ForgetfulDuck/MIP-Watch/MIP-STM32/Core/Inc/lsm6dsr_reg.h

/**
  ******************************************************************************
  * @file    lsm6dsr_reg.h
  * @author  Sensor Solutions Software Team
  * @brief   This file contains all the functions prototypes for the
  *          lsm6dsr_reg.c driver.
  ******************************************************************************
  * @attention
  *
  * Copyright (c) 2021 STMicroelectronics.
  * All rights reserved.
  *
  * This software is licensed under terms that can be found in the LICENSE file
  * in the root directory of this software component.
  * If no LICENSE file comes with this software, it is provided AS-IS.
  *
  ******************************************************************************
  */

/* Define to prevent recursive inclusion -------------------------------------*/
#ifndef LSM6DSR_REGS_H
#define LSM6DSR_REGS_H

#ifdef __cplusplus
extern "C" {
#endif

/* Includes ------------------------------------------------------------------*/
#include <stdint.h>
#include <stddef.h>
#include <math.h>

/** @addtogroup LSM6DSR
  * @{
  *
  */

/** @defgroup  Endianness definitions
  * @{
  *
  */

#ifndef DRV_BYTE_ORDER
#ifndef __BYTE_ORDER__

#define DRV_LITTLE_ENDIAN 1234
#define DRV_BIG_ENDIAN    4321

/** if _BYTE_ORDER is not defined, choose the endianness of your architecture
  * by uncommenting the define which fits your platform endianness
  */
/* #define DRV_BYTE_ORDER    DRV_BIG_ENDIAN */
#define DRV_BYTE_ORDER    DRV_LITTLE_ENDIAN

#else /* defined __BYTE_ORDER__ */

#define DRV_LITTLE_ENDIAN  __ORDER_LITTLE_ENDIAN__
#define DRV_BIG_ENDIAN     __ORDER_BIG_ENDIAN__
#define DRV_BYTE_ORDER     __BYTE_ORDER__

#endif /* __BYTE_ORDER__*/
#endif /* DRV_BYTE_ORDER */

/**
  * @}
  *
  */

/** @defgroup STMicroelectronics sensors common types
  * @{
  *
  */

#ifndef MEMS_SHARED_TYPES
#define MEMS_SHARED_TYPES

typedef struct
{
#if DRV_BYTE_ORDER == DRV_LITTLE_ENDIAN
  uint8_t bit0       : 1;
  uint8_t bit1       : 1;
  uint8_t bit2       : 1;
  uint8_t bit3       : 1;
  uint8_t bit4       : 1;
  uint8_t bit5       : 1;
  uint8_t bit6       : 1;
  uint8_t bit7       : 1;
#elif DRV_BYTE_ORDER == DRV_BIG_ENDIAN
  uint8_t bit7       : 1;
  uint8_t bit6       : 1;
  uint8_t bit5       : 1;
  uint8_t bit4       : 1;
  uint8_t bit3       : 1;
  uint8_t bit2       : 1;
  uint8_t bit1       : 1;
  uint8_t bit0       : 1;
#endif /* DRV_BYTE_ORDER */
} bitwise_t;

#define PROPERTY_DISABLE                (0U)
#define PROPERTY_ENABLE                 (1U)

/** @addtogroup  Interfaces_Functions
  * @brief       This section provide a set of functions used to read and
  *              write a generic register of the device.
  *              MANDATORY: return 0 -> no Error.
  * @{
  *
  */

typedef int32_t (*stmdev_write_ptr)(void *, uint8_t, const uint8_t *, uint16_t);
typedef int32_t (*stmdev_read_ptr)(void *, uint8_t, uint8_t *, uint16_t);
typedef void (*stmdev_mdelay_ptr)(uint32_t millisec);

typedef struct
{
  /** Component mandatory fields **/
  stmdev_write_ptr  write_reg;
  stmdev_read_ptr   read_reg;
  /** Component optional fields **/
  stmdev_mdelay_ptr   mdelay;
  /** Customizable optional pointer **/
  void *handle;

  /** private data **/
  void *priv_data;
} stmdev_ctx_t;

/**
  * @}
  *
  */

#endif /* MEMS_SHARED_TYPES */

/** @defgroup LSM6DSR Infos
  * @{
  *
  */

/** I2C Device Address 8 bit format  if SA0=0 -> 6A becomes D4 if SA0=1 -> 6B becomes D6**/
#define LSM6DSR_I2C_ADD_L                    0xD4U
#define LSM6DSR_I2C_ADD_H                    0xD6U

/** Device Identification (Who am I) **/
#define LSM6DSR_ID                           0x6BU

/**
  * @}
  *
  */

#define LSM6DSR_FUNC_CFG_ACCESS              0x01U
typedef struct
{
#if DRV_BYTE_ORDER == DRV_LITTLE_ENDIAN
  uint8_t not_used_01              : 6;
  uint8_t reg_access               : 2; /* shub_reg_access + func_cfg_access */
#elif DRV_BYTE_ORDER == DRV_BIG_ENDIAN
  uint8_t reg_access               : 2; /* shub_reg_access + func_cfg_access */
  uint8_t not_used_01              : 6;
#endif /* DRV_BYTE_ORDER */
} lsm6dsr_func_cfg_access_t;

#define LSM6DSR_PIN_CTRL                     0x02U
typedef struct
{
#if DRV_BYTE_ORDER == DRV_LITTLE_ENDIAN
  uint8_t not_used_01              : 6;
  uint8_t sdo_pu_en                : 1;
  uint8_t ois_pu_dis               : 1;
#elif DRV_BYTE_ORDER == DRV_BIG_ENDIAN
  uint8_t ois_pu_dis               : 1;
  uint8_t sdo_pu_en                : 1;
  uint8_t not_used_01              : 6;
#endif /* DRV_BYTE_ORDER */
} lsm6dsr_pin_ctrl_t;

#define LSM6DSR_S4S_TPH_L                    0x04U
typedef struct
{
#if DRV_BYTE_ORDER == DRV_LITTLE_ENDIAN
  uint8_t tph_l                    : 7;
  uint8_t tph_h_sel                : 1;
#elif DRV_BYTE_ORDER == DRV_BIG_ENDIAN
  uint8_t tph_h_sel                : 1;
  uint8_t tph_l                    : 7;
#endif /* DRV_BYTE_ORDER */
} lsm6dsr_s4s_tph_l_t;

#define LSM6DSR_S4S_TPH_H                    0x05U
typedef struct
{
  uint8_t tph_h                    : 8;
} lsm6dsr_s4s_tph_h_t;

#define LSM6DSR_S4S_RR                       0x06U
typedef struct
{
#if DRV_BYTE_ORDER == DRV_LITTLE_ENDIAN
  uint8_t rr                       : 2;
  uint8_t not_used_01              : 6;
#elif DRV_BYTE_ORDER == DRV_BIG_ENDIAN
  uint8_t not_used_01              : 6;
  uint8_t rr                       : 2;
#endif /* DRV_BYTE_ORDER */
} lsm6dsr_s4s_rr_t;

#define LSM6DSR_FIFO_CTRL1                   0x07U
typedef struct
{
  uint8_t wtm                      : 8;
} lsm6dsr_fifo_ctrl1_t;

#define LSM6DSR_FIFO_CTRL2                   0x08U
typedef struct
{
#if DRV_BYTE_ORDER == DRV_LITTLE_ENDIAN
  uint8_t wtm                      : 1;
  uint8_t uncoptr_rate             : 2;
  uint8_t not_used_01              : 1;
  uint8_t odrchg_en                : 1;
  uint8_t not_used_02              : 1;
  uint8_t fifo_compr_rt_en         : 1;
  uint8_t stop_on_wtm              : 1;
#elif DRV_BYTE_ORDER == DRV_BIG_ENDIAN
  uint8_t stop_on_wtm              : 1;
  uint8_t fifo_compr_rt_en         : 1;
  uint8_t not_used_02              : 1;
  uint8_t odrchg_en                : 1;
  uint8_t not_used_01              : 1;
  uint8_t uncoptr_rate             : 2;
  uint8_t wtm                      : 1;
#endif /* DRV_BYTE_ORDER */
} lsm6dsr_fifo_ctrl2_t;

#define LSM6DSR_FIFO_CTRL3                   0x09U
typedef struct
{
#if DRV_BYTE_ORDER == DRV_LITTLE_ENDIAN
  uint8_t bdr_xl                   : 4;
  uint8_t bdr_gy                   : 4;
#elif DRV_BYTE_ORDER == DRV_BIG_ENDIAN
  uint8_t bdr_gy                   : 4;
  uint8_t bdr_xl                   : 4;
#endif /* DRV_BYTE_ORDER */
} lsm6dsr_fifo_ctrl3_t;

#define LSM6DSR_FIFO_CTRL4                   0x0AU
typedef struct
{
#if DRV_BYTE_ORDER == DRV_LITTLE_ENDIAN
  uint8_t fifo_mode                : 3;
  uint8_t not_used_01              : 1;
  uint8_t odr_t_batch              : 2;
  uint8_t odr_ts_batch             : 2;
#elif DRV_BYTE_ORDER == DRV_BIG_ENDIAN
  uint8_t odr_ts_batch             : 2;
  uint8_t odr_t_batch              : 2;
  uint8_t not_used_01              : 1;
  uint8_t fifo_mode                : 3;
#endif /* DRV_BYTE_ORDER */
} lsm6dsr_fifo_ctrl4_t;

#define LSM6DSR_COUNTER_BDR_REG1             0x0BU
typedef struct
{
#if DRV_BYTE_ORDER == DRV_LITTLE_ENDIAN
  uint8_t cnt_bdr_th               : 3;
  uint8_t not_used_01              : 2;
  uint8_t trig_counter_bdr         : 1;
  uint8_t rst_counter_bdr          : 1;
  uint8_t dataready_pulsed         : 1;
#elif DRV_BYTE_ORDER == DRV_BIG_ENDIAN
  uint8_t dataready_pulsed         : 1;
  uint8_t rst_counter_bdr          : 1;
  uint8_t trig_counter_bdr         : 1;
  uint8_t not_used_01              : 2;
  uint8_t cnt_bdr_th               : 3;
#endif /* DRV_BYTE_ORDER */
} lsm6dsr_counter_bdr_reg1_t;

#define LSM6DSR_COUNTER_BDR_REG2             0x0CU
typedef struct
{
  uint8_t cnt_bdr_th               : 8;
} lsm6dsr_counter_bdr_reg2_t;

#define LSM6DSR_INT1_CTRL                    0x0DU
typedef struct
{
#if DRV_BYTE_ORDER == DRV_LITTLE_ENDIAN
  uint8_t int1_drdy_xl             : 1;
  uint8_t int1_drdy_g              : 1;
  uint8_t int1_boot                : 1;
  uint8_t int1_fifo_th             : 1;
  uint8_t int1_fifo_ovr            : 1;
  uint8_t int1_fifo_full           : 1;
  uint8_t int1_cnt_bdr             : 1;
  uint8_t den_drdy_flag            : 1;
#elif DRV_BYTE_ORDER == DRV_BIG_ENDIAN
  uint8_t den_drdy_flag            : 1;
  uint8_t int1_cnt_bdr             : 1;
  uint8_t int1_fifo_full           : 1;
  uint8_t int1_fifo_ovr            : 1;
  uint8_t int1_fifo_th             : 1;
  uint8_t int1_boot                : 1;
  uint8_t int1_drdy_g              : 1;
  uint8_t int1_drdy_xl             : 1;
#endif /* DRV_BYTE_ORDER */
} lsm6dsr_int1_ctrl_t;

#define LSM6DSR_INT2_CTRL                    0x0EU
typedef struct
{
#if DRV_BYTE_ORDER == DRV_LITTLE_ENDIAN
  uint8_t int2_drdy_xl             : 1;
  uint8_t int2_drdy_g              : 1;
  uint8_t int2_drdy_temp           : 1;
  uint8_t int2_fifo_th             : 1;
  uint8_t int2_fifo_ovr            : 1;
  uint8_t int2_fifo_full           : 1;
  uint8_t int2_cnt_bdr             : 1;
  uint8_t not_used_01              : 1;
#elif DRV_BYTE_ORDER == DRV_BIG_ENDIAN
  uint8_t not_used_01              : 1;
  uint8_t int2_cnt_bdr             : 1;
  uint8_t int2_fifo_full           : 1;
  uint8_t int2_fifo_ovr            : 1;
  uint8_t int2_fifo_th             : 1;
  uint8_t int2_drdy_temp           : 1;
  uint8_t int2_drdy_g              : 1;
  uint8_t int2_drdy_xl             : 1;
#endif /* DRV_BYTE_ORDER */
} lsm6dsr_int2_ctrl_t;

#define LSM6DSR_WHO_AM_I                     0x0FU
#define LSM6DSR_CTRL1_XL                     0x10U
typedef struct
{
#if DRV_BYTE_ORDER == DRV_LITTLE_ENDIAN
  uint8_t not_used_01              : 1;
  uint8_t lpf2_xl_en               : 1;
  uint8_t fs_xl                    : 2;
  uint8_t odr_xl                   : 4;
#elif DRV_BYTE_ORDER == DRV_BIG_ENDIAN
  uint8_t odr_xl                   : 4;
  uint8_t fs_xl                    : 2;
  uint8_t lpf2_xl_en               : 1;
  uint8_t not_used_01              : 1;
#endif /* DRV_BYTE_ORDER */
} lsm6dsr_ctrl1_xl_t;

#define LSM6DSR_CTRL2_G                      0x11U
typedef struct
{
#if DRV_BYTE_ORDER == DRV_LITTLE_ENDIAN
  uint8_t fs_g                     : 4; /* fs_4000 + fs_125 + fs_g */
  uint8_t odr_g                    : 4;
#elif DRV_BYTE_ORDER == DRV_BIG_ENDIAN
  uint8_t odr_g                    : 4;
  uint8_t fs_g                     : 4; /* fs_4000 + fs_125 + fs_g */
#endif /* DRV_BYTE_ORDER */
} lsm6dsr_ctrl2_g_t;

#define LSM6DSR_CTRL3_C                      0x12U
typedef struct
{
#if DRV_BYTE_ORDER == DRV_LITTLE_ENDIAN
  uint8_t sw_reset                 : 1;
  uint8_t not_used_01              : 1;
  uint8_t if_inc                   : 1;
  uint8_t sim                      : 1;
  uint8_t pp_od                    : 1;
  uint8_t h_lactive                : 1;
  uint8_t bdu                      : 1;
  uint8_t boot                     : 1;
#elif DRV_BYTE_ORDER == DRV_BIG_ENDIAN
  uint8_t boot                     : 1;
  uint8_t bdu                      : 1;
  uint8_t h_lactive                : 1;
  uint8_t pp_od                    : 1;
  uint8_t sim                      : 1;
  uint8_t if_inc                   : 1;
  uint8_t not_used_01              : 1;
  uint8_t sw_reset                 : 1;
#endif /* DRV_BYTE_ORDER */
} lsm6dsr_ctrl3_c_t;

#define LSM6DSR_CTRL4_C                      0x13U
typedef struct
{
#if DRV_BYTE_ORDER == DRV_LITTLE_ENDIAN
  uint8_t not_used_01              : 1;
  uint8_t lpf1_sel_g               : 1;
  uint8_t i2c_disable              : 1;
  uint8_t drdy_mask                : 1;
  uint8_t not_used_02              : 1;
  uint8_t int2_on_int1             : 1;
  uint8_t sleep_g                  : 1;
  uint8_t not_used_03              : 1;
#elif DRV_BYTE_ORDER == DRV_BIG_ENDIAN
  uint8_t not_used_03              : 1;
  uint8_t sleep_g                  : 1;
  uint8_t int2_on_int1             : 1;
  uint8_t not_used_02              : 1;
  uint8_t drdy_mask                : 1;
  uint8_t i2c_disable              : 1;
  uint8_t lpf1_sel_g               : 1;
  uint8_t not_used_01              : 1;
#endif /* DRV_BYTE_ORDER */
} lsm6dsr_ctrl4_c_t;

#define LSM6DSR_CTRL5_C                      0x14U
typedef struct
{
#if DRV_BYTE_ORDER == DRV_LITTLE_ENDIAN
  uint8_t st_xl                    : 2;
  uint8_t st_g                     : 2;
  uint8_t not_used_01              : 1;
  uint8_t rounding                 : 2;
  uint8_t not_used_02              : 1;
#elif DRV_BYTE_ORDER == DRV_BIG_ENDIAN
  uint8_t not_used_02              : 1;
  uint8_t rounding                 : 2;
  uint8_t not_used_01              : 1;
  uint8_t st_g                     : 2;
  uint8_t st_xl                    : 2;
#endif /* DRV_BYTE_ORDER */
} lsm6dsr_ctrl5_c_t;

#define LSM6DSR_CTRL6_C                      0x15U
typedef struct
{
#if DRV_BYTE_ORDER == DRV_LITTLE_ENDIAN
  uint8_t ftype                    : 3;
  uint8_t usr_off_w                : 1;
  uint8_t xl_hm_mode               : 1;
  uint8_t den_mode                 : 3;   /* trig_en + lvl1_en + lvl2_en */
#elif DRV_BYTE_ORDER == DRV_BIG_ENDIAN
  uint8_t den_mode                 : 3;   /* trig_en + lvl1_en + lvl2_en */
  uint8_t xl_hm_mode               : 1;
  uint8_t usr_off_w                : 1;
  uint8_t ftype                    : 3;
#endif /* DRV_BYTE_ORDER */
} lsm6dsr_ctrl6_c_t;

#define LSM6DSR_CTRL7_G                      0x16U
typedef struct
{
#if DRV_BYTE_ORDER == DRV_LITTLE_ENDIAN
  uint8_t ois_on                   : 1;
  uint8_t usr_off_on_out           : 1;
  uint8_t ois_on_en                : 1;
  uint8_t not_used_01              : 1;
  uint8_t hpm_g                    : 2;
  uint8_t hp_en_g                  : 1;
  uint8_t g_hm_mode                : 1;
#elif DRV_BYTE_ORDER == DRV_BIG_ENDIAN
  uint8_t g_hm_mode                : 1;
  uint8_t hp_en_g                  : 1;
  uint8_t hpm_g                    : 2;
  uint8_t not_used_01              : 1;
  uint8_t ois_on_en                : 1;
  uint8_t usr_off_on_out           : 1;
  uint8_t ois_on                   : 1;
#endif /* DRV_BYTE_ORDER */
} lsm6dsr_ctrl7_g_t;

#define LSM6DSR_CTRL8_XL                     0x17U
typedef struct
{
#if DRV_BYTE_ORDER == DRV_LITTLE_ENDIAN
  uint8_t low_pass_on_6d           : 1;
  uint8_t not_used_01              : 1;
  uint8_t hp_slope_xl_en           : 1;
  uint8_t fastsettl_mode_xl        : 1;
  uint8_t hp_ref_mode_xl           : 1;
  uint8_t hpcf_xl                  : 3;
#elif DRV_BYTE_ORDER == DRV_BIG_ENDIAN
  uint8_t hpcf_xl                  : 3;
  uint8_t hp_ref_mode_xl           : 1;
  uint8_t fastsettl_mode_xl        : 1;
  uint8_t hp_slope_xl_en           : 1;
  uint8_t not_used_01              : 1;
  uint8_t low_pass_on_6d           : 1;
#endif /* DRV_BYTE_ORDER */
} lsm6dsr_ctrl8_xl_t;

#define LSM6DSR_CTRL9_XL                     0x18U
typedef struct
{
#if DRV_BYTE_ORDER == DRV_LITTLE_ENDIAN
  uint8_t not_used_01              : 1;
  uint8_t i3c_disable              : 1;
  uint8_t den_lh                   : 1;
  uint8_t den_xl_g                 : 2;   /* den_xl_en + den_xl_g */
  uint8_t den_z                    : 1;
  uint8_t den_y                    : 1;
  uint8_t den_x                    : 1;
#elif DRV_BYTE_ORDER == DRV_BIG_ENDIAN
  uint8_t den_x                    : 1;
  uint8_t den_y                    : 1;
  uint8_t den_z                    : 1;
  uint8_t den_xl_g                 : 2;   /* den_xl_en + den_xl_g */
  uint8_t den_lh                   : 1;
  uint8_t i3c_disable              : 1;
  uint8_t not_used_01              : 1;
#endif /* DRV_BYTE_ORDER */
} lsm6dsr_ctrl9_xl_t;

#define LSM6DSR_CTRL10_C                     0x19U
typedef struct
{
#if DRV_BYTE_ORDER == DRV_LITTLE_ENDIAN
  uint8_t not_used_01              : 5;
  uint8_t timestamp_en             : 1;
  uint8_t not_used_02              : 2;
#elif DRV_BYTE_ORDER == DRV_BIG_ENDIAN
  uint8_t not_used_02              : 2;
  uint8_t timestamp_en             : 1;
  uint8_t not_used_01              : 5;
#endif /* DRV_BYTE_ORDER */
} lsm6dsr_ctrl10_c_t;

#define LSM6DSR_ALL_INT_SRC                  0x1AU
typedef struct
{
#if DRV_BYTE_ORDER == DRV_LITTLE_ENDIAN
  uint8_t ff_ia                    : 1;
  uint8_t wu_ia                    : 1;
  uint8_t single_tap               : 1;
  uint8_t double_tap               : 1;
  uint8_t d6d_ia                   : 1;
  uint8_t sleep_change_ia          : 1;
  uint8_t not_used_01              : 1;
  uint8_t timestamp_endcount       : 1;
#elif DRV_BYTE_ORDER == DRV_BIG_ENDIAN
  uint8_t timestamp_endcount       : 1;
  uint8_t not_used_01              : 1;
  uint8_t sleep_change_ia          : 1;
  uint8_t d6d_ia                   : 1;
  uint8_t double_tap               : 1;
  uint8_t single_tap               : 1;
  uint8_t wu_ia                    : 1;
  uint8_t ff_ia                    : 1;
#endif /* DRV_BYTE_ORDER */
} lsm6dsr_all_int_src_t;

#define LSM6DSR_WAKE_UP_SRC                  0x1BU
typedef struct
{
#if DRV_BYTE_ORDER == DRV_LITTLE_ENDIAN
  uint8_t z_wu                     : 1;
  uint8_t y_wu                     : 1;
  uint8_t x_wu                     : 1;
  uint8_t wu_ia                    : 1;
  uint8_t sleep_state              : 1;
  uint8_t ff_ia                    : 1;
  uint8_t sleep_change_ia          : 1;
  uint8_t not_used_01              : 1;
#elif DRV_BYTE_ORDER == DRV_BIG_ENDIAN
  uint8_t not_used_01              : 1;
  uint8_t sleep_change_ia          : 1;
  uint8_t ff_ia                    : 1;
  uint8_t sleep_state              : 1;
  uint8_t wu_ia                    : 1;
  uint8_t x_wu                     : 1;
  uint8_t y_wu                     : 1;
  uint8_t z_wu                     : 1;
#endif /* DRV_BYTE_ORDER */
} lsm6dsr_wake_up_src_t;

#define LSM6DSR_TAP_SRC                      0x1CU
typedef struct
{
#if DRV_BYTE_ORDER == DRV_LITTLE_ENDIAN
  uint8_t z_tap                    : 1;
  uint8_t y_tap                    : 1;
  uint8_t x_tap                    : 1;
  uint8_t tap_sign                 : 1;
  uint8_t double_tap               : 1;
  uint8_t single_tap               : 1;
  uint8_t tap_ia                   : 1;
  uint8_t not_used_01              : 1;
#elif DRV_BYTE_ORDER == DRV_BIG_ENDIAN
  uint8_t not_used_01              : 1;
  uint8_t tap_ia                   : 1;
  uint8_t single_tap               : 1;
  uint8_t double_tap               : 1;
  uint8_t tap_sign                 : 1;
  uint8_t x_tap                    : 1;
  uint8_t y_tap                    : 1;
  uint8_t z_tap                    : 1;
#endif /* DRV_BYTE_ORDER */
} lsm6dsr_tap_src_t;

#define LSM6DSR_D6D_SRC                      0x1DU
typedef struct
{
#if DRV_BYTE_ORDER == DRV_LITTLE_ENDIAN
  uint8_t xl                       : 1;
  uint8_t xh                       : 1;
  uint8_t yl                       : 1;
  uint8_t yh                       : 1;
  uint8_t zl                       : 1;
  uint8_t zh                       : 1;
  uint8_t d6d_ia                   : 1;
  uint8_t den_drdy                 : 1;
#elif DRV_BYTE_ORDER == DRV_BIG_ENDIAN
  uint8_t den_drdy                 : 1;
  uint8_t d6d_ia                   : 1;
  uint8_t zh                       : 1;
  uint8_t zl                       : 1;
  uint8_t yh                       : 1;
  uint8_t yl                       : 1;
  uint8_t xh                       : 1;
  uint8_t xl                       : 1;
#endif /* DRV_BYTE_ORDER */
} lsm6dsr_d6d_src_t;

#define LSM6DSR_STATUS_REG                   0x1EU
typedef struct
{
#if DRV_BYTE_ORDER == DRV_LITTLE_ENDIAN
  uint8_t xlda                     : 1;
  uint8_t gda                      : 1;
  uint8_t tda                      : 1;
  uint8_t not_used_01              : 5;
#elif DRV_BYTE_ORDER == DRV_BIG_ENDIAN
  uint8_t not_used_01              : 5;
  uint8_t tda                      : 1;
  uint8_t gda                      : 1;
  uint8_t xlda                     : 1;
#endif /* DRV_BYTE_ORDER */
} lsm6dsr_status_reg_t;

#define LSM6DSR_STATUS_SPIAUX                0x1EU
typedef struct
{
#if DRV_BYTE_ORDER == DRV_LITTLE_ENDIAN
  uint8_t xlda                     : 1;
  uint8_t gda                      : 1;
  uint8_t gyro_settling            : 1;
  uint8_t not_used_01              : 5;
#elif DRV_BYTE_ORDER == DRV_BIG_ENDIAN
  uint8_t not_used_01              : 5;
  uint8_t gyro_settling            : 1;
  uint8_t gda                      : 1;
  uint8_t xlda                     : 1;
#endif /* DRV_BYTE_ORDER */
} lsm6dsr_status_spiaux_t;

#define LSM6DSR_OUT_TEMP_L                   0x20U
#define LSM6DSR_OUT_TEMP_H                   0x21U
#define LSM6DSR_OUTX_L_G                     0x22U
#define LSM6DSR_OUTX_H_G                     0x23U
#define LSM6DSR_OUTY_L_G                     0x24U
#define LSM6DSR_OUTY_H_G                     0x25U
#define LSM6DSR_OUTZ_L_G                     0x26U
#define LSM6DSR_OUTZ_H_G                     0x27U
#define LSM6DSR_OUTX_L_A                     0x28U
#define LSM6DSR_OUTX_H_A                     0x29U
#define LSM6DSR_OUTY_L_A                     0x2AU
#define LSM6DSR_OUTY_H_A                     0x2BU
#define LSM6DSR_OUTZ_L_A                     0x2CU
#define LSM6DSR_OUTZ_H_A                     0x2DU

#define LSM6DSR_EMB_FUNC_STATUS_MAINPAGE     0x35U
typedef struct
{
#if DRV_BYTE_ORDER == DRV_LITTLE_ENDIAN
  uint8_t not_used_01             : 3;
  uint8_t is_step_det             : 1;
  uint8_t is_tilt                 : 1;
  uint8_t is_sigmot               : 1;
  uint8_t not_used_02             : 1;
  uint8_t is_fsm_lc               : 1;
#elif DRV_BYTE_ORDER == DRV_BIG_ENDIAN
  uint8_t is_fsm_lc               : 1;
  uint8_t not_used_02             : 1;
  uint8_t is_sigmot               : 1;
  uint8_t is_tilt                 : 1;
  uint8_t is_step_det             : 1;
  uint8_t not_used_01             : 3;
#endif /* DRV_BYTE_ORDER */
} lsm6dsr_emb_func_status_mainpage_t;

#define LSM6DSR_FSM_STATUS_A_MAINPAGE        0x36U
typedef struct
{
#if DRV_BYTE_ORDER == DRV_LITTLE_ENDIAN
  uint8_t is_fsm1                 : 1;
  uint8_t is_fsm2                 : 1;
  uint8_t is_fsm3                 : 1;
  uint8_t is_fsm4                 : 1;
  uint8_t is_fsm5                 : 1;
  uint8_t is_fsm6                 : 1;
  uint8_t is_fsm7                 : 1;
  uint8_t is_fsm8                 : 1;
#elif DRV_BYTE_ORDER == DRV_BIG_ENDIAN
  uint8_t is_fsm8                 : 1;
  uint8_t is_fsm7                 : 1;
  uint8_t is_fsm6                 : 1;
  uint8_t is_fsm5                 : 1;
  uint8_t is_fsm4                 : 1;
  uint8_t is_fsm3                 : 1;
  uint8_t is_fsm2                 : 1;
  uint8_t is_fsm1                 : 1;
#endif /* DRV_BYTE_ORDER */
} lsm6dsr_fsm_status_a_mainpage_t;

#define LSM6DSR_FSM_STATUS_B_MAINPAGE        0x37U
typedef struct
{
#if DRV_BYTE_ORDER == DRV_LITTLE_ENDIAN
  uint8_t is_fsm9                 : 1;
  uint8_t is_fsm10                : 1;
  uint8_t is_fsm11                : 1;
  uint8_t is_fsm12                : 1;
  uint8_t is_fsm13                : 1;
  uint8_t is_fsm14                : 1;
  uint8_t is_fsm15                : 1;
  uint8_t is_fsm16                : 1;
#elif DRV_BYTE_ORDER == DRV_BIG_ENDIAN
  uint8_t is_fsm16                : 1;
  uint8_t is_fsm15                : 1;
  uint8_t is_fsm14                : 1;
  uint8_t is_fsm13                : 1;
  uint8_t is_fsm12                : 1;
  uint8_t is_fsm11                : 1;
  uint8_t is_fsm10                : 1;
  uint8_t is_fsm9                 : 1;
#endif /* DRV_BYTE_ORDER */
} lsm6dsr_fsm_status_b_mainpage_t;

#define LSM6DSR_STATUS_MASTER_MAINPAGE       0x39U
typedef struct
{
#if DRV_BYTE_ORDER == DRV_LITTLE_ENDIAN
  uint8_t sens_hub_endop          : 1;
  uint8_t not_used_01             : 2;
  uint8_t slave0_nack             : 1;
  uint8_t slave1_nack             : 1;
  uint8_t slave2_nack             : 1;
  uint8_t slave3_nack             : 1;
  uint8_t wr_once_done            : 1;
#elif DRV_BYTE_ORDER == DRV_BIG_ENDIAN
  uint8_t wr_once_done            : 1;
  uint8_t slave3_nack             : 1;
  uint8_t slave2_nack             : 1;
  uint8_t slave1_nack             : 1;
  uint8_t slave0_nack             : 1;
  uint8_t not_used_01             : 2;
  uint8_t sens_hub_endop          : 1;
#endif /* DRV_BYTE_ORDER */
} lsm6dsr_status_master_mainpage_t;

#define LSM6DSR_FIFO_STATUS1                 0x3AU
typedef struct
{
  uint8_t diff_fifo                : 8;
} lsm6dsr_fifo_status1_t;

#define LSM6DSR_FIFO_STATUS2                 0x3BU
typedef struct
{
#if DRV_BYTE_ORDER == DRV_LITTLE_ENDIAN
  uint8_t diff_fifo                : 2;
  uint8_t not_used_01              : 1;
  uint8_t over_run_latched         : 1;
  uint8_t counter_bdr_ia           : 1;
  uint8_t fifo_full_ia             : 1;
  uint8_t fifo_ovr_ia              : 1;
  uint8_t fifo_wtm_ia              : 1;
#elif DRV_BYTE_ORDER == DRV_BIG_ENDIAN
  uint8_t fifo_wtm_ia              : 1;
  uint8_t fifo_ovr_ia              : 1;
  uint8_t fifo_full_ia             : 1;
  uint8_t counter_bdr_ia           : 1;
  uint8_t over_run_latched         : 1;
  uint8_t not_used_01              : 1;
  uint8_t diff_fifo                : 2;
#endif /* DRV_BYTE_ORDER */
} lsm6dsr_fifo_status2_t;

#define LSM6DSR_TIMESTAMP0                   0x40U
#define LSM6DSR_TIMESTAMP1                   0x41U
#define LSM6DSR_TIMESTAMP2                   0x42U
#define LSM6DSR_TIMESTAMP3                   0x43U
#define LSM6DSR_TAP_CFG0                     0x56U
typedef struct
{
#if DRV_BYTE_ORDER == DRV_LITTLE_ENDIAN
  uint8_t lir                      : 1;
  uint8_t tap_z_en                 : 1;
  uint8_t tap_y_en                 : 1;
  uint8_t tap_x_en                 : 1;
  uint8_t slope_fds                : 1;
  uint8_t sleep_status_on_int      : 1;
  uint8_t int_clr_on_read          : 1;
  uint8_t not_used_01              : 1;
#elif DRV_BYTE_ORDER == DRV_BIG_ENDIAN
  uint8_t not_used_01              : 1;
  uint8_t int_clr_on_read          : 1;
  uint8_t sleep_status_on_int      : 1;
  uint8_t slope_fds                : 1;
  uint8_t tap_x_en                 : 1;
  uint8_t tap_y_en                 : 1;
  uint8_t tap_z_en                 : 1;
  uint8_t lir                      : 1;
#endif /* DRV_BYTE_ORDER */
} lsm6dsr_tap_cfg0_t;

#define LSM6DSR_TAP_CFG1                     0x57U
typedef struct
{
#if DRV_BYTE_ORDER == DRV_LITTLE_ENDIAN
  uint8_t tap_ths_x                : 5;
  uint8_t tap_priority             : 3;
#elif DRV_BYTE_ORDER == DRV_BIG_ENDIAN
  uint8_t tap_priority             : 3;
  uint8_t tap_ths_x                : 5;
#endif /* DRV_BYTE_ORDER */
} lsm6dsr_tap_cfg1_t;

#define LSM6DSR_TAP_CFG2                     0x58U
typedef struct
{
#if DRV_BYTE_ORDER == DRV_LITTLE_ENDIAN
  uint8_t tap_ths_y                : 5;
  uint8_t inact_en                 : 2;
  uint8_t interrupts_enable        : 1;
#elif DRV_BYTE_ORDER == DRV_BIG_ENDIAN
  uint8_t interrupts_enable        : 1;
  uint8_t inact_en                 : 2;
  uint8_t tap_ths_y                : 5;
#endif /* DRV_BYTE_ORDER */
} lsm6dsr_tap_cfg2_t;

#define LSM6DSR_TAP_THS_6D                   0x59U
typedef struct
{
#if DRV_BYTE_ORDER == DRV_LITTLE_ENDIAN
  uint8_t tap_ths_z                : 5;
  uint8_t sixd_ths                 : 2;
  uint8_t d4d_en                   : 1;
#elif DRV_BYTE_ORDER == DRV_BIG_ENDIAN
  uint8_t d4d_en                   : 1;
  uint8_t sixd_ths                 : 2;
  uint8_t tap_ths_z                : 5;
#endif /* DRV_BYTE_ORDER */
} lsm6dsr_tap_ths_6d_t;

#define LSM6DSR_INT_DUR2                     0x5AU
typedef struct
{
#if DRV_BYTE_ORDER == DRV_LITTLE_ENDIAN
  uint8_t shock                    : 2;
  uint8_t quiet                    : 2;
  uint8_t dur                      : 4;
#elif DRV_BYTE_ORDER == DRV_BIG_ENDIAN
  uint8_t dur                      : 4;
  uint8_t quiet                    : 2;
  uint8_t shock                    : 2;
#endif /* DRV_BYTE_ORDER */
} lsm6dsr_int_dur2_t;

#define LSM6DSR_WAKE_UP_THS                  0x5BU
typedef struct
{
#if DRV_BYTE_ORDER == DRV_LITTLE_ENDIAN
  uint8_t wk_ths                   : 6;
  uint8_t usr_off_on_wu            : 1;
  uint8_t single_double_tap        : 1;
#elif DRV_BYTE_ORDER == DRV_BIG_ENDIAN
  uint8_t single_double_tap        : 1;
  uint8_t usr_off_on_wu            : 1;
  uint8_t wk_ths                   : 6;
#endif /* DRV_BYTE_ORDER */
} lsm6dsr_wake_up_ths_t;

#define LSM6DSR_WAKE_UP_DUR                  0x5CU
typedef struct
{
#if DRV_BYTE_ORDER == DRV_LITTLE_ENDIAN
  uint8_t sleep_dur                : 4;
  uint8_t wake_ths_w               : 1;
  uint8_t wake_dur                 : 2;
  uint8_t ff_dur                   : 1;
#elif DRV_BYTE_ORDER == DRV_BIG_ENDIAN
  uint8_t ff_dur                   : 1;
  uint8_t wake_dur                 : 2;
  uint8_t wake_ths_w               : 1;
  uint8_t sleep_dur                : 4;
#endif /* DRV_BYTE_ORDER */
} lsm6dsr_wake_up_dur_t;

#define LSM6DSR_FREE_FALL                    0x5DU
typedef struct
{
#if DRV_BYTE_ORDER == DRV_LITTLE_ENDIAN
  uint8_t ff_ths                   : 3;
  uint8_t ff_dur                   : 5;
#elif DRV_BYTE_ORDER == DRV_BIG_ENDIAN
  uint8_t ff_dur                   : 5;
  uint8_t ff_ths                   : 3;
#endif /* DRV_BYTE_ORDER */
} lsm6dsr_free_fall_t;

#define LSM6DSR_MD1_CFG                      0x5EU
typedef struct
{
#if DRV_BYTE_ORDER == DRV_LITTLE_ENDIAN
  uint8_t int1_shub                : 1;
  uint8_t int1_emb_func            : 1;
  uint8_t int1_6d                  : 1;
  uint8_t int1_double_tap          : 1;
  uint8_t int1_ff                  : 1;
  uint8_t int1_wu                  : 1;
  uint8_t int1_single_tap          : 1;
  uint8_t int1_sleep_change        : 1;
#elif DRV_BYTE_ORDER == DRV_BIG_ENDIAN
  uint8_t int1_sleep_change        : 1;
  uint8_t int1_single_tap          : 1;
  uint8_t int1_wu                  : 1;
  uint8_t int1_ff                  : 1;
  uint8_t int1_double_tap          : 1;
  uint8_t int1_6d                  : 1;
  uint8_t int1_emb_func            : 1;
  uint8_t int1_shub                : 1;
#endif /* DRV_BYTE_ORDER */
} lsm6dsr_md1_cfg_t;

#define LSM6DSR_MD2_CFG                      0x5FU
typedef struct
{
#if DRV_BYTE_ORDER == DRV_LITTLE_ENDIAN
  uint8_t int2_timestamp           : 1;
  uint8_t int2_emb_func            : 1;
  uint8_t int2_6d                  : 1;
  uint8_t int2_double_tap          : 1;
  uint8_t int2_ff                  : 1;
  uint8_t int2_wu                  : 1;
  uint8_t int2_single_tap          : 1;
  uint8_t int2_sleep_change        : 1;
#elif DRV_BYTE_ORDER == DRV_BIG_ENDIAN
  uint8_t int2_sleep_change        : 1;
  uint8_t int2_single_tap          : 1;
  uint8_t int2_wu                  : 1;
  uint8_t int2_ff                  : 1;
  uint8_t int2_double_tap          : 1;
  uint8_t int2_6d                  : 1;
  uint8_t int2_emb_func            : 1;
  uint8_t int2_timestamp           : 1;
#endif /* DRV_BYTE_ORDER */
} lsm6dsr_md2_cfg_t;

#define LSM6DSR_S4S_ST_CMD_CODE              0x60U
typedef struct
{
  uint8_t s4s_st_cmd_code          : 8;
} lsm6dsr_s4s_st_cmd_code_t;

#define LSM6DSR_S4S_DT_REG                   0x61U
typedef struct
{
  uint8_t dt                       : 8;
} lsm6dsr_s4s_dt_reg_t;

#define LSM6DSR_I3C_BUS_AVB                  0x62U
typedef struct
{
#if DRV_BYTE_ORDER == DRV_LITTLE_ENDIAN
  uint8_t pd_dis_int1              : 1;
  uint8_t not_used_01              : 2;
  uint8_t i3c_bus_avb_sel          : 2;
  uint8_t not_used_02              : 3;
#elif DRV_BYTE_ORDER == DRV_BIG_ENDIAN
  uint8_t not_used_02              : 3;
  uint8_t i3c_bus_avb_sel          : 2;
  uint8_t not_used_01              : 2;
  uint8_t pd_dis_int1              : 1;
#endif /* DRV_BYTE_ORDER */
} lsm6dsr_i3c_bus_avb_t;

#define LSM6DSR_INTERNAL_FREQ_FINE           0x63U
typedef struct
{
  uint8_t freq_fine                : 8;
} lsm6dsr_internal_freq_fine_t;

#define LSM6DSR_INT_OIS                      0x6FU
typedef struct
{
#if DRV_BYTE_ORDER == DRV_LITTLE_ENDIAN
  uint8_t st_xl_ois                : 2;
  uint8_t not_used_01              : 3;
  uint8_t den_lh_ois               : 1;
  uint8_t lvl2_ois                 : 1;
  uint8_t int2_drdy_ois            : 1;
#elif DRV_BYTE_ORDER == DRV_BIG_ENDIAN
  uint8_t int2_drdy_ois            : 1;
  uint8_t lvl2_ois                 : 1;
  uint8_t den_lh_ois               : 1;
  uint8_t not_used_01              : 3;
  uint8_t st_xl_ois                : 2;
#endif /* DRV_BYTE_ORDER */
} lsm6dsr_int_ois_t;

#define LSM6DSR_CTRL1_OIS                    0x70U
typedef struct
{
#if DRV_BYTE_ORDER == DRV_LITTLE_ENDIAN
  uint8_t ois_en_spi2              : 1;
  uint8_t fs_125_ois               : 1;
  uint8_t fs_g_ois                 : 2;
  uint8_t mode4_en                 : 1;
  uint8_t sim_ois                  : 1;
  uint8_t lvl1_ois                 : 1;
  uint8_t not_used_01              : 1;
#elif DRV_BYTE_ORDER == DRV_BIG_ENDIAN
  uint8_t not_used_01              : 1;
  uint8_t lvl1_ois                 : 1;
  uint8_t sim_ois                  : 1;
  uint8_t mode4_en                 : 1;
  uint8_t fs_g_ois                 : 2;
  uint8_t fs_125_ois               : 1;
  uint8_t ois_en_spi2              : 1;
#endif /* DRV_BYTE_ORDER */
} lsm6dsr_ctrl1_ois_t;

#define LSM6DSR_CTRL2_OIS                    0x71U
typedef struct
{
#if DRV_BYTE_ORDER == DRV_LITTLE_ENDIAN
  uint8_t hp_en_ois                : 1;
  uint8_t ftype_ois                : 2;
  uint8_t not_used_01              : 1;
  uint8_t hpm_ois                  : 2;
  uint8_t not_used_02              : 2;
#elif DRV_BYTE_ORDER == DRV_BIG_ENDIAN
  uint8_t not_used_02              : 2;
  uint8_t hpm_ois                  : 2;
  uint8_t not_used_01              : 1;
  uint8_t ftype_ois                : 2;
  uint8_t hp_en_ois                : 1;
#endif /* DRV_BYTE_ORDER */
} lsm6dsr_ctrl2_ois_t;

#define LSM6DSR_CTRL3_OIS                    0x72U
typedef struct
{
#if DRV_BYTE_ORDER == DRV_LITTLE_ENDIAN
  uint8_t st_ois_clampdis          : 1;
  uint8_t st_ois                   : 2;
  uint8_t filter_xl_conf_ois       : 3;
  uint8_t fs_xl_ois                : 2;
#elif DRV_BYTE_ORDER == DRV_BIG_ENDIAN
  uint8_t fs_xl_ois                : 2;
  uint8_t filter_xl_conf_ois       : 3;
  uint8_t st_ois                   : 2;
  uint8_t st_ois_clampdis          : 1;
#endif /* DRV_BYTE_ORDER */
} lsm6dsr_ctrl3_ois_t;

#define LSM6DSR_X_OFS_USR                    0x73U
#define LSM6DSR_Y_OFS_USR                    0x74U
#define LSM6DSR_Z_OFS_USR                    0x75U
#define LSM6DSR_FIFO_DATA_OUT_TAG            0x78U
typedef struct
{
#if DRV_BYTE_ORDER == DRV_LITTLE_ENDIAN
  uint8_t tag_parity               : 1;
  uint8_t tag_cnt                  : 2;
  uint8_t tag_sensor               : 5;
#elif DRV_BYTE_ORDER == DRV_BIG_ENDIAN
  uint8_t tag_sensor               : 5;
  uint8_t tag_cnt                  : 2;
  uint8_t tag_parity               : 1;
#endif /* DRV_BYTE_ORDER */
} lsm6dsr_fifo_data_out_tag_t;

#define LSM6DSR_FIFO_DATA_OUT_X_L            0x79U
#define LSM6DSR_FIFO_DATA_OUT_X_H            0x7AU
#define LSM6DSR_FIFO_DATA_OUT_Y_L            0x7BU
#define LSM6DSR_FIFO_DATA_OUT_Y_H            0x7CU
#define LSM6DSR_FIFO_DATA_OUT_Z_L            0x7DU
#define LSM6DSR_FIFO_DATA_OUT_Z_H            0x7EU
#define LSM6DSR_PAGE_SEL                     0x02U
typedef struct
{
#if DRV_BYTE_ORDER == DRV_LITTLE_ENDIAN
  uint8_t not_used_01              : 4;
  uint8_t page_sel                 : 4;
#elif DRV_BYTE_ORDER == DRV_BIG_ENDIAN
  uint8_t page_sel                 : 4;
  uint8_t not_used_01              : 4;
#endif /* DRV_BYTE_ORDER */
} lsm6dsr_page_sel_t;

#define LSM6DSR_ADV_PEDO                     0x03U
typedef struct
{
#if DRV_BYTE_ORDER == DRV_LITTLE_ENDIAN
  uint8_t not_used_01              : 1;
  uint8_t pedo_fpr_adf_dis         : 1;
  uint8_t not_used_02              : 6;
#elif DRV_BYTE_ORDER == DRV_BIG_ENDIAN
  uint8_t not_used_02              : 6;
  uint8_t pedo_fpr_adf_dis         : 1;
  uint8_t not_used_01              : 1;
#endif /* DRV_BYTE_ORDER */
} lsm6dsr_adv_pedo_t;

#define LSM6DSR_EMB_FUNC_EN_A                0x04U
typedef struct
{
#if DRV_BYTE_ORDER == DRV_LITTLE_ENDIAN
  uint8_t not_used_01              : 3;
  uint8_t pedo_en                  : 1;
  uint8_t tilt_en                  : 1;
  uint8_t sign_motion_en           : 1;
  uint8_t not_used_02              : 2;
#elif DRV_BYTE_ORDER == DRV_BIG_ENDIAN
  uint8_t not_used_02              : 2;
  uint8_t sign_motion_en           : 1;
  uint8_t tilt_en                  : 1;
  uint8_t pedo_en                  : 1;
  uint8_t not_used_01              : 3;
#endif /* DRV_BYTE_ORDER */
} lsm6dsr_emb_func_en_a_t;

#define LSM6DSR_EMB_FUNC_EN_B                0x05U
typedef struct
{
#if DRV_BYTE_ORDER == DRV_LITTLE_ENDIAN
  uint8_t fsm_en                   : 1;
  uint8_t not_used_01              : 2;
  uint8_t fifo_compr_en            : 1;
  uint8_t pedo_adv_en              : 1;
  uint8_t not_used_02              : 3;
#elif DRV_BYTE_ORDER == DRV_BIG_ENDIAN
  uint8_t not_used_02              : 3;
  uint8_t pedo_adv_en              : 1;
  uint8_t fifo_compr_en            : 1;
  uint8_t not_used_01              : 2;
  uint8_t fsm_en                   : 1;
#endif /* DRV_BYTE_ORDER */
} lsm6dsr_emb_func_en_b_t;

#define LSM6DSR_PAGE_ADDRESS                 0x08U
typedef struct
{
  uint8_t page_addr                : 8;
} lsm6dsr_page_address_t;

#define LSM6DSR_PAGE_VALUE                   0x09U
typedef struct
{
  uint8_t page_value               : 8;
} lsm6dsr_page_value_t;

#define LSM6DSR_EMB_FUNC_INT1                0x0AU
typedef struct
{
#if DRV_BYTE_ORDER == DRV_LITTLE_ENDIAN
  uint8_t not_used_01              : 3;
  uint8_t int1_step_detector       : 1;
  uint8_t int1_tilt                : 1;
  uint8_t int1_sig_mot             : 1;
  uint8_t not_used_02              : 1;
  uint8_t int1_fsm_lc              : 1;
#elif DRV_BYTE_ORDER == DRV_BIG_ENDIAN
  uint8_t int1_fsm_lc              : 1;
  uint8_t not_used_02              : 1;
  uint8_t int1_sig_mot             : 1;
  uint8_t int1_tilt                : 1;
  uint8_t int1_step_detector       : 1;
  uint8_t not_used_01              : 3;
#endif /* DRV_BYTE_ORDER */
} lsm6dsr_emb_func_int1_t;

#define LSM6DSR_FSM_INT1_A                   0x0BU
typedef struct
{
#if DRV_BYTE_ORDER == DRV_LITTLE_ENDIAN
  uint8_t int1_fsm1                : 1;
  uint8_t int1_fsm2                : 1;
  uint8_t int1_fsm3                : 1;
  uint8_t int1_fsm4                : 1;
  uint8_t int1_fsm5                : 1;
  uint8_t int1_fsm6                : 1;
  uint8_t int1_fsm7                : 1;
  uint8_t int1_fsm8                : 1;
#elif DRV_BYTE_ORDER == DRV_BIG_ENDIAN
  uint8_t int1_fsm8                : 1;
  uint8_t int1_fsm7                : 1;
  uint8_t int1_fsm6                : 1;
  uint8_t int1_fsm5                : 1;
  uint8_t int1_fsm4                : 1;
  uint8_t int1_fsm3                : 1;
  uint8_t int1_fsm2                : 1;
  uint8_t int1_fsm1                : 1;
#endif /* DRV_BYTE_ORDER */
} lsm6dsr_fsm_int1_a_t;

#define LSM6DSR_FSM_INT1_B                   0x0CU
typedef struct
{
#if DRV_BYTE_ORDER == DRV_LITTLE_ENDIAN
  uint8_t int1_fsm9                : 1;
  uint8_t int1_fsm10               : 1;
  uint8_t int1_fsm11               : 1;
  uint8_t int1_fsm12               : 1;
  uint8_t int1_fsm13               : 1;
  uint8_t int1_fsm14               : 1;
  uint8_t int1_fsm15               : 1;
  uint8_t int1_fsm16               : 1;
#elif DRV_BYTE_ORDER == DRV_BIG_ENDIAN
  uint8_t int1_fsm16               : 1;
  uint8_t int1_fsm15               : 1;
  uint8_t int1_fsm14               : 1;
  uint8_t int1_fsm13               : 1;
  uint8_t int1_fsm12               : 1;
  uint8_t int1_fsm11               : 1;
  uint8_t int1_fsm10               : 1;
  uint8_t int1_fsm9                : 1;
#endif /* DRV_BYTE_ORDER */
} lsm6dsr_fsm_int1_b_t;

#define LSM6DSR_EMB_FUNC_INT2                0x0EU
typedef struct
{
#if DRV_BYTE_ORDER == DRV_LITTLE_ENDIAN
  uint8_t not_used_01              : 3;
  uint8_t int2_step_detector       : 1;
  uint8_t int2_tilt                : 1;
  uint8_t int2_sig_mot             : 1;
  uint8_t not_used_02              : 1;
  uint8_t int2_fsm_lc              : 1;
#elif DRV_BYTE_ORDER == DRV_BIG_ENDIAN
  uint8_t int2_fsm_lc              : 1;
  uint8_t not_used_02              : 1;
  uint8_t int2_sig_mot             : 1;
  uint8_t int2_tilt                : 1;
  uint8_t int2_step_detector       : 1;
  uint8_t not_used_01              : 3;
#endif /* DRV_BYTE_ORDER */
} lsm6dsr_emb_func_int2_t;

#define LSM6DSR_FSM_INT2_A                   0x0FU
typedef struct
{
#if DRV_BYTE_ORDER == DRV_LITTLE_ENDIAN
  uint8_t int2_fsm1                : 1;
  uint8_t int2_fsm2                : 1;
  uint8_t int2_fsm3                : 1;
  uint8_t int2_fsm4                : 1;
  uint8_t int2_fsm5                : 1;
  uint8_t int2_fsm6                : 1;
  uint8_t int2_fsm7                : 1;
  uint8_t int2_fsm8                : 1;
#elif DRV_BYTE_ORDER == DRV_BIG_ENDIAN
  uint8_t int2_fsm8                : 1;
  uint8_t int2_fsm7                : 1;
  uint8_t int2_fsm6                : 1;
  uint8_t int2_fsm5                : 1;
  uint8_t int2_fsm4                : 1;
  uint8_t int2_fsm3                : 1;
  uint8_t int2_fsm2                : 1;
  uint8_t int2_fsm1                : 1;
#endif /* DRV_BYTE_ORDER */
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
  uint8_t p_y                      : 1;
  uint8_t n_y                      : 1;
  uint8_t p_z                      : 1;
  uint8_t n_z                      : 1;
  uint8_t p_v                      : 1;
  uint8_t n_v                      : 1;
#endif /* DRV_BYTE_ORDER */
} lsm6dsr_fsm_outs15_t;

#define LSM6DSR_FSM_OUTS16                   0x5BU
typedef struct
{
#if DRV_BYTE_ORDER == DRV_LITTLE_ENDIAN
  uint8_t n_v                      : 1;
  uint8_t p_v                      : 1;
  uint8_t n_z                      : 1;
  uint8_t p_z                      : 1;
  uint8_t n_y                      : 1;
  uint8_t p_y                      : 1;
  uint8_t n_x                      : 1;
  uint8_t p_x                      : 1;
#elif DRV_BYTE_ORDER == DRV_BIG_ENDIAN
  uint8_t p_x                      : 1;
  uint8_t n_x                      : 1;
  uint8_t p_y                      : 1;
  uint8_t n_y                      : 1;
  uint8_t p_z                      : 1;
  uint8_t n_z                      : 1;
  uint8_t p_v                      : 1;
  uint8_t n_v                      : 1;
#endif /* DRV_BYTE_ORDER */
} lsm6dsr_fsm_outs16_t;

#define LSM6DSR_EMB_FUNC_ODR_CFG_B           0x5FU
typedef struct
{
#if DRV_BYTE_ORDER == DRV_LITTLE_ENDIAN
  uint8_t not_used_01              : 3;
  uint8_t fsm_odr                  : 2;
  uint8_t not_used_02              : 3;
#elif DRV_BYTE_ORDER == DRV_BIG_ENDIAN
  uint8_t not_used_02              : 3;
  uint8_t fsm_odr                  : 2;
  uint8_t not_used_01              : 3;
#endif /* DRV_BYTE_ORDER */
} lsm6dsr_emb_func_odr_cfg_b_t;

#define LSM6DSR_STEP_COUNTER_L               0x62U
#define LSM6DSR_STEP_COUNTER_H               0x63U
#define LSM6DSR_EMB_FUNC_SRC                 0x64U
typedef struct
{
#if DRV_BYTE_ORDER == DRV_LITTLE_ENDIAN
  uint8_t not_used_01              : 2;
  uint8_t stepcounter_bit_set      : 1;
  uint8_t step_overflow            : 1;
  uint8_t step_count_delta_ia      : 1;
  uint8_t step_detected            : 1;
  uint8_t not_used_02              : 1;
  uint8_t pedo_rst_step            : 1;
#elif DRV_BYTE_ORDER == DRV_BIG_ENDIAN
  uint8_t pedo_rst_step            : 1;
  uint8_t not_used_02              : 1;
  uint8_t step_detected            : 1;
  uint8_t step_count_delta_ia      : 1;
  uint8_t step_overflow            : 1;
  uint8_t stepcounter_bit_set      : 1;
  uint8_t not_used_01              : 2;
#endif /* DRV_BYTE_ORDER */
} lsm6dsr_emb_func_src_t;

#define LSM6DSR_EMB_FUNC_INIT_A              0x66U
typedef struct
{
#if DRV_BYTE_ORDER == DRV_LITTLE_ENDIAN
  uint8_t not_used_01               : 3;
  uint8_t step_det_init             : 1;
  uint8_t tilt_init                 : 1;
  uint8_t sig_mot_init              : 1;
  uint8_t not_used_02               : 2;
#elif DRV_BYTE_ORDER == DRV_BIG_ENDIAN
  uint8_t not_used_02               : 2;
  uint8_t sig_mot_init              : 1;
  uint8_t tilt_init                 : 1;
  uint8_t step_det_init             : 1;
  uint8_t not_used_01               : 3;
#endif /* DRV_BYTE_ORDER */
} lsm6dsr_emb_func_init_a_t;

#define LSM6DSR_EMB_FUNC_INIT_B              0x67U
typedef struct
{
#if DRV_BYTE_ORDER == DRV_LITTLE_ENDIAN
  uint8_t fsm_init                 : 1;
  uint8_t not_used_01              : 2;
  uint8_t fifo_compr_init          : 1;
  uint8_t not_used_02              : 4;
#elif DRV_BYTE_ORDER == DRV_BIG_ENDIAN
  uint8_t not_used_02              : 4;
  uint8_t fifo_compr_init          : 1;
  uint8_t not_used_01              : 2;
  uint8_t fsm_init                 : 1;
#endif /* DRV_BYTE_ORDER */
} lsm6dsr_emb_func_init_b_t;

/** @defgroup bitfields page 0 and 1
  * @{
  *
  */
#define LSM6DSR_MAG_SENSITIVITY_L            0xBAU
#define LSM6DSR_MAG_SENSITIVITY_H            0xBBU
#define LSM6DSR_MAG_OFFX_L                   0xC0U
#define LSM6DSR_MAG_OFFX_H                   0xC1U
#define LSM6DSR_MAG_OFFY_L                   0xC2U
#define LSM6DSR_MAG_OFFY_H                   0xC3U
#define LSM6DSR_MAG_OFFZ_L                   0xC4U
#define LSM6DSR_MAG_OFFZ_H                   0xC5U
#define LSM6DSR_MAG_SI_XX_L                  0xC6U
#define LSM6DSR_MAG_SI_XX_H                  0xC7U
#define LSM6DSR_MAG_SI_XY_L                  0xC8U
#define LSM6DSR_MAG_SI_XY_H                  0xC9U
#define LSM6DSR_MAG_SI_XZ_L                  0xCAU
#define LSM6DSR_MAG_SI_XZ_H                  0xCBU
#define LSM6DSR_MAG_SI_YY_L                  0xCCU
#define LSM6DSR_MAG_SI_YY_H                  0xCDU
#define LSM6DSR_MAG_SI_YZ_L                  0xCEU
#define LSM6DSR_MAG_SI_YZ_H                  0xCFU
#define LSM6DSR_MAG_SI_ZZ_L                  0xD0U
#define LSM6DSR_MAG_SI_ZZ_H                  0xD1U
#define LSM6DSR_MAG_CFG_A                    0xD4U
typedef struct
{
#if DRV_BYTE_ORDER == DRV_LITTLE_ENDIAN
  uint8_t mag_z_axis               : 3;
  uint8_t not_used_01              : 1;
  uint8_t mag_y_axis               : 3;
  uint8_t not_used_02              : 1;
#elif DRV_BYTE_ORDER == DRV_BIG_ENDIAN
  uint8_t not_used_02              : 1;
  uint8_t mag_y_axis               : 3;
  uint8_t not_used_01              : 1;
  uint8_t mag_z_axis               : 3;
#endif /* DRV_BYTE_ORDER */
} lsm6dsr_mag_cfg_a_t;

#define LSM6DSR_MAG_CFG_B                    0xD5U
typedef struct
{
#if DRV_BYTE_ORDER == DRV_LITTLE_ENDIAN
  uint8_t mag_x_axis               : 3;
  uint8_t not_used_01              : 5;
#elif DRV_BYTE_ORDER == DRV_BIG_ENDIAN
  uint8_t not_used_01              : 5;
  uint8_t mag_x_axis               : 3;
#endif /* DRV_BYTE_ORDER */
} lsm6dsr_mag_cfg_b_t;

#define LSM6DSR_FSM_LC_TIMEOUT_L             0x17AU
#define LSM6DSR_FSM_LC_TIMEOUT_H             0x17BU
#define LSM6DSR_FSM_PROGRAMS                 0x17CU
#define LSM6DSR_FSM_START_ADD_L              0x17EU
#define LSM6DSR_FSM_START_ADD_H              0x17FU
#define LSM6DSR_PEDO_CMD_REG                 0x183U
typedef struct
{
#if DRV_BYTE_ORDER == DRV_LITTLE_ENDIAN
  uint8_t ad_det_en                : 1;
  uint8_t not_used_01              : 1;
  uint8_t fp_rejection_en          : 1;
  uint8_t carry_count_en           : 1;
  uint8_t not_used_02              : 4;
#elif DRV_BYTE_ORDER == DRV_BIG_ENDIAN
  uint8_t not_used_02              : 4;
  uint8_t carry_count_en           : 1;
  uint8_t fp_rejection_en          : 1;
  uint8_t not_used_01              : 1;
  uint8_t ad_det_en                : 1;
#endif /* DRV_BYTE_ORDER */
} lsm6dsr_pedo_cmd_reg_t;

#define LSM6DSR_PEDO_DEB_STEPS_CONF          0x184U
#define LSM6DSR_PEDO_SC_DELTAT_L             0x1D0U
#define LSM6DSR_PEDO_SC_DELTAT_H             0x1D1U

/**
  * @}
  *
  */

/** @defgroup bitfields page sensor_hub
  * @{
  *
  */

#define LSM6DSR_SENSOR_HUB_1                 0x02U
typedef struct
{
#if DRV_BYTE_ORDER == DRV_LITTLE_ENDIAN
  uint8_t bit0                    : 1;
  uint8_t bit1                    : 1;
  uint8_t bit2                    : 1;
  uint8_t bit3                    : 1;
  uint8_t bit4                    : 1;
  uint8_t bit5                    : 1;
  uint8_t bit6                    : 1;
  uint8_t bit7                    : 1;
#elif DRV_BYTE_ORDER == DRV_BIG_ENDIAN
  uint8_t bit7                    : 1;
  uint8_t bit6                    : 1;
  uint8_t bit5                    : 1;
  uint8_t bit4                    : 1;
  uint8_t bit3                    : 1;
  uint8_t bit2                    : 1;
  uint8_t bit1                    : 1;
  uint8_t bit0                    : 1;
#endif /* DRV_BYTE_ORDER */
} lsm6dsr_sensor_hub_1_t;

#define LSM6DSR_SENSOR_HUB_2                 0x03U
typedef struct
{
#if DRV_BYTE_ORDER == DRV_LITTLE_ENDIAN
  uint8_t bit0                    : 1;
  uint8_t bit1                    : 1;
  uint8_t bit2                    : 1;
  uint8_t bit3                    : 1;
  uint8_t bit4                    : 1;
  uint8_t bit5                    : 1;
  uint8_t bit6                    : 1;
  uint8_t bit7                    : 1;
#elif DRV_BYTE_ORDER == DRV_BIG_ENDIAN
  uint8_t bit7                    : 1;
  uint8_t bit6                    : 1;
  uint8_t bit5                    : 1;
  uint8_t bit4                    : 1;
  uint8_t bit3                    : 1;
  uint8_t bit2                    : 1;
  uint8_t bit1                    : 1;
  uint8_t bit0                    : 1;
#endif /* DRV_BYTE_ORDER */
} lsm6dsr_sensor_hub_2_t;

#define LSM6DSR_SENSOR_HUB_3                 0x04U
typedef struct
{
#if DRV_BYTE_ORDER == DRV_LITTLE_ENDIAN
  uint8_t bit0                    : 1;
  uint8_t bit1                    : 1;
  uint8_t bit2                    : 1;
  uint8_t bit3                    : 1;
  uint8_t bit4                    : 1;
  uint8_t bit5                    : 1;
  uint8_t bit6                    : 1;
  uint8_t bit7                    : 1;
#elif DRV_BYTE_ORDER == DRV_BIG_ENDIAN
  uint8_t bit7                    : 1;
  uint8_t bit6                    : 1;
  uint8_t bit5                    : 1;
  uint8_t bit4                    : 1;
  uint8_t bit3                    : 1;
  uint8_t bit2                    : 1;
  uint8_t bit1                    : 1;
  uint8_t bit0                    : 1;
#endif /* DRV_BYTE_ORDER */
} lsm6dsr_sensor_hub_3_t;

#define LSM6DSR_SENSOR_HUB_4                 0x05U
typedef struct
{
#if DRV_BYTE_ORDER == DRV_LITTLE_ENDIAN
  uint8_t bit0                    : 1;
  uint8_t bit1                    : 1;
  uint8_t bit2                    : 1;
  uint8_t bit3                    : 1;
  uint8_t bit4                    : 1;
  uint8_t bit5                    : 1;
  uint8_t bit6                    : 1;
  uint8_t bit7                    : 1;
#elif DRV_BYTE_ORDER == DRV_BIG_ENDIAN
  uint8_t bit7                    : 1;
  uint8_t bit6                    : 1;
  uint8_t bit5                    : 1;
  uint8_t bit4                    : 1;
  uint8_t bit3                    : 1;
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
  uint8_t bit5                    : 1;
  uint8_t bit4                    : 1;
  uint8_t bit3                    : 1;
  uint8_t bit2                    : 1;
  uint8_t bit1                    : 1;
  uint8_t bit0                    : 1;
#endif /* DRV_BYTE_ORDER */
} lsm6dsr_sensor_hub_17_t;

#define LSM6DSR_SENSOR_HUB_18                0x13U
typedef struct
{
#if DRV_BYTE_ORDER == DRV_LITTLE_ENDIAN
  uint8_t bit0                    : 1;
  uint8_t bit1                    : 1;
  uint8_t bit2                    : 1;
  uint8_t bit3                    : 1;
  uint8_t bit4                    : 1;
  uint8_t bit5                    : 1;
  uint8_t bit6                    : 1;
  uint8_t bit7                    : 1;
#elif DRV_BYTE_ORDER == DRV_BIG_ENDIAN
  uint8_t bit7                    : 1;
  uint8_t bit6                    : 1;
  uint8_t bit5                    : 1;
  uint8_t bit4                    : 1;
  uint8_t bit3                    : 1;
  uint8_t bit2                    : 1;
  uint8_t bit1                    : 1;
  uint8_t bit0                    : 1;
#endif /* DRV_BYTE_ORDER */
} lsm6dsr_sensor_hub_18_t;

#define LSM6DSR_MASTER_CONFIG                0x14U
typedef struct
{
#if DRV_BYTE_ORDER == DRV_LITTLE_ENDIAN
  uint8_t aux_sens_on              : 2;
  uint8_t master_on                : 1;
  uint8_t shub_pu_en               : 1;
  uint8_t pass_through_mode        : 1;
  uint8_t start_config             : 1;
  uint8_t write_once               : 1;
  uint8_t rst_master_regs          : 1;
#elif DRV_BYTE_ORDER == DRV_BIG_ENDIAN
  uint8_t rst_master_regs          : 1;
  uint8_t write_once               : 1;
  uint8_t start_config             : 1;
  uint8_t pass_through_mode        : 1;
  uint8_t shub_pu_en               : 1;
  uint8_t master_on                : 1;
  uint8_t aux_sens_on              : 2;
#endif /* DRV_BYTE_ORDER */
} lsm6dsr_master_config_t;

#define LSM6DSR_SLV0_ADD                     0x15U
typedef struct
{
#if DRV_BYTE_ORDER == DRV_LITTLE_ENDIAN
  uint8_t rw_0                     : 1;
  uint8_t slave0                   : 7;
#elif DRV_BYTE_ORDER == DRV_BIG_ENDIAN
  uint8_t slave0                   : 7;
  uint8_t rw_0                     : 1;
#endif /* DRV_BYTE_ORDER */
} lsm6dsr_slv0_add_t;

#define LSM6DSR_SLV0_SUBADD                  0x16U
typedef struct
{
  uint8_t slave0_reg               : 8;
} lsm6dsr_slv0_subadd_t;

#define LSM6DSR_SLV0_CONFIG                  0x17U
typedef struct
{
#if DRV_BYTE_ORDER == DRV_LITTLE_ENDIAN
  uint8_t slave0_numop             : 3;
  uint8_t batch_ext_sens_0_en      : 1;
  uint8_t not_used_01              : 2;
  uint8_t shub_odr                 : 2;
#elif DRV_BYTE_ORDER == DRV_BIG_ENDIAN
  uint8_t shub_odr                 : 2;
  uint8_t not_used_01              : 2;
  uint8_t batch_ext_sens_0_en      : 1;
  uint8_t slave0_numop             : 3;
#endif /* DRV_BYTE_ORDER */
} lsm6dsr_slv0_config_t;

#define LSM6DSR_SLV1_ADD                     0x18U
typedef struct
{
#if DRV_BYTE_ORDER == DRV_LITTLE_ENDIAN
  uint8_t r_1                      : 1;
  uint8_t slave1_add               : 7;
#elif DRV_BYTE_ORDER == DRV_BIG_ENDIAN
  uint8_t slave1_add               : 7;
  uint8_t r_1                      : 1;
#endif /* DRV_BYTE_ORDER */
} lsm6dsr_slv1_add_t;

#define LSM6DSR_SLV1_SUBADD                  0x19U
typedef struct
{
  uint8_t slave1_reg               : 8;
} lsm6dsr_slv1_subadd_t;

#define LSM6DSR_SLV1_CONFIG                  0x1AU
typedef struct
{
#if DRV_BYTE_ORDER == DRV_LITTLE_ENDIAN
  uint8_t slave1_numop             : 3;
  uint8_t batch_ext_sens_1_en      : 1;
  uint8_t not_used_01              : 4;
#elif DRV_BYTE_ORDER == DRV_BIG_ENDIAN
  uint8_t not_used_01              : 4;
  uint8_t batch_ext_sens_1_en      : 1;
  uint8_t slave1_numop             : 3;
#endif /* DRV_BYTE_ORDER */
} lsm6dsr_slv1_config_t;

#define LSM6DSR_SLV2_ADD                     0x1BU
typedef struct
{
#if DRV_BYTE_ORDER == DRV_LITTLE_ENDIAN
  uint8_t r_2                      : 1;
  uint8_t slave2_add               : 7;
#elif DRV_BYTE_ORDER == DRV_BIG_ENDIAN
  uint8_t slave2_add               : 7;
  uint8_t r_2                      : 1;
#endif /* DRV_BYTE_ORDER */
} lsm6dsr_slv2_add_t;

#define LSM6DSR_SLV2_SUBADD                  0x1CU
typedef struct
{
  uint8_t slave2_reg               : 8;
} lsm6dsr_slv2_subadd_t;

#define LSM6DSR_SLV2_CONFIG                  0x1DU
typedef struct
{
#if DRV_BYTE_ORDER == DRV_LITTLE_ENDIAN
  uint8_t slave2_numop             : 3;
  uint8_t batch_ext_sens_2_en      : 1;
  uint8_t not_used_01              : 4;
#elif DRV_BYTE_ORDER == DRV_BIG_ENDIAN
  uint8_t not_used_01              : 4;
  uint8_t batch_ext_sens_2_en      : 1;
  uint8_t slave2_numop             : 3;
#endif /* DRV_BYTE_ORDER */
} lsm6dsr_slv2_config_t;

#define LSM6DSR_SLV3_ADD                     0x1EU
typedef struct
{
#if DRV_BYTE_ORDER == DRV_LITTLE_ENDIAN
  uint8_t r_3                      : 1;
  uint8_t slave3_add               : 7;
#elif DRV_BYTE_ORDER == DRV_BIG_ENDIAN
  uint8_t slave3_add               : 7;
  uint8_t r_3                      : 1;
#endif /* DRV_BYTE_ORDER */
} lsm6dsr_slv3_add_t;

#define LSM6DSR_SLV3_SUBADD                  0x1FU
typedef struct
{
  uint8_t slave3_reg               : 8;
} lsm6dsr_slv3_subadd_t;

#define LSM6DSR_SLV3_CONFIG                  0x20U
typedef struct
{
#if DRV_BYTE_ORDER == DRV_LITTLE_ENDIAN
  uint8_t slave3_numop             : 3;
  uint8_t batch_ext_sens_3_en      : 1;
  uint8_t not_used_01              : 4;
#elif DRV_BYTE_ORDER == DRV_BIG_ENDIAN
  uint8_t not_used_01              : 4;
  uint8_t batch_ext_sens_3_en      : 1;
  uint8_t slave3_numop             : 3;
#endif /* DRV_BYTE_ORDER */
} lsm6dsr_slv3_config_t;

#define LSM6DSR_DATAWRITE_SLV0  0x21U
typedef struct
{
  uint8_t slave0_dataw             : 8;
} lsm6dsr_datawrite_slv0_t;

#define LSM6DSR_STATUS_MASTER                0x22U
typedef struct
{
#if DRV_BYTE_ORDER == DRV_LITTLE_ENDIAN
  uint8_t sens_hub_endop           : 1;
  uint8_t not_used_01              : 2;
  uint8_t slave0_nack              : 1;
  uint8_t slave1_nack              : 1;
  uint8_t slave2_nack              : 1;
  uint8_t slave3_nack              : 1;
  uint8_t wr_once_done             : 1;
#elif DRV_BYTE_ORDER == DRV_BIG_ENDIAN
  uint8_t wr_once_done             : 1;
  uint8_t slave3_nack              : 1;
  uint8_t slave2_nack              : 1;
  uint8_t slave1_nack              : 1;
  uint8_t slave0_nack              : 1;
  uint8_t not_used_01              : 2;
  uint8_t sens_hub_endop           : 1;
#endif /* DRV_BYTE_ORDER */
} lsm6dsr_status_master_t;

/**
  * @}
  *
  */

#ifndef __weak
#define __weak __attribute__((weak))
#endif /* __weak */

/*
 * These are the basic platform dependent I/O routines to read
 * and write device registers connected on a standard bus.
 * The driver keeps offering a default implementation based on function
 * pointers to read/write routines for backward compatibility.
 * The __weak directive allows the final application to overwrite
 * them with a custom implementation.
 */
int32_t lsm6dsr_read_reg(const stmdev_ctx_t *ctx, uint8_t reg,
                         uint8_t *data,
                         uint16_t len);
int32_t lsm6dsr_write_reg(const stmdev_ctx_t *ctx, uint8_t reg,
                          uint8_t *data,
                          uint16_t len);

float_t lsm6dsr_from_fs2g_to_mg(int16_t lsb);
float_t lsm6dsr_from_fs4g_to_mg(int16_t lsb);
float_t lsm6dsr_from_fs8g_to_mg(int16_t lsb);
float_t lsm6dsr_from_fs16g_to_mg(int16_t lsb);

float_t lsm6dsr_from_fs125dps_to_mdps(int16_t lsb);
float_t lsm6dsr_from_fs250dps_to_mdps(int16_t lsb);
float_t lsm6dsr_from_fs500dps_to_mdps(int16_t lsb);
float_t lsm6dsr_from_fs1000dps_to_mdps(int16_t lsb);
float_t lsm6dsr_from_fs2000dps_to_mdps(int16_t lsb);
float_t lsm6dsr_from_fs4000dps_to_mdps(int16_t lsb);

float_t lsm6dsr_from_lsb_to_celsius(int16_t lsb);

uint64_t lsm6dsr_from_lsb_to_nsec(uint32_t lsb);

typedef enum
{
  LSM6DSR_2g   = 0,
  LSM6DSR_16g  = 1, /* if XL_FS_MODE = '1' -> LSM6DSR_2g */
  LSM6DSR_4g   = 2,
  LSM6DSR_8g   = 3,
} lsm6dsr_fs_xl_t;
int32_t lsm6dsr_xl_full_scale_set(const stmdev_ctx_t *ctx,
                                  lsm6dsr_fs_xl_t val);
int32_t lsm6dsr_xl_full_scale_get(const stmdev_ctx_t *ctx,
                                  lsm6dsr_fs_xl_t *val);

typedef enum
{
  LSM6DSR_XL_ODR_OFF    = 0,
  LSM6DSR_XL_ODR_12Hz5  = 1,
  LSM6DSR_XL_ODR_26Hz   = 2,
  LSM6DSR_XL_ODR_52Hz   = 3,
  LSM6DSR_XL_ODR_104Hz  = 4,
  LSM6DSR_XL_ODR_208Hz  = 5,
  LSM6DSR_XL_ODR_416Hz  = 6,
  LSM6DSR_XL_ODR_833Hz  = 7,
  LSM6DSR_XL_ODR_1666Hz = 8,
  LSM6DSR_XL_ODR_3332Hz = 9,
  LSM6DSR_XL_ODR_6667Hz = 10,
  LSM6DSR_XL_ODR_1Hz6   = 11, /* (low power only) */
} lsm6dsr_odr_xl_t;
int32_t lsm6dsr_xl_data_rate_set(const stmdev_ctx_t *ctx,
                                 lsm6dsr_odr_xl_t val);
int32_t lsm6dsr_xl_data_rate_get(const stmdev_ctx_t *ctx,
                                 lsm6dsr_odr_xl_t *val);

typedef enum
{
  LSM6DSR_125dps = 2,
  LSM6DSR_250dps = 0,
  LSM6DSR_500dps = 4,
  LSM6DSR_1000dps = 8,
  LSM6DSR_2000dps = 12,
  LSM6DSR_4000dps = 1,
} lsm6dsr_fs_g_t;
int32_t lsm6dsr_gy_full_scale_set(const stmdev_ctx_t *ctx,
                                  lsm6dsr_fs_g_t val);
int32_t lsm6dsr_gy_full_scale_get(const stmdev_ctx_t *ctx,
                                  lsm6dsr_fs_g_t *val);

typedef enum
{
  LSM6DSR_GY_ODR_OFF    = 0,
  LSM6DSR_GY_ODR_12Hz5  = 1,
  LSM6DSR_GY_ODR_26Hz   = 2,
  LSM6DSR_GY_ODR_52Hz   = 3,
  LSM6DSR_GY_ODR_104Hz  = 4,
  LSM6DSR_GY_ODR_208Hz  = 5,
  LSM6DSR_GY_ODR_416Hz  = 6,
  LSM6DSR_GY_ODR_833Hz  = 7,
  LSM6DSR_GY_ODR_1666Hz = 8,
  LSM6DSR_GY_ODR_3332Hz = 9,
  LSM6DSR_GY_ODR_6667Hz = 10,
} lsm6dsr_odr_g_t;
int32_t lsm6dsr_gy_data_rate_set(const stmdev_ctx_t *ctx,
                                 lsm6dsr_odr_g_t val);
int32_t lsm6dsr_gy_data_rate_get(const stmdev_ctx_t *ctx,
                                 lsm6dsr_odr_g_t *val);

int32_t lsm6dsr_block_data_update_set(const stmdev_ctx_t *ctx,
                                      uint8_t val);
int32_t lsm6dsr_block_data_update_get(const stmdev_ctx_t *ctx,
                                      uint8_t *val);

typedef enum
{
  LSM6DSR_LSb_1mg  = 0,
  LSM6DSR_LSb_16mg = 1,
} lsm6dsr_usr_off_w_t;
int32_t lsm6dsr_xl_offset_weight_set(const stmdev_ctx_t *ctx,
                                     lsm6dsr_usr_off_w_t val);
int32_t lsm6dsr_xl_offset_weight_get(const stmdev_ctx_t *ctx,
                                     lsm6dsr_usr_off_w_t *val);

typedef enum
{
  LSM6DSR_HIGH_PERFORMANCE_MD  = 0,
  LSM6DSR_LOW_NORMAL_POWER_MD  = 1,
} lsm6dsr_xl_hm_mode_t;
int32_t lsm6dsr_xl_power_mode_set(const stmdev_ctx_t *ctx,
                                  lsm6dsr_xl_hm_mode_t val);
int32_t lsm6dsr_xl_power_mode_get(const stmdev_ctx_t *ctx,
                                  lsm6dsr_xl_hm_mode_t *val);

typedef enum
{
  LSM6DSR_GY_HIGH_PERFORMANCE  = 0,
  LSM6DSR_GY_NORMAL            = 1,
} lsm6dsr_g_hm_mode_t;
int32_t lsm6dsr_gy_power_mode_set(const stmdev_ctx_t *ctx,
                                  lsm6dsr_g_hm_mode_t val);
int32_t lsm6dsr_gy_power_mode_get(const stmdev_ctx_t *ctx,
                                  lsm6dsr_g_hm_mode_t *val);

typedef struct
{
  lsm6dsr_all_int_src_t           all_int_src;
  lsm6dsr_wake_up_src_t           wake_up_src;
  lsm6dsr_tap_src_t               tap_src;
  lsm6dsr_d6d_src_t               d6d_src;
  lsm6dsr_status_reg_t            status_reg;
  lsm6dsr_emb_func_status_t       emb_func_status;
  lsm6dsr_fsm_status_a_t          fsm_status_a;
  lsm6dsr_fsm_status_b_t          fsm_status_b;
} lsm6dsr_all_sources_t;
int32_t lsm6dsr_all_sources_get(const stmdev_ctx_t *ctx,
                                lsm6dsr_all_sources_t *val);

int32_t lsm6dsr_status_reg_get(const stmdev_ctx_t *ctx,
                               lsm6dsr_status_reg_t *val);

int32_t lsm6dsr_xl_flag_data_ready_get(const stmdev_ctx_t *ctx,
                                       uint8_t *val);

int32_t lsm6dsr_gy_flag_data_ready_get(const stmdev_ctx_t *ctx,
                                       uint8_t *val);

int32_t lsm6dsr_temp_flag_data_ready_get(const stmdev_ctx_t *ctx,
                                         uint8_t *val);

int32_t lsm6dsr_xl_usr_offset_x_set(const stmdev_ctx_t *ctx,
                                    uint8_t *val);
int32_t lsm6dsr_xl_usr_offset_x_get(const stmdev_ctx_t *ctx,
                                    uint8_t *val);

int32_t lsm6dsr_xl_usr_offset_y_set(const stmdev_ctx_t *ctx,
                                    uint8_t *val);
int32_t lsm6dsr_xl_usr_offset_y_get(const stmdev_ctx_t *ctx,
                                    uint8_t *val);

int32_t lsm6dsr_xl_usr_offset_z_set(const stmdev_ctx_t *ctx,
                                    uint8_t *val);
int32_t lsm6dsr_xl_usr_offset_z_get(const stmdev_ctx_t *ctx,
                                    uint8_t *val);

int32_t lsm6dsr_xl_usr_offset_set(const stmdev_ctx_t *ctx, uint8_t val);
int32_t lsm6dsr_xl_usr_offset_get(const stmdev_ctx_t *ctx, uint8_t *val);

int32_t lsm6dsr_timestamp_rst(const stmdev_ctx_t *ctx);

int32_t lsm6dsr_timestamp_set(const stmdev_ctx_t *ctx, uint8_t val);
int32_t lsm6dsr_timestamp_get(const stmdev_ctx_t *ctx, uint8_t *val);

int32_t lsm6dsr_timestamp_raw_get(const stmdev_ctx_t *ctx, uint32_t *val);

typedef enum
{
  LSM6DSR_NO_ROUND      = 0,
  LSM6DSR_ROUND_XL      = 1,
  LSM6DSR_ROUND_GY      = 2,
  LSM6DSR_ROUND_GY_XL   = 3,
} lsm6dsr_rounding_t;
int32_t lsm6dsr_rounding_mode_set(const stmdev_ctx_t *ctx,
                                  lsm6dsr_rounding_t val);
int32_t lsm6dsr_rounding_mode_get(const stmdev_ctx_t *ctx,
                                  lsm6dsr_rounding_t *val);

int32_t lsm6dsr_temperature_raw_get(const stmdev_ctx_t *ctx, int16_t *val);

int32_t lsm6dsr_angular_rate_raw_get(const stmdev_ctx_t *ctx, int16_t *val);

int32_t lsm6dsr_acceleration_raw_get(const stmdev_ctx_t *ctx, int16_t *val);

int32_t lsm6dsr_fifo_out_raw_get(const stmdev_ctx_t *ctx, uint8_t *val);

int32_t lsm6dsr_odr_cal_reg_get(const stmdev_ctx_t *ctx, int8_t *val);

int32_t lsm6dsr_number_of_steps_get(const stmdev_ctx_t *ctx, uint16_t *val);

int32_t lsm6dsr_steps_reset(const stmdev_ctx_t *ctx);

typedef enum
{
  LSM6DSR_USER_BANK           = 0,
  LSM6DSR_SENSOR_HUB_BANK     = 1,
  LSM6DSR_EMBEDDED_FUNC_BANK  = 2,
} lsm6dsr_reg_access_t;
int32_t lsm6dsr_mem_bank_set(const stmdev_ctx_t *ctx,
                             lsm6dsr_reg_access_t val);
int32_t lsm6dsr_mem_bank_get(const stmdev_ctx_t *ctx,
                             lsm6dsr_reg_access_t *val);

int32_t lsm6dsr_ln_pg_write_byte(const stmdev_ctx_t *ctx, uint16_t address,
                                 uint8_t *val);
int32_t lsm6dsr_ln_pg_write(const stmdev_ctx_t *ctx, uint16_t address,
                            uint8_t *buf, uint8_t len);
int32_t lsm6dsr_ln_pg_read_byte(const stmdev_ctx_t *ctx, uint16_t add,
                                uint8_t *val);
int32_t lsm6dsr_ln_pg_read(const stmdev_ctx_t *ctx, uint16_t address,
                           uint8_t *val);

typedef enum
{
  LSM6DSR_DRDY_LATCHED = 0,
  LSM6DSR_DRDY_PULSED  = 1,
} lsm6dsr_dataready_pulsed_t;
int32_t lsm6dsr_data_ready_mode_set(const stmdev_ctx_t *ctx,
                                    lsm6dsr_dataready_pulsed_t val);
int32_t lsm6dsr_data_ready_mode_get(const stmdev_ctx_t *ctx,
                                    lsm6dsr_dataready_pulsed_t *val);

int32_t lsm6dsr_device_id_get(const stmdev_ctx_t *ctx, uint8_t *val);

int32_t lsm6dsr_reset_set(const stmdev_ctx_t *ctx, uint8_t val);
int32_t lsm6dsr_reset_get(const stmdev_ctx_t *ctx, uint8_t *val);

int32_t lsm6dsr_auto_increment_set(const stmdev_ctx_t *ctx, uint8_t val);
int32_t lsm6dsr_auto_increment_get(const stmdev_ctx_t *ctx, uint8_t *val);

int32_t lsm6dsr_boot_set(const stmdev_ctx_t *ctx, uint8_t val);
int32_t lsm6dsr_boot_get(const stmdev_ctx_t *ctx, uint8_t *val);

typedef enum
{
  LSM6DSR_XL_ST_DISABLE  = 0,
  LSM6DSR_XL_ST_POSITIVE = 1,
  LSM6DSR_XL_ST_NEGATIVE = 2,
} lsm6dsr_st_xl_t;
int32_t lsm6dsr_xl_self_test_set(const stmdev_ctx_t *ctx,
                                 lsm6dsr_st_xl_t val);
int32_t lsm6dsr_xl_self_test_get(const stmdev_ctx_t *ctx,
                                 lsm6dsr_st_xl_t *val);

typedef enum
{
  LSM6DSR_GY_ST_DISABLE  = 0,
  LSM6DSR_GY_ST_POSITIVE = 1,
  LSM6DSR_GY_ST_NEGATIVE = 3,
} lsm6dsr_st_g_t;
int32_t lsm6dsr_gy_self_test_set(const stmdev_ctx_t *ctx,
                                 lsm6dsr_st_g_t val);
int32_t lsm6dsr_gy_self_test_get(const stmdev_ctx_t *ctx,
                                 lsm6dsr_st_g_t *val);

int32_t lsm6dsr_xl_filter_lp2_set(const stmdev_ctx_t *ctx, uint8_t val);
int32_t lsm6dsr_xl_filter_lp2_get(const stmdev_ctx_t *ctx, uint8_t *val);

int32_t lsm6dsr_gy_filter_lp1_set(const stmdev_ctx_t *ctx, uint8_t val);
int32_t lsm6dsr_gy_filter_lp1_get(const stmdev_ctx_t *ctx, uint8_t *val);

int32_t lsm6dsr_drdy_mask_set(const stmdev_ctx_t *ctx, uint8_t val);
int32_t lsm6dsr_drdy_mask_get(const stmdev_ctx_t *ctx, uint8_t *val);

typedef enum
{
  LSM6DSR_ULTRA_LIGHT  = 0,
  LSM6DSR_VERY_LIGHT   = 1,
  LSM6DSR_LIGHT        = 2,
  LSM6DSR_MEDIUM       = 3,
  LSM6DSR_STRONG       = 4,
  LSM6DSR_VERY_STRONG  = 5,
  LSM6DSR_AGGRESSIVE   = 6,
  LSM6DSR_XTREME       = 7,
} lsm6dsr_ftype_t;
int32_t lsm6dsr_gy_lp1_bandwidth_set(const stmdev_ctx_t *ctx,
                                     lsm6dsr_ftype_t val);
int32_t lsm6dsr_gy_lp1_bandwidth_get(const stmdev_ctx_t *ctx,
                                     lsm6dsr_ftype_t *val);

int32_t lsm6dsr_xl_lp2_on_6d_set(const stmdev_ctx_t *ctx, uint8_t val);
int32_t lsm6dsr_xl_lp2_on_6d_get(const stmdev_ctx_t *ctx, uint8_t *val);

typedef enum
{
  LSM6DSR_HP_PATH_DISABLE_ON_OUT    = 0x00,
  LSM6DSR_SLOPE_ODR_DIV_4           = 0x10,
  LSM6DSR_HP_ODR_DIV_10             = 0x11,
  LSM6DSR_HP_ODR_DIV_20             = 0x12,
  LSM6DSR_HP_ODR_DIV_45             = 0x13,
  LSM6DSR_HP_ODR_DIV_100            = 0x14,
  LSM6DSR_HP_ODR_DIV_200            = 0x15,
  LSM6DSR_HP_ODR_DIV_400            = 0x16,
  LSM6DSR_HP_ODR_DIV_800            = 0x17,
  LSM6DSR_HP_REF_MD_ODR_DIV_10      = 0x31,
  LSM6DSR_HP_REF_MD_ODR_DIV_20      = 0x32,
  LSM6DSR_HP_REF_MD_ODR_DIV_45      = 0x33,
  LSM6DSR_HP_REF_MD_ODR_DIV_100     = 0x34,
  LSM6DSR_HP_REF_MD_ODR_DIV_200     = 0x35,
  LSM6DSR_HP_REF_MD_ODR_DIV_400     = 0x36,
  LSM6DSR_HP_REF_MD_ODR_DIV_800     = 0x37,
  LSM6DSR_LP_ODR_DIV_10             = 0x01,
  LSM6DSR_LP_ODR_DIV_20             = 0x02,
  LSM6DSR_LP_ODR_DIV_45             = 0x03,
  LSM6DSR_LP_ODR_DIV_100            = 0x04,
  LSM6DSR_LP_ODR_DIV_200            = 0x05,
  LSM6DSR_LP_ODR_DIV_400            = 0x06,
  LSM6DSR_LP_ODR_DIV_800            = 0x07,
} lsm6dsr_hp_slope_xl_en_t;
int32_t lsm6dsr_xl_hp_path_on_out_set(const stmdev_ctx_t *ctx,
                                      lsm6dsr_hp_slope_xl_en_t val);
int32_t lsm6dsr_xl_hp_path_on_out_get(const stmdev_ctx_t *ctx,
                                      lsm6dsr_hp_slope_xl_en_t *val);

int32_t lsm6dsr_xl_fast_settling_set(const stmdev_ctx_t *ctx, uint8_t val);
int32_t lsm6dsr_xl_fast_settling_get(const stmdev_ctx_t *ctx, uint8_t *val);

typedef enum
{
  LSM6DSR_USE_SLOPE = 0,
  LSM6DSR_USE_HPF   = 1,
} lsm6dsr_slope_fds_t;
int32_t lsm6dsr_xl_hp_path_internal_set(const stmdev_ctx_t *ctx,
                                        lsm6dsr_slope_fds_t val);
int32_t lsm6dsr_xl_hp_path_internal_get(const stmdev_ctx_t *ctx,
                                        lsm6dsr_slope_fds_t *val);

typedef enum
{
  LSM6DSR_HP_FILTER_NONE     = 0x00,
  LSM6DSR_HP_FILTER_16mHz    = 0x80,
  LSM6DSR_HP_FILTER_65mHz    = 0x81,
  LSM6DSR_HP_FILTER_260mHz   = 0x82,
  LSM6DSR_HP_FILTER_1Hz04    = 0x83,
} lsm6dsr_hpm_g_t;
int32_t lsm6dsr_gy_hp_path_internal_set(const stmdev_ctx_t *ctx,
                                        lsm6dsr_hpm_g_t val);
int32_t lsm6dsr_gy_hp_path_internal_get(const stmdev_ctx_t *ctx,
                                        lsm6dsr_hpm_g_t *val);

typedef enum
{
  LSM6DSR_AUX_PULL_UP_DISC       = 0,
  LSM6DSR_AUX_PULL_UP_CONNECT    = 1,
} lsm6dsr_ois_pu_dis_t;
int32_t lsm6dsr_aux_sdo_ocs_mode_set(const stmdev_ctx_t *ctx,
                                     lsm6dsr_ois_pu_dis_t val);
int32_t lsm6dsr_aux_sdo_ocs_mode_get(const stmdev_ctx_t *ctx,
                                     lsm6dsr_ois_pu_dis_t *val);

typedef enum
{
  LSM6DSR_AUX_ON                    = 1,
  LSM6DSR_AUX_ON_BY_AUX_INTERFACE   = 0,
} lsm6dsr_ois_on_t;
int32_t lsm6dsr_aux_pw_on_ctrl_set(const stmdev_ctx_t *ctx,
                                   lsm6dsr_ois_on_t val);
int32_t lsm6dsr_aux_pw_on_ctrl_get(const stmdev_ctx_t *ctx,
                                   lsm6dsr_ois_on_t *val);

int32_t lsm6dsr_aux_status_reg_get(const stmdev_ctx_t *ctx,
                                   lsm6dsr_status_spiaux_t *val);

int32_t lsm6dsr_aux_xl_flag_data_ready_get(const stmdev_ctx_t *ctx,
                                           uint8_t *val);

int32_t lsm6dsr_aux_gy_flag_data_ready_get(const stmdev_ctx_t *ctx,
                                           uint8_t *val);

int32_t lsm6dsr_aux_gy_flag_settling_get(const stmdev_ctx_t *ctx,
                                         uint8_t *val);

typedef enum
{
  LSM6DSR_AUX_XL_DISABLE = 0,
  LSM6DSR_AUX_XL_POS     = 1,
  LSM6DSR_AUX_XL_NEG     = 2,
} lsm6dsr_st_xl_ois_t;
int32_t lsm6dsr_aux_xl_self_test_set(const stmdev_ctx_t *ctx,
                                     lsm6dsr_st_xl_ois_t val);
int32_t lsm6dsr_aux_xl_self_test_get(const stmdev_ctx_t *ctx,
                                     lsm6dsr_st_xl_ois_t *val);

typedef enum
{
  LSM6DSR_AUX_DEN_ACTIVE_LOW     = 0,
  LSM6DSR_AUX_DEN_ACTIVE_HIGH    = 1,
} lsm6dsr_den_lh_ois_t;
int32_t lsm6dsr_aux_den_polarity_set(const stmdev_ctx_t *ctx,
                                     lsm6dsr_den_lh_ois_t val);
int32_t lsm6dsr_aux_den_polarity_get(const stmdev_ctx_t *ctx,
                                     lsm6dsr_den_lh_ois_t *val);

typedef enum
{
  LSM6DSR_AUX_DEN_DISABLE         = 0,
  LSM6DSR_AUX_DEN_LEVEL_LATCH     = 3,
  LSM6DSR_AUX_DEN_LEVEL_TRIG      = 2,
} lsm6dsr_lvl2_ois_t;
int32_t lsm6dsr_aux_den_mode_set(const stmdev_ctx_t *ctx,
                                 lsm6dsr_lvl2_ois_t val);
int32_t lsm6dsr_aux_den_mode_get(const stmdev_ctx_t *ctx,
                                 lsm6dsr_lvl2_ois_t *val);

int32_t lsm6dsr_aux_drdy_on_int2_set(const stmdev_ctx_t *ctx, uint8_t val);
int32_t lsm6dsr_aux_drdy_on_int2_get(const stmdev_ctx_t *ctx, uint8_t *val);

typedef enum
{
  LSM6DSR_AUX_DISABLE  = 0,
  LSM6DSR_MODE_3_GY    = 1,
  LSM6DSR_MODE_4_GY_XL = 3,
} lsm6dsr_ois_en_spi2_t;
int32_t lsm6dsr_aux_mode_set(const stmdev_ctx_t *ctx,
                             lsm6dsr_ois_en_spi2_t val);
int32_t lsm6dsr_aux_mode_get(const stmdev_ctx_t *ctx,
                             lsm6dsr_ois_en_spi2_t *val);

typedef enum
{
  LSM6DSR_125dps_AUX  =  0x04,
  LSM6DSR_250dps_AUX  =  0x00,
  LSM6DSR_500dps_AUX  =  0x01,
  LSM6DSR_1000dps_AUX =  0x02,
  LSM6DSR_2000dps_AUX =  0x03,
} lsm6dsr_fs_g_ois_t;
int32_t lsm6dsr_aux_gy_full_scale_set(const stmdev_ctx_t *ctx,
                                      lsm6dsr_fs_g_ois_t val);
int32_t lsm6dsr_aux_gy_full_scale_get(const stmdev_ctx_t *ctx,
                                      lsm6dsr_fs_g_ois_t *val);

typedef enum
{
  LSM6DSR_AUX_SPI_4_WIRE = 0,
  LSM6DSR_AUX_SPI_3_WIRE = 1,
} lsm6dsr_sim_ois_t;
int32_t lsm6dsr_aux_spi_mode_set(const stmdev_ctx_t *ctx,
                                 lsm6dsr_sim_ois_t val);
int32_t lsm6dsr_aux_spi_mode_get(const stmdev_ctx_t *ctx,
                                 lsm6dsr_sim_ois_t *val);

typedef enum
{
  LSM6DSR_351Hz39 = 0,
  LSM6DSR_236Hz63 = 1,
  LSM6DSR_172Hz70 = 2,
  LSM6DSR_937Hz91 = 3,
} lsm6dsr_ftype_ois_t;
int32_t lsm6dsr_aux_gy_lp1_bandwidth_set(const stmdev_ctx_t *ctx,
                                         lsm6dsr_ftype_ois_t val);
int32_t lsm6dsr_aux_gy_lp1_bandwidth_get(const stmdev_ctx_t *ctx,
                                         lsm6dsr_ftype_ois_t *val);

typedef enum
{
  LSM6DSR_AUX_HP_DISABLE = 0x00,
  LSM6DSR_AUX_HP_Hz016   = 0x10,
  LSM6DSR_AUX_HP_Hz065   = 0x11,
  LSM6DSR_AUX_HP_Hz260   = 0x12,
  LSM6DSR_AUX_HP_1Hz040  = 0x13,
} lsm6dsr_hpm_ois_t;
int32_t lsm6dsr_aux_gy_hp_bandwidth_set(const stmdev_ctx_t *ctx,
                                        lsm6dsr_hpm_ois_t val);
int32_t lsm6dsr_aux_gy_hp_bandwidth_get(const stmdev_ctx_t *ctx,
                                        lsm6dsr_hpm_ois_t *val);

typedef enum
{
  LSM6DSR_ENABLE_CLAMP  = 0,
  LSM6DSR_DISABLE_CLAMP = 1,
} lsm6dsr_st_ois_clampdis_t;
int32_t lsm6dsr_aux_gy_clamp_set(const stmdev_ctx_t *ctx,
                                 lsm6dsr_st_ois_clampdis_t val);
int32_t lsm6dsr_aux_gy_clamp_get(const stmdev_ctx_t *ctx,
                                 lsm6dsr_st_ois_clampdis_t *val);

typedef enum
{
  LSM6DSR_AUX_GY_DISABLE = 0,
  LSM6DSR_AUX_GY_POS     = 1,
  LSM6DSR_AUX_GY_NEG     = 3,
} lsm6dsr_st_ois_t;
int32_t lsm6dsr_aux_gy_self_test_set(const stmdev_ctx_t *ctx,
                                     lsm6dsr_st_ois_t val);
int32_t lsm6dsr_aux_gy_self_test_get(const stmdev_ctx_t *ctx,
                                     lsm6dsr_st_ois_t *val);

typedef enum
{
  LSM6DSR_631Hz = 0,
  LSM6DSR_295Hz = 1,
  LSM6DSR_140Hz = 2,
  LSM6DSR_68Hz2 = 3,
  LSM6DSR_33Hz6 = 4,
  LSM6DSR_16Hz7 = 5,
  LSM6DSR_8Hz3  = 6,
  LSM6DSR_4Hz11 = 7,
} lsm6dsr_filter_xl_conf_ois_t;
int32_t lsm6dsr_aux_xl_bandwidth_set(const stmdev_ctx_t *ctx,
                                     lsm6dsr_filter_xl_conf_ois_t val);
int32_t lsm6dsr_aux_xl_bandwidth_get(const stmdev_ctx_t *ctx,
                                     lsm6dsr_filter_xl_conf_ois_t *val);

typedef enum
{
  LSM6DSR_AUX_2g  = 0,
  LSM6DSR_AUX_16g = 1,
  LSM6DSR_AUX_4g  = 2,
  LSM6DSR_AUX_8g  = 3,
} lsm6dsr_fs_xl_ois_t;
int32_t lsm6dsr_aux_xl_full_scale_set(const stmdev_ctx_t *ctx,
                                      lsm6dsr_fs_xl_ois_t val);
int32_t lsm6dsr_aux_xl_full_scale_get(const stmdev_ctx_t *ctx,
                                      lsm6dsr_fs_xl_ois_t *val);

typedef enum
{
  LSM6DSR_PULL_UP_DISC       = 0,
  LSM6DSR_PULL_UP_CONNECT    = 1,
} lsm6dsr_sdo_pu_en_t;
int32_t lsm6dsr_sdo_sa0_mode_set(const stmdev_ctx_t *ctx,
                                 lsm6dsr_sdo_pu_en_t val);
int32_t lsm6dsr_sdo_sa0_mode_get(const stmdev_ctx_t *ctx,
                                 lsm6dsr_sdo_pu_en_t *val);

typedef enum
{
  LSM6DSR_PULL_DOWN_CONNECT       = 0,
  LSM6DSR_PULL_DOWN_DISC          = 1,
} lsm6dsr_pd_dis_int1_t;
int32_t lsm6dsr_int1_mode_set(const stmdev_ctx_t *ctx,
                              lsm6dsr_pd_dis_int1_t val);
int32_t lsm6dsr_int1_mode_get(const stmdev_ctx_t *ctx,
                              lsm6dsr_pd_dis_int1_t *val);

typedef enum
{
  LSM6DSR_SPI_4_WIRE = 0,
  LSM6DSR_SPI_3_WIRE = 1,
} lsm6dsr_sim_t;
int32_t lsm6dsr_spi_mode_set(const stmdev_ctx_t *ctx,
                             lsm6dsr_sim_t val);
int32_t lsm6dsr_spi_mode_get(const stmdev_ctx_t *ctx,
                             lsm6dsr_sim_t *val);

typedef enum
{
  LSM6DSR_I2C_ENABLE  = 0,
  LSM6DSR_I2C_DISABLE = 1,
} lsm6dsr_i2c_disable_t;
int32_t lsm6dsr_i2c_interface_set(const stmdev_ctx_t *ctx,
                                  lsm6dsr_i2c_disable_t val);
int32_t lsm6dsr_i2c_interface_get(const stmdev_ctx_t *ctx,
                                  lsm6dsr_i2c_disable_t *val);

typedef enum
{
  LSM6DSR_I3C_DISABLE         = 0x80,
  LSM6DSR_I3C_ENABLE_T_50us   = 0x00,
  LSM6DSR_I3C_ENABLE_T_2us    = 0x01,
  LSM6DSR_I3C_ENABLE_T_1ms    = 0x02,
  LSM6DSR_I3C_ENABLE_T_25ms   = 0x03,
} lsm6dsr_i3c_disable_t;
int32_t lsm6dsr_i3c_disable_set(const stmdev_ctx_t *ctx,
                                lsm6dsr_i3c_disable_t val);
int32_t lsm6dsr_i3c_disable_get(const stmdev_ctx_t *ctx,
                                lsm6dsr_i3c_disable_t *val);

typedef struct
{
  lsm6dsr_int1_ctrl_t          int1_ctrl;
  lsm6dsr_md1_cfg_t            md1_cfg;
  lsm6dsr_emb_func_int1_t      emb_func_int1;
  lsm6dsr_fsm_int1_a_t         fsm_int1_a;
  lsm6dsr_fsm_int1_b_t         fsm_int1_b;
} lsm6dsr_pin_int1_route_t;
int32_t lsm6dsr_pin_int1_route_set(const stmdev_ctx_t *ctx,
                                   lsm6dsr_pin_int1_route_t *val);
int32_t lsm6dsr_pin_int1_route_get(const stmdev_ctx_t *ctx,
                                   lsm6dsr_pin_int1_route_t *val);

typedef struct
{
  lsm6dsr_int2_ctrl_t          int2_ctrl;
  lsm6dsr_md2_cfg_t            md2_cfg;
  lsm6dsr_emb_func_int2_t      emb_func_int2;
  lsm6dsr_fsm_int2_a_t         fsm_int2_a;
  lsm6dsr_fsm_int2_b_t         fsm_int2_b;
} lsm6dsr_pin_int2_route_t;
int32_t lsm6dsr_pin_int2_route_set(const stmdev_ctx_t *ctx,
                                   lsm6dsr_pin_int2_route_t *val);
int32_t lsm6dsr_pin_int2_route_get(const stmdev_ctx_t *ctx,
                                   lsm6dsr_pin_int2_route_t *val);

typedef enum
{
  LSM6DSR_PUSH_PULL   = 0,
  LSM6DSR_OPEN_DRAIN  = 1,
} lsm6dsr_pp_od_t;
int32_t lsm6dsr_pin_mode_set(const stmdev_ctx_t *ctx,
                             lsm6dsr_pp_od_t val);
int32_t lsm6dsr_pin_mode_get(const stmdev_ctx_t *ctx,
                             lsm6dsr_pp_od_t *val);

typedef enum
{
  LSM6DSR_ACTIVE_HIGH = 0,
  LSM6DSR_ACTIVE_LOW  = 1,
} lsm6dsr_h_lactive_t;
int32_t lsm6dsr_pin_polarity_set(const stmdev_ctx_t *ctx,
                                 lsm6dsr_h_lactive_t val);
int32_t lsm6dsr_pin_polarity_get(const stmdev_ctx_t *ctx,
                                 lsm6dsr_h_lactive_t *val);

int32_t lsm6dsr_all_on_int1_set(const stmdev_ctx_t *ctx, uint8_t val);
int32_t lsm6dsr_all_on_int1_get(const stmdev_ctx_t *ctx, uint8_t *val);

typedef enum
{
  LSM6DSR_ALL_INT_PULSED            = 0,
  LSM6DSR_BASE_LATCHED_EMB_PULSED   = 1,
  LSM6DSR_BASE_PULSED_EMB_LATCHED   = 2,
  LSM6DSR_ALL_INT_LATCHED           = 3,
} lsm6dsr_lir_t;
int32_t lsm6dsr_int_notification_set(const stmdev_ctx_t *ctx,
                                     lsm6dsr_lir_t val);
int32_t lsm6dsr_int_notification_get(const stmdev_ctx_t *ctx,
                                     lsm6dsr_lir_t *val);

typedef enum
{
  LSM6DSR_LSb_FS_DIV_64       = 0,
  LSM6DSR_LSb_FS_DIV_256      = 1,
} lsm6dsr_wake_ths_w_t;
int32_t lsm6dsr_wkup_ths_weight_set(const stmdev_ctx_t *ctx,
                                    lsm6dsr_wake_ths_w_t val);
int32_t lsm6dsr_wkup_ths_weight_get(const stmdev_ctx_t *ctx,
                                    lsm6dsr_wake_ths_w_t *val);

int32_t lsm6dsr_wkup_threshold_set(const stmdev_ctx_t *ctx, uint8_t val);
int32_t lsm6dsr_wkup_threshold_get(const stmdev_ctx_t *ctx,
                                   uint8_t *val);

int32_t lsm6dsr_xl_usr_offset_on_wkup_set(const stmdev_ctx_t *ctx,
                                          uint8_t val);
int32_t lsm6dsr_xl_usr_offset_on_wkup_get(const stmdev_ctx_t *ctx,
                                          uint8_t *val);

int32_t lsm6dsr_wkup_dur_set(const stmdev_ctx_t *ctx, uint8_t val);
int32_t lsm6dsr_wkup_dur_get(const stmdev_ctx_t *ctx, uint8_t *val);

int32_t lsm6dsr_gy_sleep_mode_set(const stmdev_ctx_t *ctx, uint8_t val);
int32_t lsm6dsr_gy_sleep_mode_get(const stmdev_ctx_t *ctx, uint8_t *val);

typedef enum
{
  LSM6DSR_DRIVE_SLEEP_CHG_EVENT = 0,
  LSM6DSR_DRIVE_SLEEP_STATUS    = 1,
} lsm6dsr_sleep_status_on_int_t;
int32_t lsm6dsr_act_pin_notification_set(const stmdev_ctx_t *ctx,
                                         lsm6dsr_sleep_status_on_int_t val);
int32_t lsm6dsr_act_pin_notification_get(const stmdev_ctx_t *ctx,
                                         lsm6dsr_sleep_status_on_int_t *val);

typedef enum
{
  LSM6DSR_XL_AND_GY_NOT_AFFECTED      = 0,
  LSM6DSR_XL_12Hz5_GY_NOT_AFFECTED    = 1,
  LSM6DSR_XL_12Hz5_GY_SLEEP           = 2,
  LSM6DSR_XL_12Hz5_GY_PD              = 3,
} lsm6dsr_inact_en_t;
int32_t lsm6dsr_act_mode_set(const stmdev_ctx_t *ctx,
                             lsm6dsr_inact_en_t val);
int32_t lsm6dsr_act_mode_get(const stmdev_ctx_t *ctx,
                             lsm6dsr_inact_en_t *val);

int32_t lsm6dsr_act_sleep_dur_set(const stmdev_ctx_t *ctx, uint8_t val);
int32_t lsm6dsr_act_sleep_dur_get(const stmdev_ctx_t *ctx, uint8_t *val);

int32_t lsm6dsr_tap_detection_on_z_set(const stmdev_ctx_t *ctx,
                                       uint8_t val);
int32_t lsm6dsr_tap_detection_on_z_get(const stmdev_ctx_t *ctx,
                                       uint8_t *val);

int32_t lsm6dsr_tap_detection_on_y_set(const stmdev_ctx_t *ctx,
                                       uint8_t val);
int32_t lsm6dsr_tap_detection_on_y_get(const stmdev_ctx_t *ctx,
                                       uint8_t *val);

int32_t lsm6dsr_tap_detection_on_x_set(const stmdev_ctx_t *ctx,
                                       uint8_t val);
int32_t lsm6dsr_tap_detection_on_x_get(const stmdev_ctx_t *ctx,
                                       uint8_t *val);

int32_t lsm6dsr_tap_threshold_x_set(const stmdev_ctx_t *ctx,
                                    uint8_t val);
int32_t lsm6dsr_tap_threshold_x_get(const stmdev_ctx_t *ctx,
                                    uint8_t *val);

typedef enum
{
  LSM6DSR_XYZ = 0,
  LSM6DSR_YXZ = 1,
  LSM6DSR_XZY = 2,
  LSM6DSR_ZYX = 3,
  LSM6DSR_YZX = 5,
  LSM6DSR_ZXY = 6,
} lsm6dsr_tap_priority_t;
int32_t lsm6dsr_tap_axis_priority_set(const stmdev_ctx_t *ctx,
                                      lsm6dsr_tap_priority_t val);
int32_t lsm6dsr_tap_axis_priority_get(const stmdev_ctx_t *ctx,
                                      lsm6dsr_tap_priority_t *val);

int32_t lsm6dsr_tap_threshold_y_set(const stmdev_ctx_t *ctx,
                                    uint8_t val);
int32_t lsm6dsr_tap_threshold_y_get(const stmdev_ctx_t *ctx,
                                    uint8_t *val);

int32_t lsm6dsr_tap_threshold_z_set(const stmdev_ctx_t *ctx,
                                    uint8_t val);
int32_t lsm6dsr_tap_threshold_z_get(const stmdev_ctx_t *ctx,
                                    uint8_t *val);

int32_t lsm6dsr_tap_shock_set(const stmdev_ctx_t *ctx, uint8_t val);
int32_t lsm6dsr_tap_shock_get(const stmdev_ctx_t *ctx, uint8_t *val);

int32_t lsm6dsr_tap_quiet_set(const stmdev_ctx_t *ctx, uint8_t val);
int32_t lsm6dsr_tap_quiet_get(const stmdev_ctx_t *ctx, uint8_t *val);

int32_t lsm6dsr_tap_dur_set(const stmdev_ctx_t *ctx, uint8_t val);
int32_t lsm6dsr_tap_dur_get(const stmdev_ctx_t *ctx, uint8_t *val);

typedef enum
{
  LSM6DSR_ONLY_SINGLE        = 0,
  LSM6DSR_BOTH_SINGLE_DOUBLE = 1,
} lsm6dsr_single_double_tap_t;
int32_t lsm6dsr_tap_mode_set(const stmdev_ctx_t *ctx,
                             lsm6dsr_single_double_tap_t val);
int32_t lsm6dsr_tap_mode_get(const stmdev_ctx_t *ctx,
                             lsm6dsr_single_double_tap_t *val);

typedef enum
{
  LSM6DSR_DEG_80  = 0,
  LSM6DSR_DEG_70  = 1,
  LSM6DSR_DEG_60  = 2,
  LSM6DSR_DEG_50  = 3,
} lsm6dsr_sixd_ths_t;
int32_t lsm6dsr_6d_threshold_set(const stmdev_ctx_t *ctx,
                                 lsm6dsr_sixd_ths_t val);
int32_t lsm6dsr_6d_threshold_get(const stmdev_ctx_t *ctx,
                                 lsm6dsr_sixd_ths_t *val);

int32_t lsm6dsr_4d_mode_set(const stmdev_ctx_t *ctx, uint8_t val);
int32_t lsm6dsr_4d_mode_get(const stmdev_ctx_t *ctx, uint8_t *val);

typedef enum
{
  LSM6DSR_FF_TSH_156mg = 0,
  LSM6DSR_FF_TSH_219mg = 1,
  LSM6DSR_FF_TSH_250mg = 2,
  LSM6DSR_FF_TSH_312mg = 3,
  LSM6DSR_FF_TSH_344mg = 4,
  LSM6DSR_FF_TSH_406mg = 5,
  LSM6DSR_FF_TSH_469mg = 6,
  LSM6DSR_FF_TSH_500mg = 7,
} lsm6dsr_ff_ths_t;
int32_t lsm6dsr_ff_threshold_set(const stmdev_ctx_t *ctx,
                                 lsm6dsr_ff_ths_t val);
int32_t lsm6dsr_ff_threshold_get(const stmdev_ctx_t *ctx,
                                 lsm6dsr_ff_ths_t *val);

int32_t lsm6dsr_ff_dur_set(const stmdev_ctx_t *ctx, uint8_t val);
int32_t lsm6dsr_ff_dur_get(const stmdev_ctx_t *ctx, uint8_t *val);

int32_t lsm6dsr_fifo_watermark_set(const stmdev_ctx_t *ctx,
                                   uint16_t val);
int32_t lsm6dsr_fifo_watermark_get(const stmdev_ctx_t *ctx,
                                   uint16_t *val);

int32_t lsm6dsr_compression_algo_init_set(const stmdev_ctx_t *ctx,
                                          uint8_t val);
int32_t lsm6dsr_compression_algo_init_get(const stmdev_ctx_t *ctx,
                                          uint8_t *val);

typedef enum
{
  LSM6DSR_CMP_DISABLE  = 0x00,
  LSM6DSR_CMP_ALWAYS   = 0x04,
  LSM6DSR_CMP_8_TO_1   = 0x05,
  LSM6DSR_CMP_16_TO_1  = 0x06,
  LSM6DSR_CMP_32_TO_1  = 0x07,
} lsm6dsr_uncoptr_rate_t;
int32_t lsm6dsr_compression_algo_set(const stmdev_ctx_t *ctx,
                                     lsm6dsr_uncoptr_rate_t val);
int32_t lsm6dsr_compression_algo_get(const stmdev_ctx_t *ctx,
                                     lsm6dsr_uncoptr_rate_t *val);

int32_t lsm6dsr_fifo_virtual_sens_odr_chg_set(const stmdev_ctx_t *ctx,
                                              uint8_t val);
int32_t lsm6dsr_fifo_virtual_sens_odr_chg_get(const stmdev_ctx_t *ctx,
                                              uint8_t *val);

int32_t lsm6dsr_compression_algo_real_time_set(const stmdev_ctx_t *ctx,
                                               uint8_t val);
int32_t lsm6dsr_compression_algo_real_time_get(const stmdev_ctx_t *ctx,
                                               uint8_t *val);

int32_t lsm6dsr_fifo_stop_on_wtm_set(const stmdev_ctx_t *ctx,
                                     uint8_t val);
int32_t lsm6dsr_fifo_stop_on_wtm_get(const stmdev_ctx_t *ctx,
                                     uint8_t *val);

typedef enum
{
  LSM6DSR_XL_NOT_BATCHED       =  0,
  LSM6DSR_XL_BATCHED_AT_12Hz5   =  1,
  LSM6DSR_XL_BATCHED_AT_26Hz    =  2,
  LSM6DSR_XL_BATCHED_AT_52Hz    =  3,
  LSM6DSR_XL_BATCHED_AT_104Hz   =  4,
  LSM6DSR_XL_BATCHED_AT_208Hz   =  5,
  LSM6DSR_XL_BATCHED_AT_417Hz   =  6,
  LSM6DSR_XL_BATCHED_AT_833Hz   =  7,
  LSM6DSR_XL_BATCHED_AT_1667Hz  =  8,
  LSM6DSR_XL_BATCHED_AT_3333Hz  =  9,
  LSM6DSR_XL_BATCHED_AT_6667Hz  = 10,
  LSM6DSR_XL_BATCHED_AT_6Hz5    = 11,
} lsm6dsr_bdr_xl_t;
int32_t lsm6dsr_fifo_xl_batch_set(const stmdev_ctx_t *ctx,
                                  lsm6dsr_bdr_xl_t val);
int32_t lsm6dsr_fifo_xl_batch_get(const stmdev_ctx_t *ctx,
                                  lsm6dsr_bdr_xl_t *val);

typedef enum
{
  LSM6DSR_GY_NOT_BATCHED         = 0,
  LSM6DSR_GY_BATCHED_AT_12Hz5    = 1,
  LSM6DSR_GY_BATCHED_AT_26Hz     = 2,
  LSM6DSR_GY_BATCHED_AT_52Hz     = 3,
  LSM6DSR_GY_BATCHED_AT_104Hz    = 4,
  LSM6DSR_GY_BATCHED_AT_208Hz    = 5,
  LSM6DSR_GY_BATCHED_AT_417Hz    = 6,
  LSM6DSR_GY_BATCHED_AT_833Hz    = 7,
  LSM6DSR_GY_BATCHED_AT_1667Hz   = 8,
  LSM6DSR_GY_BATCHED_AT_3333Hz   = 9,
  LSM6DSR_GY_BATCHED_AT_6667Hz   = 10,
  LSM6DSR_GY_BATCHED_6Hz5        = 11,
} lsm6dsr_bdr_gy_t;
int32_t lsm6dsr_fifo_gy_batch_set(const stmdev_ctx_t *ctx,
                                  lsm6dsr_bdr_gy_t val);
int32_t lsm6dsr_fifo_gy_batch_get(const stmdev_ctx_t *ctx,
                                  lsm6dsr_bdr_gy_t *val);

typedef enum
{
  LSM6DSR_BYPASS_MODE             = 0,
  LSM6DSR_FIFO_MODE               = 1,
  LSM6DSR_STREAM_TO_FIFO_MODE     = 3,
  LSM6DSR_BYPASS_TO_STREAM_MODE   = 4,
  LSM6DSR_STREAM_MODE             = 6,
  LSM6DSR_BYPASS_TO_FIFO_MODE     = 7,
} lsm6dsr_fifo_mode_t;
int32_t lsm6dsr_fifo_mode_set(const stmdev_ctx_t *ctx,
                              lsm6dsr_fifo_mode_t val);
int32_t lsm6dsr_fifo_mode_get(const stmdev_ctx_t *ctx,
                              lsm6dsr_fifo_mode_t *val);
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
