ForgetfulDuck/MIP-Watch/MIP-STM32/Core/Src/lsm6dsr_reg.c

/**
  ******************************************************************************
  * @file    lsm6dsr_reg.c
  * @author  Sensors Software Solution Team
  * @brief   LSM6DSR driver file
  ******************************************************************************
  * @attention
  *
  * Copyright (c) 2021 STMicroelectronics.
  * All rights reserved.
  *
  * This software is licensed under terms that can be found in the LICENSE file
  * in the root directory of this software component.
  * If no LICENSE file comes with this software, it is provided AS-IS.
  *
  ******************************************************************************
  */

#include "lsm6dsr_reg.h"

/**
  * @defgroup    LSM6DSR
  * @brief       This file provides a set of functions needed to drive the
  *              lsm6dsr enhanced inertial module.
  * @{
  *
  */

/**
  * @defgroup    LSM6DSR_Interfaces_Functions
  * @brief       This section provide a set of functions used to read and
  *              write a generic register of the device.
  *              MANDATORY: return 0 -> no Error.
  * @{
  *
  */

/**
  * @brief  Read generic device register
  *
  * @param  ctx   read / write interface definitions(ptr)
  * @param  reg   register to read
  * @param  data  pointer to buffer that store the data read(ptr)
  * @param  len   number of consecutive register to read
  * @retval       interface status (MANDATORY: return 0 -> no Error)
  *
  */
int32_t __weak lsm6dsr_read_reg(const stmdev_ctx_t *ctx, uint8_t reg,
                                uint8_t *data,
                                uint16_t len)
{
  int32_t ret;

  if (ctx == NULL)
  {
    return -1;
  }

  ret = ctx->read_reg(ctx->handle, reg, data, len);
  return ret;
}

/**
  * @brief  Write generic device register
  *
  * @param  ctx   read / write interface definitions(ptr)
  * @param  reg   register to write
  * @param  data  pointer to data to write in register reg(ptr)
  * @param  len   number of consecutive register to write
  * @retval       interface status (MANDATORY: return 0 -> no Error)
  *
  */
int32_t __weak lsm6dsr_write_reg(const stmdev_ctx_t *ctx, uint8_t reg,
                                 uint8_t *data,
                                 uint16_t len)
{
  int32_t ret;

  if (ctx == NULL)
  {
    return -1;
  }

  ret = ctx->write_reg(ctx->handle, reg, data, len);
  return ret;
}

/**
  * @}
  *
  */

/**
  * @defgroup    LSM6DSR_Sensitivity
  * @brief       These functions convert raw-data into engineering units.
  * @{
  *
  */

float_t lsm6dsr_from_fs2g_to_mg(int16_t lsb)
{
  return ((float_t)lsb * 0.061f);
}

float_t lsm6dsr_from_fs4g_to_mg(int16_t lsb)
{
  return ((float_t)lsb * 0.122f);
}

float_t lsm6dsr_from_fs8g_to_mg(int16_t lsb)
{
  return ((float_t)lsb * 0.244f);
}

float_t lsm6dsr_from_fs16g_to_mg(int16_t lsb)
{
  return ((float_t)lsb * 0.488f);
}

float_t lsm6dsr_from_fs125dps_to_mdps(int16_t lsb)
{
  return ((float_t)lsb * 4.375f);
}

float_t lsm6dsr_from_fs250dps_to_mdps(int16_t lsb)
{
  return ((float_t)lsb * 8.75f);
}

float_t lsm6dsr_from_fs500dps_to_mdps(int16_t lsb)
{
  return ((float_t)lsb * 17.50f);
}

float_t lsm6dsr_from_fs1000dps_to_mdps(int16_t lsb)
{
  return ((float_t)lsb * 35.0f);
}

float_t lsm6dsr_from_fs2000dps_to_mdps(int16_t lsb)
{
  return ((float_t)lsb * 70.0f);
}

float_t lsm6dsr_from_fs4000dps_to_mdps(int16_t lsb)
{
  return ((float_t)lsb * 140.0f);
}

float_t lsm6dsr_from_lsb_to_celsius(int16_t lsb)
{
  return (((float_t)lsb / 256.0f) + 25.0f);
}

uint64_t lsm6dsr_from_lsb_to_nsec(uint32_t lsb)
{
  return ((uint64_t)lsb * 25000ULL);
}

/**
  * @}
  *
  */

/**
  * @defgroup   LSM9DS1_Data_generation
  * @brief      This section groups all the functions concerning data
  *             generation
  * @{
  *
  */

/**
  * @brief  Accelerometer full-scale selection[set]
  *
  * @param  ctx    Read / write interface definitions.(ptr)
  * @param  val    Change the values of fs_xl in reg CTRL1_XL
  * @retval        Interface status (MANDATORY: return 0 -> no Error).
  *
  */
int32_t lsm6dsr_xl_full_scale_set(const stmdev_ctx_t *ctx,
                                  lsm6dsr_fs_xl_t val)
{
  lsm6dsr_ctrl1_xl_t ctrl1_xl;
  int32_t ret;
  ret = lsm6dsr_read_reg(ctx, LSM6DSR_CTRL1_XL,
                         (uint8_t *)&ctrl1_xl, 1);

  if (ret == 0)
  {
    ctrl1_xl.fs_xl = (uint8_t)val;
    ret = lsm6dsr_write_reg(ctx, LSM6DSR_CTRL1_XL,
                            (uint8_t *)&ctrl1_xl, 1);
  }

  return ret;
}

/**
  * @brief  Accelerometer full-scale selection.[get]
  *
  * @param  ctx    Read / write interface definitions.(ptr)
  * @param  val    Get the values of fs_xl in reg CTRL1_XL
  * @retval        Interface status (MANDATORY: return 0 -> no Error).
  *
  */
int32_t lsm6dsr_xl_full_scale_get(const stmdev_ctx_t *ctx,
                                  lsm6dsr_fs_xl_t *val)
{
  lsm6dsr_ctrl1_xl_t ctrl1_xl;
  int32_t ret;
  ret = lsm6dsr_read_reg(ctx, LSM6DSR_CTRL1_XL,
                         (uint8_t *)&ctrl1_xl, 1);

  switch (ctrl1_xl.fs_xl)
  {
    case LSM6DSR_2g:
      *val = LSM6DSR_2g;
      break;

    case LSM6DSR_16g:
      *val = LSM6DSR_16g;
      break;

    case LSM6DSR_4g:
      *val = LSM6DSR_4g;
      break;

    case LSM6DSR_8g:
      *val = LSM6DSR_8g;
      break;

    default:
      *val = LSM6DSR_2g;
      break;
  }

  return ret;
}

/**
  * @brief  Accelerometer UI data rate selection.[set]
  *
  * @param  ctx    Read / write interface definitions.(ptr)
  * @param  val    Change the values of odr_xl in reg CTRL1_XL
  * @retval        Interface status (MANDATORY: return 0 -> no Error).
  *
  */
int32_t lsm6dsr_xl_data_rate_set(const stmdev_ctx_t *ctx,
                                 lsm6dsr_odr_xl_t val)
{
  lsm6dsr_odr_xl_t odr_xl =  val;
  lsm6dsr_emb_fsm_enable_t fsm_enable;
  lsm6dsr_fsm_odr_t fsm_odr;
  lsm6dsr_ctrl1_xl_t ctrl1_xl;
  int32_t ret;

  /* Check the Finite State Machine data rate constraints */
  ret =  lsm6dsr_fsm_enable_get(ctx, &fsm_enable);

  if (ret == 0)
  {
    if ((fsm_enable.fsm_enable_a.fsm1_en  |
         fsm_enable.fsm_enable_a.fsm2_en  |
         fsm_enable.fsm_enable_a.fsm3_en  |
         fsm_enable.fsm_enable_a.fsm4_en  |
         fsm_enable.fsm_enable_a.fsm5_en  |
         fsm_enable.fsm_enable_a.fsm6_en  |
         fsm_enable.fsm_enable_a.fsm7_en  |
         fsm_enable.fsm_enable_a.fsm8_en  |
         fsm_enable.fsm_enable_b.fsm9_en  |
         fsm_enable.fsm_enable_b.fsm10_en |
         fsm_enable.fsm_enable_b.fsm11_en |
         fsm_enable.fsm_enable_b.fsm12_en |
         fsm_enable.fsm_enable_b.fsm13_en |
         fsm_enable.fsm_enable_b.fsm14_en |
         fsm_enable.fsm_enable_b.fsm15_en |
         fsm_enable.fsm_enable_b.fsm16_en) == PROPERTY_ENABLE)
    {
      ret =  lsm6dsr_fsm_data_rate_get(ctx, &fsm_odr);

      if (ret == 0)
      {
        switch (fsm_odr)
        {
          case LSM6DSR_ODR_FSM_12Hz5:
            if (val == LSM6DSR_XL_ODR_OFF)
            {
              odr_xl = LSM6DSR_XL_ODR_12Hz5;
            }

            else
            {
              odr_xl = val;
            }

            break;

          case LSM6DSR_ODR_FSM_26Hz:
            if (val == LSM6DSR_XL_ODR_OFF)
            {
              odr_xl = LSM6DSR_XL_ODR_26Hz;
            }

            else if (val == LSM6DSR_XL_ODR_12Hz5)
            {
              odr_xl = LSM6DSR_XL_ODR_26Hz;
            }

            else
            {
              odr_xl = val;
            }

            break;

          case LSM6DSR_ODR_FSM_52Hz:
            if (val == LSM6DSR_XL_ODR_OFF)
            {
              odr_xl = LSM6DSR_XL_ODR_52Hz;
            }

            else if (val == LSM6DSR_XL_ODR_12Hz5)
            {
              odr_xl = LSM6DSR_XL_ODR_52Hz;
            }

            else if (val == LSM6DSR_XL_ODR_26Hz)
            {
              odr_xl = LSM6DSR_XL_ODR_52Hz;
            }

            else
            {
              odr_xl = val;
            }

            break;

          case LSM6DSR_ODR_FSM_104Hz:
            if (val == LSM6DSR_XL_ODR_OFF)
            {
              odr_xl = LSM6DSR_XL_ODR_104Hz;
            }

            else if (val == LSM6DSR_XL_ODR_12Hz5)
            {
              odr_xl = LSM6DSR_XL_ODR_104Hz;
            }

            else if (val == LSM6DSR_XL_ODR_26Hz)
            {
              odr_xl = LSM6DSR_XL_ODR_104Hz;
            }

            else if (val == LSM6DSR_XL_ODR_52Hz)
            {
              odr_xl = LSM6DSR_XL_ODR_104Hz;
            }

            else
            {
              odr_xl = val;
            }

            break;

          default:
            odr_xl = val;
            break;
        }
      }
    }
  }

  if (ret == 0)
  {
    ret = lsm6dsr_read_reg(ctx, LSM6DSR_CTRL1_XL,
                           (uint8_t *)&ctrl1_xl, 1);
  }

  if (ret == 0)
  {
    ctrl1_xl.odr_xl = (uint8_t)odr_xl;
    ret = lsm6dsr_write_reg(ctx, LSM6DSR_CTRL1_XL,
                            (uint8_t *)&ctrl1_xl, 1);
  }

  return ret;
}

/**
  * @brief  Accelerometer UI data rate selection.[get]
  *
  * @param  ctx    Read / write interface definitions.(ptr)
  * @param  val    Get the values of odr_xl in reg CTRL1_XL
  * @retval        Interface status (MANDATORY: return 0 -> no Error).
  *
  */
int32_t lsm6dsr_xl_data_rate_get(const stmdev_ctx_t *ctx,
                                 lsm6dsr_odr_xl_t *val)
{
  lsm6dsr_ctrl1_xl_t ctrl1_xl;
  int32_t ret;
  ret = lsm6dsr_read_reg(ctx, LSM6DSR_CTRL1_XL,
                         (uint8_t *)&ctrl1_xl, 1);

  switch (ctrl1_xl.odr_xl)
  {
    case LSM6DSR_XL_ODR_OFF:
      *val = LSM6DSR_XL_ODR_OFF;
      break;

    case LSM6DSR_XL_ODR_12Hz5:
      *val = LSM6DSR_XL_ODR_12Hz5;
      break;

    case LSM6DSR_XL_ODR_26Hz:
      *val = LSM6DSR_XL_ODR_26Hz;
      break;

    case LSM6DSR_XL_ODR_52Hz:
      *val = LSM6DSR_XL_ODR_52Hz;
      break;

    case LSM6DSR_XL_ODR_104Hz:
      *val = LSM6DSR_XL_ODR_104Hz;
      break;

    case LSM6DSR_XL_ODR_208Hz:
      *val = LSM6DSR_XL_ODR_208Hz;
      break;

    case LSM6DSR_XL_ODR_416Hz:
      *val = LSM6DSR_XL_ODR_416Hz;
      break;

    case LSM6DSR_XL_ODR_833Hz:
      *val = LSM6DSR_XL_ODR_833Hz;
      break;

    case LSM6DSR_XL_ODR_1666Hz:
      *val = LSM6DSR_XL_ODR_1666Hz;
      break;

    case LSM6DSR_XL_ODR_3332Hz:
      *val = LSM6DSR_XL_ODR_3332Hz;
      break;

    case LSM6DSR_XL_ODR_6667Hz:
      *val = LSM6DSR_XL_ODR_6667Hz;
      break;

    case LSM6DSR_XL_ODR_1Hz6:
      *val = LSM6DSR_XL_ODR_1Hz6;
      break;

    default:
      *val = LSM6DSR_XL_ODR_OFF;
      break;
  }

  return ret;
}

/**
  * @brief  Gyroscope UI chain full-scale selection.[set]
  *
  * @param  ctx    Read / write interface definitions.(ptr)
  * @param  val    Change the values of fs_g in reg CTRL2_G
  * @retval        Interface status (MANDATORY: return 0 -> no Error).
  *
  */
int32_t lsm6dsr_gy_full_scale_set(const stmdev_ctx_t *ctx,
                                  lsm6dsr_fs_g_t val)
{
  lsm6dsr_ctrl2_g_t ctrl2_g;
  int32_t ret;
  ret = lsm6dsr_read_reg(ctx, LSM6DSR_CTRL2_G,
                         (uint8_t *)&ctrl2_g, 1);

  if (ret == 0)
  {
    ctrl2_g.fs_g = (uint8_t)val;
    ret = lsm6dsr_write_reg(ctx, LSM6DSR_CTRL2_G,
                            (uint8_t *)&ctrl2_g, 1);
  }

  return ret;
}

/**
  * @brief  Gyroscope UI chain full-scale selection.[get]
  *
  * @param  ctx    Read / write interface definitions.(ptr)
  * @param  val    Get the values of fs_g in reg CTRL2_G
  * @retval        Interface status (MANDATORY: return 0 -> no Error).
  *
  */
int32_t lsm6dsr_gy_full_scale_get(const stmdev_ctx_t *ctx,
                                  lsm6dsr_fs_g_t *val)
{
  lsm6dsr_ctrl2_g_t ctrl2_g;
  int32_t ret;
  ret = lsm6dsr_read_reg(ctx, LSM6DSR_CTRL2_G,
                         (uint8_t *)&ctrl2_g, 1);

  switch (ctrl2_g.fs_g)
  {
    case LSM6DSR_125dps:
      *val = LSM6DSR_125dps;
      break;

    case LSM6DSR_250dps:
      *val = LSM6DSR_250dps;
      break;

    case LSM6DSR_500dps:
      *val = LSM6DSR_500dps;
      break;

    case LSM6DSR_1000dps:
      *val = LSM6DSR_1000dps;
      break;

    case LSM6DSR_2000dps:
      *val = LSM6DSR_2000dps;
      break;

    case LSM6DSR_4000dps:
      *val = LSM6DSR_4000dps;
      break;

    default:
      *val = LSM6DSR_125dps;
      break;
  }

  return ret;
}

/**
  * @brief  Gyroscope data rate.[set]
  *
  * @param  ctx    Read / write interface definitions.(ptr)
  * @param  val    Change the values of odr_g in reg CTRL2_G
  * @retval        Interface status (MANDATORY: return 0 -> no Error).
  *
  */
int32_t lsm6dsr_gy_data_rate_set(const stmdev_ctx_t *ctx,
                                 lsm6dsr_odr_g_t val)
{
  lsm6dsr_odr_g_t odr_gy =  val;
  lsm6dsr_emb_fsm_enable_t fsm_enable;
  lsm6dsr_fsm_odr_t fsm_odr;
  lsm6dsr_ctrl2_g_t ctrl2_g;
  int32_t ret;

  /* Check the Finite State Machine data rate constraints */
  ret =  lsm6dsr_fsm_enable_get(ctx, &fsm_enable);

  if (ret == 0)
  {
    if ((fsm_enable.fsm_enable_a.fsm1_en  |
         fsm_enable.fsm_enable_a.fsm2_en  |
         fsm_enable.fsm_enable_a.fsm3_en  |
         fsm_enable.fsm_enable_a.fsm4_en  |
         fsm_enable.fsm_enable_a.fsm5_en  |
         fsm_enable.fsm_enable_a.fsm6_en  |
         fsm_enable.fsm_enable_a.fsm7_en  |
         fsm_enable.fsm_enable_a.fsm8_en  |
         fsm_enable.fsm_enable_b.fsm9_en  |
         fsm_enable.fsm_enable_b.fsm10_en |
         fsm_enable.fsm_enable_b.fsm11_en |
         fsm_enable.fsm_enable_b.fsm12_en |
         fsm_enable.fsm_enable_b.fsm13_en |
         fsm_enable.fsm_enable_b.fsm14_en |
         fsm_enable.fsm_enable_b.fsm15_en |
         fsm_enable.fsm_enable_b.fsm16_en) == PROPERTY_ENABLE)
    {
      ret =  lsm6dsr_fsm_data_rate_get(ctx, &fsm_odr);

      if (ret == 0)
      {
        switch (fsm_odr)
        {
          case LSM6DSR_ODR_FSM_12Hz5:
            if (val == LSM6DSR_GY_ODR_OFF)
            {
              odr_gy = LSM6DSR_GY_ODR_12Hz5;
            }

            else
            {
              odr_gy = val;
            }

            break;

          case LSM6DSR_ODR_FSM_26Hz:
            if (val == LSM6DSR_GY_ODR_OFF)
            {
              odr_gy = LSM6DSR_GY_ODR_26Hz;
            }

            else if (val == LSM6DSR_GY_ODR_12Hz5)
            {
              odr_gy = LSM6DSR_GY_ODR_26Hz;
            }

            else
            {
              odr_gy = val;
            }

            break;

          case LSM6DSR_ODR_FSM_52Hz:
            if (val == LSM6DSR_GY_ODR_OFF)
            {
              odr_gy = LSM6DSR_GY_ODR_52Hz;
            }

            else if (val == LSM6DSR_GY_ODR_12Hz5)
            {
              odr_gy = LSM6DSR_GY_ODR_52Hz;
            }

            else if (val == LSM6DSR_GY_ODR_26Hz)
            {
              odr_gy = LSM6DSR_GY_ODR_52Hz;
            }

            else
            {
              odr_gy = val;
            }

            break;

          case LSM6DSR_ODR_FSM_104Hz:
            if (val == LSM6DSR_GY_ODR_OFF)
            {
              odr_gy = LSM6DSR_GY_ODR_104Hz;
            }

            else if (val == LSM6DSR_GY_ODR_12Hz5)
            {
              odr_gy = LSM6DSR_GY_ODR_104Hz;
            }

            else if (val == LSM6DSR_GY_ODR_26Hz)
            {
              odr_gy = LSM6DSR_GY_ODR_104Hz;
            }

            else if (val == LSM6DSR_GY_ODR_52Hz)
            {
              odr_gy = LSM6DSR_GY_ODR_104Hz;
            }

            else
            {
              odr_gy = val;
            }

            break;

          default:
            odr_gy = val;
            break;
        }
      }
    }
  }

  if (ret == 0)
  {
    ret = lsm6dsr_read_reg(ctx, LSM6DSR_CTRL2_G,
                           (uint8_t *)&ctrl2_g, 1);
  }

  if (ret == 0)
  {
    ctrl2_g.odr_g = (uint8_t)odr_gy;
    ret = lsm6dsr_write_reg(ctx, LSM6DSR_CTRL2_G,
                            (uint8_t *)&ctrl2_g, 1);
  }

  return ret;
}

/**
  * @brief  Gyroscope data rate.[get]
  *
  * @param  ctx    Read / write interface definitions.(ptr)
  * @param  val    Get the values of odr_g in reg CTRL2_G
  * @retval        Interface status (MANDATORY: return 0 -> no Error).
  *
  */
int32_t lsm6dsr_gy_data_rate_get(const stmdev_ctx_t *ctx,
                                 lsm6dsr_odr_g_t *val)
{
  lsm6dsr_ctrl2_g_t ctrl2_g;
  int32_t ret;
  ret = lsm6dsr_read_reg(ctx, LSM6DSR_CTRL2_G,
                         (uint8_t *)&ctrl2_g, 1);

  switch (ctrl2_g.odr_g)
  {
    case LSM6DSR_GY_ODR_OFF:
      *val = LSM6DSR_GY_ODR_OFF;
      break;

    case LSM6DSR_GY_ODR_12Hz5:
      *val = LSM6DSR_GY_ODR_12Hz5;
      break;

    case LSM6DSR_GY_ODR_26Hz:
      *val = LSM6DSR_GY_ODR_26Hz;
      break;

    case LSM6DSR_GY_ODR_52Hz:
      *val = LSM6DSR_GY_ODR_52Hz;
      break;

    case LSM6DSR_GY_ODR_104Hz:
      *val = LSM6DSR_GY_ODR_104Hz;
      break;

    case LSM6DSR_GY_ODR_208Hz:
      *val = LSM6DSR_GY_ODR_208Hz;
      break;

    case LSM6DSR_GY_ODR_416Hz:
      *val = LSM6DSR_GY_ODR_416Hz;
      break;

    case LSM6DSR_GY_ODR_833Hz:
      *val = LSM6DSR_GY_ODR_833Hz;
      break;

    case LSM6DSR_GY_ODR_1666Hz:
      *val = LSM6DSR_GY_ODR_1666Hz;
      break;

    case LSM6DSR_GY_ODR_3332Hz:
      *val = LSM6DSR_GY_ODR_3332Hz;
      break;

    case LSM6DSR_GY_ODR_6667Hz:
      *val = LSM6DSR_GY_ODR_6667Hz;
      break;

    default:
      *val = LSM6DSR_GY_ODR_OFF;
      break;
  }

  return ret;
}

/**
  * @brief  Block data update.[set]
  *
  * @param  ctx    Read / write interface definitions.(ptr)
  * @param  val    Change the values of bdu in reg CTRL3_C
  * @retval        Interface status (MANDATORY: return 0 -> no Error).
  *
  */
int32_t lsm6dsr_block_data_update_set(const stmdev_ctx_t *ctx,
                                      uint8_t val)
{
  lsm6dsr_ctrl3_c_t ctrl3_c;
  int32_t ret;
  ret = lsm6dsr_read_reg(ctx, LSM6DSR_CTRL3_C,
                         (uint8_t *)&ctrl3_c, 1);

  if (ret == 0)
  {
    ctrl3_c.bdu = (uint8_t)val;
    ret = lsm6dsr_write_reg(ctx, LSM6DSR_CTRL3_C,
                            (uint8_t *)&ctrl3_c, 1);
  }

  return ret;
}

/**
  * @brief  Block data update.[get]
  *
  * @param  ctx    Read / write interface definitions.(ptr)
  * @param  val    Change the values of bdu in reg CTRL3_C
  * @retval        Interface status (MANDATORY: return 0 -> no Error).
  *
  */
int32_t lsm6dsr_block_data_update_get(const stmdev_ctx_t *ctx,
                                      uint8_t *val)
{
  lsm6dsr_ctrl3_c_t ctrl3_c;
  int32_t ret;
  ret = lsm6dsr_read_reg(ctx, LSM6DSR_CTRL3_C,
                         (uint8_t *)&ctrl3_c, 1);
  *val = ctrl3_c.bdu;

  return ret;
}

/**
  * @brief  Weight of XL user offset bits of registers X_OFS_USR (73h),
  *         Y_OFS_USR (74h), Z_OFS_USR (75h).[set]
  *
  * @param  ctx    Read / write interface definitions.(ptr)
  * @param  val    Change the values of usr_off_w in reg CTRL6_C
  * @retval        Interface status (MANDATORY: return 0 -> no Error).
  *
  */
int32_t lsm6dsr_xl_offset_weight_set(const stmdev_ctx_t *ctx,
                                     lsm6dsr_usr_off_w_t val)
{
  lsm6dsr_ctrl6_c_t ctrl6_c;
  int32_t ret;
  ret = lsm6dsr_read_reg(ctx, LSM6DSR_CTRL6_C,
                         (uint8_t *)&ctrl6_c, 1);

  if (ret == 0)
  {
    ctrl6_c.usr_off_w = (uint8_t)val;
    ret = lsm6dsr_write_reg(ctx, LSM6DSR_CTRL6_C,
                            (uint8_t *)&ctrl6_c, 1);
  }

  return ret;
}

/**
  * @brief  Weight of XL user offset bits of registers X_OFS_USR (73h),
  *         Y_OFS_USR (74h), Z_OFS_USR (75h).[get]
  *
  * @param  ctx    Read / write interface definitions.(ptr)
  * @param  val    Get the values of usr_off_w in reg CTRL6_C
  * @retval        Interface status (MANDATORY: return 0 -> no Error).
  *
  */
int32_t lsm6dsr_xl_offset_weight_get(const stmdev_ctx_t *ctx,
                                     lsm6dsr_usr_off_w_t *val)
{
  lsm6dsr_ctrl6_c_t ctrl6_c;
  int32_t ret;
  ret = lsm6dsr_read_reg(ctx, LSM6DSR_CTRL6_C,
                         (uint8_t *)&ctrl6_c, 1);

  switch (ctrl6_c.usr_off_w)
  {
    case LSM6DSR_LSb_1mg:
      *val = LSM6DSR_LSb_1mg;
      break;

    case LSM6DSR_LSb_16mg:
      *val = LSM6DSR_LSb_16mg;
      break;

    default:
      *val = LSM6DSR_LSb_1mg;
      break;
  }

  return ret;
}

/**
  * @brief  Accelerometer power mode.[set]
  *
  * @param  ctx    Read / write interface definitions.(ptr)
  * @param  val    Change the values of xl_hm_mode in reg CTRL6_C
  * @retval        Interface status (MANDATORY: return 0 -> no Error).
  *
  */
int32_t lsm6dsr_xl_power_mode_set(const stmdev_ctx_t *ctx,
                                  lsm6dsr_xl_hm_mode_t val)
{
  lsm6dsr_ctrl6_c_t ctrl6_c;
  int32_t ret;
  ret = lsm6dsr_read_reg(ctx, LSM6DSR_CTRL6_C,
                         (uint8_t *)&ctrl6_c, 1);

  if (ret == 0)
  {
    ctrl6_c.xl_hm_mode = (uint8_t)val & 0x01U;
    ret = lsm6dsr_write_reg(ctx, LSM6DSR_CTRL6_C,
                            (uint8_t *)&ctrl6_c, 1);
  }

  return ret;
}

/**
  * @brief  Accelerometer power mode[get]
  *
  * @param  ctx    Read / write interface definitions.(ptr)
  * @param  val    Get the values of xl_hm_mode in reg CTRL6_C
  * @retval        Interface status (MANDATORY: return 0 -> no Error).
  *
  */
int32_t lsm6dsr_xl_power_mode_get(const stmdev_ctx_t *ctx,
                                  lsm6dsr_xl_hm_mode_t *val)
{
  lsm6dsr_ctrl6_c_t ctrl6_c;
  int32_t ret;
  ret = lsm6dsr_read_reg(ctx, LSM6DSR_CTRL6_C,
                         (uint8_t *)&ctrl6_c, 1);

  switch (ctrl6_c.xl_hm_mode)
  {
    case LSM6DSR_HIGH_PERFORMANCE_MD:
      *val = LSM6DSR_HIGH_PERFORMANCE_MD;
      break;

    case LSM6DSR_LOW_NORMAL_POWER_MD:
      *val = LSM6DSR_LOW_NORMAL_POWER_MD;
      break;

    default:
      *val = LSM6DSR_HIGH_PERFORMANCE_MD;
      break;
  }

  return ret;
}

/**
  * @brief  Operating mode for gyroscope.[set]
  *
  * @param  ctx    Read / write interface definitions.(ptr)
  * @param  val    Change the values of g_hm_mode in reg CTRL7_G
  * @retval        Interface status (MANDATORY: return 0 -> no Error).
  *
  */
int32_t lsm6dsr_gy_power_mode_set(const stmdev_ctx_t *ctx,
                                  lsm6dsr_g_hm_mode_t val)
{
  lsm6dsr_ctrl7_g_t ctrl7_g;
  int32_t ret;
  ret = lsm6dsr_read_reg(ctx, LSM6DSR_CTRL7_G,
                         (uint8_t *)&ctrl7_g, 1);

  if (ret == 0)
  {
    ctrl7_g.g_hm_mode = (uint8_t)val;
    ret = lsm6dsr_write_reg(ctx, LSM6DSR_CTRL7_G,
                            (uint8_t *)&ctrl7_g, 1);
  }

  return ret;
}

/**
  * @brief  gy_power_mode: [get]  Operating mode for gyroscope.
  *
  * @param  ctx    Read / write interface definitions.(ptr)
  * @param  val    Get the values of g_hm_mode in reg CTRL7_G
  * @retval        Interface status (MANDATORY: return 0 -> no Error).
  *
  */
int32_t lsm6dsr_gy_power_mode_get(const stmdev_ctx_t *ctx,
                                  lsm6dsr_g_hm_mode_t *val)
{
  lsm6dsr_ctrl7_g_t ctrl7_g;
  int32_t ret;
  ret = lsm6dsr_read_reg(ctx, LSM6DSR_CTRL7_G,
                         (uint8_t *)&ctrl7_g, 1);

  switch (ctrl7_g.g_hm_mode)
  {
    case LSM6DSR_GY_HIGH_PERFORMANCE:
      *val = LSM6DSR_GY_HIGH_PERFORMANCE;
      break;

    case LSM6DSR_GY_NORMAL:
      *val = LSM6DSR_GY_NORMAL;
      break;

    default:
      *val = LSM6DSR_GY_HIGH_PERFORMANCE;
      break;
  }

  return ret;
}

/**
  * @brief  Read all the interrupt flag of the device.
  *[get]
  * @param  ctx    Read / write interface definitions.(ptr)
  * @param  val    Get registers ALL_INT_SRC; WAKE_UP_SRC;
  *                              TAP_SRC; D6D_SRC; STATUS_REG;
  *                              EMB_FUNC_STATUS; FSM_STATUS_A/B
  * @retval        Interface status (MANDATORY: return 0 -> no Error).
  *
  */
int32_t lsm6dsr_all_sources_get(const stmdev_ctx_t *ctx,
                                lsm6dsr_all_sources_t *val)
{
  int32_t ret;

  ret = lsm6dsr_read_reg(ctx, LSM6DSR_ALL_INT_SRC,
                         (uint8_t *)&val->all_int_src, 1);

  if (ret == 0)
  {
    ret = lsm6dsr_read_reg(ctx, LSM6DSR_WAKE_UP_SRC,
                           (uint8_t *)&val->wake_up_src, 1);
  }

  if (ret == 0)
  {
    ret = lsm6dsr_read_reg(ctx, LSM6DSR_TAP_SRC,
                           (uint8_t *)&val->tap_src, 1);
  }

  if (ret == 0)
  {
    ret = lsm6dsr_read_reg(ctx, LSM6DSR_D6D_SRC,
                           (uint8_t *)&val->d6d_src, 1);
  }

  if (ret == 0)
  {
    ret = lsm6dsr_read_reg(ctx, LSM6DSR_STATUS_REG,
                           (uint8_t *)&val->status_reg, 1);
  }

  if (ret == 0)
  {
    ret = lsm6dsr_mem_bank_set(ctx, LSM6DSR_EMBEDDED_FUNC_BANK);
  }

  if (ret == 0)
  {
    ret = lsm6dsr_read_reg(ctx, LSM6DSR_EMB_FUNC_STATUS,
                           (uint8_t *)&val->emb_func_status, 1);
  }

  if (ret == 0)
  {
    ret = lsm6dsr_read_reg(ctx, LSM6DSR_FSM_STATUS_A,
                           (uint8_t *)&val->fsm_status_a, 1);
  }

  if (ret == 0)
  {
    ret = lsm6dsr_read_reg(ctx, LSM6DSR_FSM_STATUS_B,
                           (uint8_t *)&val->fsm_status_b, 1);
  }

  if (ret == 0)
  {
    ret = lsm6dsr_mem_bank_set(ctx, LSM6DSR_USER_BANK);
  }

  return ret;
}

/**
  * @brief  The STATUS_REG register is read by the primary interface.[get]
  *
  * @param  ctx    Read / write interface definitions.(ptr)
  * @param  val    Get register STATUS_REG
  * @retval        Interface status (MANDATORY: return 0 -> no Error).
  *
  */
int32_t lsm6dsr_status_reg_get(const stmdev_ctx_t *ctx,
                               lsm6dsr_status_reg_t *val)
{
  int32_t ret;

  ret = lsm6dsr_read_reg(ctx, LSM6DSR_STATUS_REG, (uint8_t *) val, 1);

  return ret;
}

/**
  * @brief  Accelerometer new data available.[get]
  *
  * @param  ctx    Read / write interface definitions.(ptr)
  * @param  val    Change the values of xlda in reg STATUS_REG
  * @retval        Interface status (MANDATORY: return 0 -> no Error).
  *
  */
int32_t lsm6dsr_xl_flag_data_ready_get(const stmdev_ctx_t *ctx,
                                       uint8_t *val)
{
  lsm6dsr_status_reg_t status_reg;
  int32_t ret;

  ret = lsm6dsr_read_reg(ctx, LSM6DSR_STATUS_REG,
                         (uint8_t *)&status_reg, 1);
  *val = status_reg.xlda;

  return ret;
}

/**
  * @brief  Gyroscope new data available.[get]
  *
  * @param  ctx    Read / write interface definitions.(ptr)
  * @param  val    Change the values of gda in reg STATUS_REG
  * @retval        Interface status (MANDATORY: return 0 -> no Error).
  *
  */
int32_t lsm6dsr_gy_flag_data_ready_get(const stmdev_ctx_t *ctx,
                                       uint8_t *val)
{
  lsm6dsr_status_reg_t status_reg;
  int32_t ret;

  ret = lsm6dsr_read_reg(ctx, LSM6DSR_STATUS_REG,
                         (uint8_t *)&status_reg, 1);
  *val = status_reg.gda;

  return ret;
}

/**
  * @brief  Temperature new data available.[get]
  *
  * @param  ctx    Read / write interface definitions.(ptr)
  * @param  val    Change the values of tda in reg STATUS_REG
  * @retval        Interface status (MANDATORY: return 0 -> no Error).
  *
  */
int32_t lsm6dsr_temp_flag_data_ready_get(const stmdev_ctx_t *ctx,
                                         uint8_t *val)
{
  lsm6dsr_status_reg_t status_reg;
  int32_t ret;

  ret = lsm6dsr_read_reg(ctx, LSM6DSR_STATUS_REG,
                         (uint8_t *)&status_reg, 1);
  *val = status_reg.tda;

  return ret;
}

/**
  * @brief  Accelerometer X-axis user offset correction expressed in two's
  *         complement, weight depends on USR_OFF_W in CTRL6_C (15h).
  *         The value must be in the range [-127 127].[set]
  *
  * @param  ctx    Read / write interface definitions.(ptr)
  * @param  buff   Buffer that contains data to write
  * @retval        Interface status (MANDATORY: return 0 -> no Error).
  *
  */
int32_t lsm6dsr_xl_usr_offset_x_set(const stmdev_ctx_t *ctx,
                                    uint8_t *buff)
{
  int32_t ret;

  ret = lsm6dsr_write_reg(ctx, LSM6DSR_X_OFS_USR, buff, 1);

  return ret;
}

/**
  * @brief  Accelerometer X-axis user offset correction expressed in two's
  *         complement, weight depends on USR_OFF_W in CTRL6_C (15h).
  *         The value must be in the range [-127 127].[get]
  *
  * @param  ctx    Read / write interface definitions.(ptr)
  * @param  buff   Buffer that stores data read
  * @retval        Interface status (MANDATORY: return 0 -> no Error).
  *
  */
int32_t lsm6dsr_xl_usr_offset_x_get(const stmdev_ctx_t *ctx,
                                    uint8_t *buff)
{
  int32_t ret;

  ret = lsm6dsr_read_reg(ctx, LSM6DSR_X_OFS_USR, buff, 1);

  return ret;
}

/**
  * @brief  Accelerometer Y-axis user offset correction expressed in two's
  *         complement, weight depends on USR_OFF_W in CTRL6_C (15h).
  *         The value must be in the range [-127 127].[set]
  *
  * @param  ctx    Read / write interface definitions.(ptr)
  * @param  buff   Buffer that contains data to write
  * @retval        Interface status (MANDATORY: return 0 -> no Error).
  *
  */
int32_t lsm6dsr_xl_usr_offset_y_set(const stmdev_ctx_t *ctx,
                                    uint8_t *buff)
{
  int32_t ret;

  ret = lsm6dsr_write_reg(ctx, LSM6DSR_Y_OFS_USR, buff, 1);

  return ret;
}

/**
  * @brief  Accelerometer Y-axis user offset correction expressed in two's
  *         complement, weight depends on USR_OFF_W in CTRL6_C (15h).
  *         The value must be in the range [-127 127].[get]
  *
  * @param  ctx    Read / write interface definitions.(ptr)
  * @param  buff   Buffer that stores data read
  * @retval        Interface status (MANDATORY: return 0 -> no Error).
  *
  */
int32_t lsm6dsr_xl_usr_offset_y_get(const stmdev_ctx_t *ctx,
                                    uint8_t *buff)
{
  int32_t ret;

  ret = lsm6dsr_read_reg(ctx, LSM6DSR_Y_OFS_USR, buff, 1);

  return ret;
}

/**
  * @brief  Accelerometer Z-axis user offset correction expressed in two's
  *         complement, weight depends on USR_OFF_W in CTRL6_C (15h).
  *         The value must be in the range [-127 127].[set]
  *
  * @param  ctx    Read / write interface definitions.(ptr)
  * @param  buff   Buffer that contains data to write
  * @retval        Interface status (MANDATORY: return 0 -> no Error).
  *
  */
int32_t lsm6dsr_xl_usr_offset_z_set(const stmdev_ctx_t *ctx,
                                    uint8_t *buff)
{
  int32_t ret;

  ret = lsm6dsr_write_reg(ctx, LSM6DSR_Z_OFS_USR, buff, 1);

  return ret;
}

/**
  * @brief  Accelerometer X-axis user offset correction expressed in two's
  *         complement, weight depends on USR_OFF_W in CTRL6_C (15h).
  *         The value must be in the range [-127 127].[get]
  *
  * @param  ctx    Read / write interface definitions.(ptr)
  * @param  buff   Buffer that stores data read
  * @retval        Interface status (MANDATORY: return 0 -> no Error).
  *
  */
int32_t lsm6dsr_xl_usr_offset_z_get(const stmdev_ctx_t *ctx,
                                    uint8_t *buff)
{
  int32_t ret;

  ret = lsm6dsr_read_reg(ctx, LSM6DSR_Z_OFS_USR, buff, 1);

  return ret;
}

/**
  * @brief  Enables user offset on out.[set]
  *
  * @param  ctx    Read / write interface definitions.(ptr)
  * @param  val    Change the values of usr_off_on_out in reg CTRL7_G
  * @retval        Interface status (MANDATORY: return 0 -> no Error).
  *
  */
int32_t lsm6dsr_xl_usr_offset_set(const stmdev_ctx_t *ctx, uint8_t val)
{
  lsm6dsr_ctrl7_g_t ctrl7_g;
  int32_t ret;

  ret = lsm6dsr_read_reg(ctx, LSM6DSR_CTRL7_G,
                         (uint8_t *)&ctrl7_g, 1);

  if (ret == 0)
  {
    ctrl7_g.usr_off_on_out = (uint8_t)val;
    ret = lsm6dsr_write_reg(ctx, LSM6DSR_CTRL7_G,
                            (uint8_t *)&ctrl7_g, 1);
  }

  return ret;
}

/**
  * @brief  Get user offset on out flag.[get]
  *
  * @param  ctx    Read / write interface definitions.(ptr)
  * @param  val    Get values of usr_off_on_out in reg CTRL7_G
  * @retval        Interface status (MANDATORY: return 0 -> no Error).
  *
  */
int32_t lsm6dsr_xl_usr_offset_get(const stmdev_ctx_t *ctx, uint8_t *val)
{
  lsm6dsr_ctrl7_g_t ctrl7_g;
  int32_t ret;

  ret = lsm6dsr_read_reg(ctx, LSM6DSR_CTRL7_G,
                         (uint8_t *)&ctrl7_g, 1);
  *val = ctrl7_g.usr_off_on_out;

  return ret;
}

/**
  * @}
  *
  */

/**
  * @defgroup   LSM6DSR_Timestamp
  * @brief      This section groups all the functions that manage the
  *             timestamp generation.
  * @{
  *
  */

/**
  * @brief  Reset timestamp counter.[set]
  *
  * @param  ctx    Read / write interface definitions.(ptr)
  * @retval        Interface status (MANDATORY: return 0 -> no Error).
  *
  */
int32_t lsm6dsr_timestamp_rst(const stmdev_ctx_t *ctx)
{
  uint8_t rst_val = 0xAA;
  return lsm6dsr_write_reg(ctx, LSM6DSR_TIMESTAMP2, &rst_val, 1);
}

/**
  * @brief  Enables timestamp counter.[set]
  *
  * @param  ctx    Read / write interface definitions.(ptr)
  * @param  val    Change the values of timestamp_en in reg CTRL10_C
  * @retval        Interface status (MANDATORY: return 0 -> no Error).
  *
  */
int32_t lsm6dsr_timestamp_set(const stmdev_ctx_t *ctx, uint8_t val)
{
  lsm6dsr_ctrl10_c_t ctrl10_c;
  int32_t ret;

  ret = lsm6dsr_read_reg(ctx, LSM6DSR_CTRL10_C,
                         (uint8_t *)&ctrl10_c, 1);

  if (ret == 0)
  {
    ctrl10_c.timestamp_en = (uint8_t)val;
    ret = lsm6dsr_write_reg(ctx, LSM6DSR_CTRL10_C,
                            (uint8_t *)&ctrl10_c, 1);
  }

  return ret;
}

/**
  * @brief  Enables timestamp counter.[get]
  *
  * @param  ctx    Read / write interface definitions.(ptr)
  * @param  val    Change the values of timestamp_en in reg CTRL10_C
  * @retval        Interface status (MANDATORY: return 0 -> no Error).
  *
  */
int32_t lsm6dsr_timestamp_get(const stmdev_ctx_t *ctx, uint8_t *val)
{
  lsm6dsr_ctrl10_c_t ctrl10_c;
  int32_t ret;

  ret = lsm6dsr_read_reg(ctx, LSM6DSR_CTRL10_C,
                         (uint8_t *)&ctrl10_c, 1);
  *val = ctrl10_c.timestamp_en;

  return ret;
}

/**
  * @brief  Timestamp first data output register (r).
  *         The value is expressed as a 32-bit word and the bit resolution
  *         is 25 us.[get]
  *
  * @param  ctx    Read / write interface definitions.(ptr)
  * @param  buff   Buffer that stores data read
  * @retval        Interface status (MANDATORY: return 0 -> no Error).
  *
  */
int32_t lsm6dsr_timestamp_raw_get(const stmdev_ctx_t *ctx, uint32_t *val)
{
  uint8_t buff[4];
  int32_t ret;

  ret = lsm6dsr_read_reg(ctx, LSM6DSR_TIMESTAMP0, buff, 4);
  *val = buff[3];
  *val = (*val * 256U) +  buff[2];
  *val = (*val * 256U) +  buff[1];
  *val = (*val * 256U) +  buff[0];

  return ret;
}

/**
  * @}
  *
  */

/**
  * @defgroup   LSM6DSR_Data output
  * @brief      This section groups all the data output functions.
  * @{
  *
  */

/**
  * @brief  Circular burst-mode (rounding) read of the output registers.[set]
  *
  * @param  ctx    Read / write interface definitions.(ptr)
  * @param  val    Change the values of rounding in reg CTRL5_C
  * @retval        Interface status (MANDATORY: return 0 -> no Error).
  *
  */
int32_t lsm6dsr_rounding_mode_set(const stmdev_ctx_t *ctx,
                                  lsm6dsr_rounding_t val)
{
  lsm6dsr_ctrl5_c_t ctrl5_c;
  int32_t ret;

  ret = lsm6dsr_read_reg(ctx, LSM6DSR_CTRL5_C,
                         (uint8_t *)&ctrl5_c, 1);

  if (ret == 0)
  {
    ctrl5_c.rounding = (uint8_t)val;
    ret = lsm6dsr_write_reg(ctx, LSM6DSR_CTRL5_C,
                            (uint8_t *)&ctrl5_c, 1);
  }

  return ret;
}

/**
  * @brief  Gyroscope UI chain full-scale selection.[get]
  *
  * @param  ctx    Read / write interface definitions.(ptr)
  * @param  val    Get the values of rounding in reg CTRL5_C
  * @retval        Interface status (MANDATORY: return 0 -> no Error).
  *
  */
int32_t lsm6dsr_rounding_mode_get(const stmdev_ctx_t *ctx,
                                  lsm6dsr_rounding_t *val)
{
  lsm6dsr_ctrl5_c_t ctrl5_c;
  int32_t ret;

  ret = lsm6dsr_read_reg(ctx, LSM6DSR_CTRL5_C,
                         (uint8_t *)&ctrl5_c, 1);

  switch (ctrl5_c.rounding)
  {
    case LSM6DSR_NO_ROUND:
      *val = LSM6DSR_NO_ROUND;
      break;

    case LSM6DSR_ROUND_XL:
      *val = LSM6DSR_ROUND_XL;
      break;

    case LSM6DSR_ROUND_GY:
      *val = LSM6DSR_ROUND_GY;
      break;

    case LSM6DSR_ROUND_GY_XL:
      *val = LSM6DSR_ROUND_GY_XL;
      break;

    default:
      *val = LSM6DSR_NO_ROUND;
      break;
  }

  return ret;
}

/**
  * @brief  Temperature data output register (r).
  *         L and H registers together express a 16-bit word in two's
  *         complement.[get]
  *
  * @param  ctx    Read / write interface definitions.(ptr)
  * @param  buff   Buffer that stores data read
  * @retval        Interface status (MANDATORY: return 0 -> no Error).
  *
  */
int32_t lsm6dsr_temperature_raw_get(const stmdev_ctx_t *ctx,
                                    int16_t *val)
{
  uint8_t buff[2];
  int32_t ret;

  ret = lsm6dsr_read_reg(ctx, LSM6DSR_OUT_TEMP_L, buff, 2);
  *val = (int16_t)buff[1];
  *val = (*val * 256) + (int16_t)buff[0];

  return ret;
}

/**
  * @brief  Angular rate sensor. The value is expressed as a 16-bit
  *         word in two's complement.[get]
  *
  * @param  ctx    Read / write interface definitions.(ptr)
  * @param  buff   Buffer that stores data read
  * @retval        Interface status (MANDATORY: return 0 -> no Error).
  *
  */
int32_t lsm6dsr_angular_rate_raw_get(const stmdev_ctx_t *ctx,
                                     int16_t *val)
{
  uint8_t buff[6];
  int32_t ret;

  ret = lsm6dsr_read_reg(ctx, LSM6DSR_OUTX_L_G, buff, 6);
  val[0] = (int16_t)buff[1];
  val[0] = (val[0] * 256) + (int16_t)buff[0];
  val[1] = (int16_t)buff[3];
  val[1] = (val[1] * 256) + (int16_t)buff[2];
  val[2] = (int16_t)buff[5];
  val[2] = (val[2] * 256) + (int16_t)buff[4];

  return ret;
}

/**
  * @brief  Linear acceleration output register. The value is expressed as a
  *         16-bit word in two's complement.[get]
  *
  * @param  ctx    Read / write interface definitions.(ptr)
  * @param  buff   Buffer that stores data read
  * @retval        Interface status (MANDATORY: return 0 -> no Error).
  *
  */
int32_t lsm6dsr_acceleration_raw_get(const stmdev_ctx_t *ctx,
                                     int16_t *val)
{
  uint8_t buff[6];
  int32_t ret;

  ret = lsm6dsr_read_reg(ctx, LSM6DSR_OUTX_L_A, buff, 6);
  val[0] = (int16_t)buff[1];
  val[0] = (val[0] * 256) + (int16_t)buff[0];
  val[1] = (int16_t)buff[3];
  val[1] = (val[1] * 256) + (int16_t)buff[2];
  val[2] = (int16_t)buff[5];
  val[2] = (val[2] * 256) + (int16_t)buff[4];

  return ret;
}

/**
  * @brief  FIFO data output.[get]
  *
  * @param  ctx    Read / write interface definitions.(ptr)
  * @param  buff   Buffer that stores data read
  * @retval        Interface status (MANDATORY: return 0 -> no Error).
  *
  */
int32_t lsm6dsr_fifo_out_raw_get(const stmdev_ctx_t *ctx, uint8_t *buff)
{
  int32_t ret;

  ret = lsm6dsr_read_reg(ctx, LSM6DSR_FIFO_DATA_OUT_X_L, buff, 6);

  return ret;
}

/**
  * @brief  Step counter output register.[get]
  *
  * @param  ctx    Read / write interface definitions.(ptr)
  * @param  buff   Buffer that stores data read
  * @retval        Interface status (MANDATORY: return 0 -> no Error).
  *
  */
int32_t lsm6dsr_number_of_steps_get(const stmdev_ctx_t *ctx,
                                    uint16_t *val)
{
  uint8_t buff[2];
  int32_t ret;

  ret = lsm6dsr_mem_bank_set(ctx, LSM6DSR_EMBEDDED_FUNC_BANK);

  if (ret == 0)
  {
    ret = lsm6dsr_read_reg(ctx, LSM6DSR_STEP_COUNTER_L, buff, 2);
    *val = buff[1];
    *val = (*val * 256U) +  buff[0];
  }

  if (ret == 0)
  {
    ret = lsm6dsr_mem_bank_set(ctx, LSM6DSR_USER_BANK);
  }

  return ret;
}

/**
  * @brief  Reset step counter register.[get]
  *
  * @param  ctx    Read / write interface definitions.(ptr)
  * @retval        Interface status (MANDATORY: return 0 -> no Error).
  *
  */
int32_t lsm6dsr_steps_reset(const stmdev_ctx_t *ctx)
{
  lsm6dsr_emb_func_src_t emb_func_src;
  int32_t ret;

  ret = lsm6dsr_mem_bank_set(ctx, LSM6DSR_EMBEDDED_FUNC_BANK);

  if (ret == 0)
  {
    ret = lsm6dsr_read_reg(ctx, LSM6DSR_EMB_FUNC_SRC,
                           (uint8_t *)&emb_func_src, 1);
  }

  if (ret == 0)
  {
    emb_func_src.pedo_rst_step = PROPERTY_ENABLE;
    ret = lsm6dsr_write_reg(ctx, LSM6DSR_EMB_FUNC_SRC,
                            (uint8_t *)&emb_func_src, 1);
  }

  if (ret == 0)
  {
    ret = lsm6dsr_mem_bank_set(ctx, LSM6DSR_USER_BANK);
  }

  return ret;
}

/**
  * @}
  *
  */

/**
  * @defgroup   LSM6DSR_common
  * @brief      This section groups common useful functions.
  * @{
  *
  */

/**
  * @brief  Difference in percentage of the effective ODR (and timestamp rate)
  *         with respect to the typical.[get]
  *         Step:  0.15%. 8-bit format, 2's complement.
  *
  * @param  ctx    Read / write interface definitions.(ptr)
  * @param  val    Change the values of freq_fine in reg INTERNAL_FREQ_FINE
  * @retval        Interface status (MANDATORY: return 0 -> no Error).
  *
  */
int32_t lsm6dsr_odr_cal_reg_get(const stmdev_ctx_t *ctx, int8_t *val)
{
  lsm6dsr_internal_freq_fine_t internal_freq_fine;
  int32_t ret;

  ret = lsm6dsr_read_reg(ctx, LSM6DSR_INTERNAL_FREQ_FINE,
                         (uint8_t *)&internal_freq_fine, 1);
  *val = (int8_t)internal_freq_fine.freq_fine;

  return ret;
}

/**
  * @brief  Enable access to the embedded functions/sensor hub configuration
  *         registers.[set]
  *
  * @param  ctx    Read / write interface definitions.(ptr)
  * @param  val    Change the values of reg_access in reg FUNC_CFG_ACCESS
  * @retval        Interface status (MANDATORY: return 0 -> no Error).
  *
  */
int32_t lsm6dsr_mem_bank_set(const stmdev_ctx_t *ctx,
                             lsm6dsr_reg_access_t val)
{
  lsm6dsr_func_cfg_access_t func_cfg_access;
  int32_t ret;

  ret = lsm6dsr_read_reg(ctx, LSM6DSR_FUNC_CFG_ACCESS,
                         (uint8_t *)&func_cfg_access, 1);

  if (ret == 0)
  {
    func_cfg_access.reg_access = (uint8_t)val;
    ret = lsm6dsr_write_reg(ctx, LSM6DSR_FUNC_CFG_ACCESS,
                            (uint8_t *)&func_cfg_access, 1);
  }

  return ret;
}

/**
  * @brief  Enable access to the embedded functions/sensor hub configuration
  *         registers.[get]
  *
  * @param  ctx    Read / write interface definitions.(ptr)
  * @param  val    Get the values of reg_access in reg FUNC_CFG_ACCESS
  * @retval        Interface status (MANDATORY: return 0 -> no Error).
  *
  */
int32_t lsm6dsr_mem_bank_get(const stmdev_ctx_t *ctx,
                             lsm6dsr_reg_access_t *val)
{
  lsm6dsr_func_cfg_access_t func_cfg_access;
  int32_t ret;

  ret = lsm6dsr_read_reg(ctx, LSM6DSR_FUNC_CFG_ACCESS,
                         (uint8_t *)&func_cfg_access, 1);

  switch (func_cfg_access.reg_access)
  {
    case LSM6DSR_USER_BANK:
      *val = LSM6DSR_USER_BANK;
      break;

    case LSM6DSR_SENSOR_HUB_BANK:
      *val = LSM6DSR_SENSOR_HUB_BANK;
      break;

    case LSM6DSR_EMBEDDED_FUNC_BANK:
      *val = LSM6DSR_EMBEDDED_FUNC_BANK;
      break;

    default:
      *val = LSM6DSR_USER_BANK;
      break;
  }

  return ret;
}

/**
  * @brief  Write a line(byte) in a page.[set]
  *
  * @param  ctx    Read / write interface definitions.(ptr)
  * @param  add    Page line address
  * @param  val    Value to write
  * @retval        Interface status (MANDATORY: return 0 -> no Error).
  *
  */
int32_t lsm6dsr_ln_pg_write_byte(const stmdev_ctx_t *ctx, uint16_t add,
                                 uint8_t *val)
{
  lsm6dsr_page_rw_t page_rw;
  lsm6dsr_page_sel_t page_sel;
  lsm6dsr_page_address_t page_address;
  int32_t ret;

  ret = lsm6dsr_mem_bank_set(ctx, LSM6DSR_EMBEDDED_FUNC_BANK);

  if (ret == 0)
  {
    ret = lsm6dsr_read_reg(ctx, LSM6DSR_PAGE_RW,
                           (uint8_t *)&page_rw, 1);
  }

  if (ret == 0)
  {
    page_rw.page_rw = 0x02U; /* page_write enable */
    ret = lsm6dsr_write_reg(ctx, LSM6DSR_PAGE_RW,
                            (uint8_t *)&page_rw, 1);
  }

  if (ret == 0)
  {
    ret = lsm6dsr_read_reg(ctx, LSM6DSR_PAGE_SEL,
                           (uint8_t *)&page_sel, 1);
  }

  if (ret == 0)
  {
    page_sel.page_sel = (uint8_t)((add / 256U) & 0x0FU);
    page_sel.not_used_01 = 1;
    ret = lsm6dsr_write_reg(ctx, LSM6DSR_PAGE_SEL,
                            (uint8_t *)&page_sel, 1);
  }

  if (ret == 0)
  {
    page_address.page_addr = (uint8_t)(add - (page_sel.page_sel * 256U));
    ret = lsm6dsr_write_reg(ctx, LSM6DSR_PAGE_ADDRESS,
                            (uint8_t *)&page_address, 1);
  }

  if (ret == 0)
  {
    ret = lsm6dsr_write_reg(ctx, LSM6DSR_PAGE_VALUE, val, 1);
  }

  if (ret == 0)
  {
    ret = lsm6dsr_read_reg(ctx, LSM6DSR_PAGE_RW,
                           (uint8_t *)&page_rw, 1);
  }

  if (ret == 0)
  {
    page_rw.page_rw = 0x00; /* page_write disable */
    ret = lsm6dsr_write_reg(ctx, LSM6DSR_PAGE_RW,
                            (uint8_t *)&page_rw, 1);
  }

  if (ret == 0)
  {
    ret = lsm6dsr_mem_bank_set(ctx, LSM6DSR_USER_BANK);
  }

  return ret;
}

/**
  * @brief  Write buffer in a page.[set]
  *
  * @param  ctx    Read / write interface definitions.(ptr)
  * @param  buf    Page line address.(ptr)
  * @param  val    Value to write.
  * @param  len    buffer length.
  * @retval        Interface status (MANDATORY: return 0 -> no Error).
  *
  */
int32_t lsm6dsr_ln_pg_write(const stmdev_ctx_t *ctx, uint16_t add,
                            uint8_t *buf, uint8_t len)
{
  lsm6dsr_page_rw_t page_rw;
  lsm6dsr_page_sel_t page_sel;
  lsm6dsr_page_address_t page_address;
  uint8_t msb;
  uint8_t lsb;
  int32_t ret;
  uint8_t i ;

  msb = (uint8_t)((add / 256U) & 0x0FU);
  lsb = (uint8_t)(add - (msb * 256U));
  ret = lsm6dsr_mem_bank_set(ctx, LSM6DSR_EMBEDDED_FUNC_BANK);

  if (ret == 0)
  {
    ret = lsm6dsr_read_reg(ctx, LSM6DSR_PAGE_RW,
                           (uint8_t *)&page_rw, 1);
  }

  if (ret == 0)
  {
    page_rw.page_rw = 0x02U; /* page_write enable*/
    ret = lsm6dsr_write_reg(ctx, LSM6DSR_PAGE_RW,
                            (uint8_t *)&page_rw, 1);
  }

  if (ret == 0)
  {
    ret = lsm6dsr_read_reg(ctx, LSM6DSR_PAGE_SEL,
                           (uint8_t *)&page_sel, 1);
  }

  if (ret == 0)
  {
    page_sel.page_sel = msb;
    page_sel.not_used_01 = 1;
    ret = lsm6dsr_write_reg(ctx, LSM6DSR_PAGE_SEL,
                            (uint8_t *)&page_sel, 1);
  }

  if (ret == 0)
  {
    page_address.page_addr = lsb;
    ret = lsm6dsr_write_reg(ctx, LSM6DSR_PAGE_ADDRESS,
                            (uint8_t *)&page_address, 1);
  }

  for (i = 0; i < len; i++)
  {
    if (ret == 0)
    {
      ret = lsm6dsr_write_reg(ctx, LSM6DSR_PAGE_VALUE, &buf[i], 1);

      if (ret == 0)
      {
        /* Check if page wrap */
        if (lsb == 0x00U)
        {
          msb++;
          ret = lsm6dsr_read_reg(ctx, LSM6DSR_PAGE_SEL,
                                 (uint8_t *)&page_sel, 1);
        }

        lsb++;
      }

      if (ret == 0)
      {
        page_sel.page_sel = msb;
        page_sel.not_used_01 = 1;
        ret = lsm6dsr_write_reg(ctx, LSM6DSR_PAGE_SEL,
                                (uint8_t *)&page_sel, 1);
      }
    }
  }

  if (ret == 0)
  {
    page_sel.page_sel = 0;
    page_sel.not_used_01 = 1;
    ret = lsm6dsr_write_reg(ctx, LSM6DSR_PAGE_SEL,
                            (uint8_t *)&page_sel, 1);
  }

  if (ret == 0)
  {
    ret = lsm6dsr_read_reg(ctx, LSM6DSR_PAGE_RW,
                           (uint8_t *)&page_rw, 1);
  }

  if (ret == 0)
  {
    page_rw.page_rw = 0x00U; /* page_write disable */
    ret = lsm6dsr_write_reg(ctx, LSM6DSR_PAGE_RW,
                            (uint8_t *)&page_rw, 1);
  }

  if (ret == 0)
  {
    ret = lsm6dsr_mem_bank_set(ctx, LSM6DSR_USER_BANK);
  }

  return ret;
}

/**
  * @brief  Read a line(byte) in a page.[get]
  *
  * @param  ctx    Read / write interface definitions.(ptr)
  * @param  add    Page line address.
  * @param  val    Read value.(ptr)
  * @retval        Interface status (MANDATORY: return 0 -> no Error).
  *
  */
int32_t lsm6dsr_ln_pg_read_byte(const stmdev_ctx_t *ctx, uint16_t add,
                                uint8_t *val)
{
  lsm6dsr_page_rw_t page_rw;
  lsm6dsr_page_sel_t page_sel;
  lsm6dsr_page_address_t page_address;
  int32_t ret;

  ret = lsm6dsr_mem_bank_set(ctx, LSM6DSR_EMBEDDED_FUNC_BANK);

  if (ret == 0)
  {
    ret = lsm6dsr_read_reg(ctx, LSM6DSR_PAGE_RW,
                           (uint8_t *)&page_rw, 1);
  }

  if (ret == 0)
  {
    page_rw.page_rw = 0x01U; /* page_read enable*/
    ret = lsm6dsr_write_reg(ctx, LSM6DSR_PAGE_RW,
                            (uint8_t *)&page_rw, 1);
  }

  if (ret == 0)
  {
    ret = lsm6dsr_read_reg(ctx, LSM6DSR_PAGE_SEL,
                           (uint8_t *)&page_sel, 1);
  }

  if (ret == 0)
  {
    page_sel.page_sel = (uint8_t)((add / 256U) & 0x0FU);
    page_sel.not_used_01 = 1;
    ret = lsm6dsr_write_reg(ctx, LSM6DSR_PAGE_SEL,
                            (uint8_t *)&page_sel, 1);
  }

  if (ret == 0)
  {
    page_address.page_addr = (uint8_t)(add - (page_sel.page_sel * 256U));
    ret = lsm6dsr_write_reg(ctx, LSM6DSR_PAGE_ADDRESS,
                            (uint8_t *)&page_address, 1);
  }

  if (ret == 0)
  {
    ret = lsm6dsr_read_reg(ctx, LSM6DSR_PAGE_VALUE, val, 2);
  }

  if (ret == 0)
  {
    ret = lsm6dsr_read_reg(ctx, LSM6DSR_PAGE_RW,
                           (uint8_t *)&page_rw, 1);
  }

  if (ret == 0)
  {
    page_rw.page_rw = 0x00U; /* page_read disable */
    ret = lsm6dsr_write_reg(ctx, LSM6DSR_PAGE_RW,
                            (uint8_t *)&page_rw, 1);
  }

  if (ret == 0)
  {
    ret = lsm6dsr_mem_bank_set(ctx, LSM6DSR_USER_BANK);
  }

  return ret;
}

/**
  * @brief  Data-ready pulsed / letched mode.[set]
  *
  * @param  ctx    Read / write interface definitions.(ptr)
  * @param  val    Change the values of dataready_pulsed in
  *                reg COUNTER_BDR_REG1
  * @retval        Interface status (MANDATORY: return 0 -> no Error).
  *
  */
int32_t lsm6dsr_data_ready_mode_set(const stmdev_ctx_t *ctx,
                                    lsm6dsr_dataready_pulsed_t val)
{
  lsm6dsr_counter_bdr_reg1_t counter_bdr_reg1;
  int32_t ret;

  ret = lsm6dsr_read_reg(ctx, LSM6DSR_COUNTER_BDR_REG1,
                         (uint8_t *)&counter_bdr_reg1, 1);

  if (ret == 0)
  {
    counter_bdr_reg1.dataready_pulsed = (uint8_t)val;
    ret = lsm6dsr_write_reg(ctx, LSM6DSR_COUNTER_BDR_REG1,
                            (uint8_t *)&counter_bdr_reg1, 1);
  }

  return ret;
}

/**
  * @brief  Data-ready pulsed / letched mode.[get]
  *
  * @param  ctx    Read / write interface definitions.(ptr)
  * @param  val    Get the values of dataready_pulsed in
  *                reg COUNTER_BDR_REG1
  * @retval        Interface status (MANDATORY: return 0 -> no Error).
  *
  */
int32_t lsm6dsr_data_ready_mode_get(const stmdev_ctx_t *ctx,
                                    lsm6dsr_dataready_pulsed_t *val)
{
  lsm6dsr_counter_bdr_reg1_t counter_bdr_reg1;
  int32_t ret;

  ret = lsm6dsr_read_reg(ctx, LSM6DSR_COUNTER_BDR_REG1,
                         (uint8_t *)&counter_bdr_reg1, 1);

  switch (counter_bdr_reg1.dataready_pulsed)
  {
    case LSM6DSR_DRDY_LATCHED:
      *val = LSM6DSR_DRDY_LATCHED;
      break;

    case LSM6DSR_DRDY_PULSED:
      *val = LSM6DSR_DRDY_PULSED;
      break;

    default:
      *val = LSM6DSR_DRDY_LATCHED;
      break;
  }

  return ret;
}

/**
  * @brief  Device Who am I.[get]
  *
  * @param  ctx    Read / write interface definitions.(ptr)
  * @param  buff   Buffer that stores data read
  * @retval        Interface status (MANDATORY: return 0 -> no Error).
  *
  */
int32_t lsm6dsr_device_id_get(const stmdev_ctx_t *ctx, uint8_t *buff)
{
  int32_t ret;

  ret = lsm6dsr_read_reg(ctx, LSM6DSR_WHO_AM_I, buff, 1);

  return ret;
}

/**
  * @brief  Software reset. Restore the default values in user registers.[set]
  *
  * @param  ctx    Read / write interface definitions.(ptr)
  * @param  val    Change the values of sw_reset in reg CTRL3_C
  * @retval        Interface status (MANDATORY: return 0 -> no Error).
  *
  */
int32_t lsm6dsr_reset_set(const stmdev_ctx_t *ctx, uint8_t val)
{
  lsm6dsr_ctrl3_c_t ctrl3_c;
  int32_t ret;

  ret = lsm6dsr_read_reg(ctx, LSM6DSR_CTRL3_C,
                         (uint8_t *)&ctrl3_c, 1);

  if (ret == 0)
  {
    ctrl3_c.sw_reset = (uint8_t)val;
    ret = lsm6dsr_write_reg(ctx, LSM6DSR_CTRL3_C,
                            (uint8_t *)&ctrl3_c, 1);
  }

  return ret;
}

/**
  * @brief  Software reset. Restore the default values in user registers.[get]
  *
  * @param  ctx    Read / write interface definitions.(ptr)
  * @param  val    Change the values of sw_reset in reg CTRL3_C
  * @retval        Interface status (MANDATORY: return 0 -> no Error).
  *
  */
int32_t lsm6dsr_reset_get(const stmdev_ctx_t *ctx, uint8_t *val)
{
  lsm6dsr_ctrl3_c_t ctrl3_c;
  int32_t ret;

  ret = lsm6dsr_read_reg(ctx, LSM6DSR_CTRL3_C,
                         (uint8_t *)&ctrl3_c, 1);
  *val = ctrl3_c.sw_reset;

  return ret;
}

/**
  * @brief  Register address automatically incremented during a multiple byte
  *         access with a serial interface.[set]
  *
  * @param  ctx    Read / write interface definitions.(ptr)
  * @param  val    Change the values of if_inc in reg CTRL3_C
  * @retval        Interface status (MANDATORY: return 0 -> no Error).
  *
  */
int32_t lsm6dsr_auto_increment_set(const stmdev_ctx_t *ctx, uint8_t val)
{
  lsm6dsr_ctrl3_c_t ctrl3_c;
  int32_t ret;

  ret = lsm6dsr_read_reg(ctx, LSM6DSR_CTRL3_C,
                         (uint8_t *)&ctrl3_c, 1);

  if (ret == 0)
  {
    ctrl3_c.if_inc = (uint8_t)val;
    ret = lsm6dsr_write_reg(ctx, LSM6DSR_CTRL3_C,
                            (uint8_t *)&ctrl3_c, 1);
  }

  return ret;
}

/**
  * @brief  Register address automatically incremented during a multiple byte
  *         access with a serial interface.[get]
  *
  * @param  ctx    Read / write interface definitions.(ptr)
  * @param  val    Change the values of if_inc in reg CTRL3_C
  * @retval        Interface status (MANDATORY: return 0 -> no Error).
  *
  */
int32_t lsm6dsr_auto_increment_get(const stmdev_ctx_t *ctx, uint8_t *val)
{
  lsm6dsr_ctrl3_c_t ctrl3_c;
  int32_t ret;

  ret = lsm6dsr_read_reg(ctx, LSM6DSR_CTRL3_C,
                         (uint8_t *)&ctrl3_c, 1);
  *val = ctrl3_c.if_inc;

  return ret;
}

/**
  * @brief  Reboot memory content. Reload the calibration parameters.[set]
  *
  * @param  ctx    Read / write interface definitions.(ptr)
  * @param  val    Change the values of boot in reg CTRL3_C
  * @retval        Interface status (MANDATORY: return 0 -> no Error).
  *
  */
int32_t lsm6dsr_boot_set(const stmdev_ctx_t *ctx, uint8_t val)
{
  lsm6dsr_ctrl3_c_t ctrl3_c;
  int32_t ret;

  ret = lsm6dsr_read_reg(ctx, LSM6DSR_CTRL3_C,
                         (uint8_t *)&ctrl3_c, 1);

  if (ret == 0)
  {
    ctrl3_c.boot = (uint8_t)val;
    ret = lsm6dsr_write_reg(ctx, LSM6DSR_CTRL3_C,
                            (uint8_t *)&ctrl3_c, 1);
  }

  return ret;
}

/**
  * @brief  Reboot memory content. Reload the calibration parameters.[get]
  *
  * @param  ctx    Read / write interface definitions.(ptr)
  * @param  val    Change the values of boot in reg CTRL3_C
  * @retval        Interface status (MANDATORY: return 0 -> no Error).
  *
  */
int32_t lsm6dsr_boot_get(const stmdev_ctx_t *ctx, uint8_t *val)
{
  lsm6dsr_ctrl3_c_t ctrl3_c;
  int32_t ret;

  ret = lsm6dsr_read_reg(ctx, LSM6DSR_CTRL3_C,
                         (uint8_t *)&ctrl3_c, 1);
  *val = ctrl3_c.boot;

  return ret;
}



/**
  * @brief  Linear acceleration sensor self-test enable.[set]
  *
  * @param  ctx    Read / write interface definitions.(ptr)
  * @param  val    Change the values of st_xl in reg CTRL5_C
  * @retval        Interface status (MANDATORY: return 0 -> no Error).
  *
  */
int32_t lsm6dsr_xl_self_test_set(const stmdev_ctx_t *ctx,
                                 lsm6dsr_st_xl_t val)
{
  lsm6dsr_ctrl5_c_t ctrl5_c;
  int32_t ret;

  ret = lsm6dsr_read_reg(ctx, LSM6DSR_CTRL5_C,
                         (uint8_t *)&ctrl5_c, 1);

  if (ret == 0)
  {
    ctrl5_c.st_xl = (uint8_t)val;
    ret = lsm6dsr_write_reg(ctx, LSM6DSR_CTRL5_C,
                            (uint8_t *)&ctrl5_c, 1);
  }

  return ret;
}

/**
  * @brief  Linear acceleration sensor self-test enable.[get]
  *
  * @param  ctx    Read / write interface definitions.(ptr)
  * @param  val    Get the values of st_xl in reg CTRL5_C
  * @retval        Interface status (MANDATORY: return 0 -> no Error).
  *
  */
int32_t lsm6dsr_xl_self_test_get(const stmdev_ctx_t *ctx,
                                 lsm6dsr_st_xl_t *val)
{
  lsm6dsr_ctrl5_c_t ctrl5_c;
  int32_t ret;

  ret = lsm6dsr_read_reg(ctx, LSM6DSR_CTRL5_C,
                         (uint8_t *)&ctrl5_c, 1);

  switch (ctrl5_c.st_xl)
  {
    case LSM6DSR_XL_ST_DISABLE:
      *val = LSM6DSR_XL_ST_DISABLE;
      break;

    case LSM6DSR_XL_ST_POSITIVE:
      *val = LSM6DSR_XL_ST_POSITIVE;
      break;

    case LSM6DSR_XL_ST_NEGATIVE:
      *val = LSM6DSR_XL_ST_NEGATIVE;
      break;

    default:
      *val = LSM6DSR_XL_ST_DISABLE;
      break;
  }

  return ret;
}

/**
  * @brief  Angular rate sensor self-test enable.[set]
  *
  * @param  ctx    Read / write interface definitions.(ptr)
  * @param  val    Change the values of st_g in reg CTRL5_C
  * @retval        Interface status (MANDATORY: return 0 -> no Error).
  *
  */
int32_t lsm6dsr_gy_self_test_set(const stmdev_ctx_t *ctx,
                                 lsm6dsr_st_g_t val)
{
  lsm6dsr_ctrl5_c_t ctrl5_c;
  int32_t ret;

  ret = lsm6dsr_read_reg(ctx, LSM6DSR_CTRL5_C,
                         (uint8_t *)&ctrl5_c, 1);

  if (ret == 0)
  {
    ctrl5_c.st_g = (uint8_t)val;
    ret = lsm6dsr_write_reg(ctx, LSM6DSR_CTRL5_C,
                            (uint8_t *)&ctrl5_c, 1);
  }

  return ret;
}

/**
  * @brief  Angular rate sensor self-test enable.[get]
  *
  * @param  ctx    Read / write interface definitions.(ptr)
  * @param  val    Get the values of st_g in reg CTRL5_C
  * @retval        Interface status (MANDATORY: return 0 -> no Error).
  *
  */
int32_t lsm6dsr_gy_self_test_get(const stmdev_ctx_t *ctx,
                                 lsm6dsr_st_g_t *val)
{
  lsm6dsr_ctrl5_c_t ctrl5_c;
  int32_t ret;

  ret = lsm6dsr_read_reg(ctx, LSM6DSR_CTRL5_C,
                         (uint8_t *)&ctrl5_c, 1);

  switch (ctrl5_c.st_g)
  {
    case LSM6DSR_GY_ST_DISABLE:
      *val = LSM6DSR_GY_ST_DISABLE;
      break;

    case LSM6DSR_GY_ST_POSITIVE:
      *val = LSM6DSR_GY_ST_POSITIVE;
      break;

    case LSM6DSR_GY_ST_NEGATIVE:
      *val = LSM6DSR_GY_ST_NEGATIVE;
      break;

    default:
      *val = LSM6DSR_GY_ST_DISABLE;
      break;
  }

  return ret;
}

/**
  * @}
  *
  */

/**
  * @defgroup   LSM6DSR_filters
  * @brief      This section group all the functions concerning the
  *             filters configuration
  * @{
  *
  */

/**
  * @brief  Accelerometer output from LPF2 filtering stage selection.[set]
  *
  * @param  ctx    Read / write interface definitions.(ptr)
  * @param  val    Change the values of lpf2_xl_en in reg CTRL1_XL
  * @retval        Interface status (MANDATORY: return 0 -> no Error).
  *
  */
int32_t lsm6dsr_xl_filter_lp2_set(const stmdev_ctx_t *ctx, uint8_t val)
{
  lsm6dsr_ctrl1_xl_t ctrl1_xl;
  int32_t ret;

  ret = lsm6dsr_read_reg(ctx, LSM6DSR_CTRL1_XL,
                         (uint8_t *)&ctrl1_xl, 1);

  if (ret == 0)
  {
    ctrl1_xl.lpf2_xl_en = (uint8_t)val;
    ret = lsm6dsr_write_reg(ctx, LSM6DSR_CTRL1_XL,
                            (uint8_t *)&ctrl1_xl, 1);
  }

  return ret;
}

/**
  * @brief  Accelerometer output from LPF2 filtering stage selection.[get]
  *
  * @param  ctx    Read / write interface definitions.(ptr)
  * @param  val    Change the values of lpf2_xl_en in reg CTRL1_XL
  * @retval        Interface status (MANDATORY: return 0 -> no Error).
  *
  */
int32_t lsm6dsr_xl_filter_lp2_get(const stmdev_ctx_t *ctx, uint8_t *val)
{
  lsm6dsr_ctrl1_xl_t ctrl1_xl;
  int32_t ret;

  ret = lsm6dsr_read_reg(ctx, LSM6DSR_CTRL1_XL,
                         (uint8_t *)&ctrl1_xl, 1);
  *val = ctrl1_xl.lpf2_xl_en;

  return ret;
}

/**
  * @brief  Enables gyroscope digital LPF1 if auxiliary SPI is disabled;
  *         the bandwidth can be selected through FTYPE [2:0] in CTRL6_C.[set]
  *
  * @param  ctx    Read / write interface definitions.(ptr)
  * @param  val    Change the values of lpf1_sel_g in reg CTRL4_C
  * @retval        Interface status (MANDATORY: return 0 -> no Error).
  *
  */
int32_t lsm6dsr_gy_filter_lp1_set(const stmdev_ctx_t *ctx, uint8_t val)
{
  lsm6dsr_ctrl4_c_t ctrl4_c;
  int32_t ret;

  ret = lsm6dsr_read_reg(ctx, LSM6DSR_CTRL4_C,
                         (uint8_t *)&ctrl4_c, 1);

  if (ret == 0)
  {
    ctrl4_c.lpf1_sel_g = (uint8_t)val;
    ret = lsm6dsr_write_reg(ctx, LSM6DSR_CTRL4_C,
                            (uint8_t *)&ctrl4_c, 1);
  }

  return ret;
}

/**
  * @brief  Enables gyroscope digital LPF1 if auxiliary SPI is disabled;
  *         the bandwidth can be selected through FTYPE [2:0] in CTRL6_C.[get]
  *
  * @param  ctx    Read / write interface definitions.(ptr)
  * @param  val    Change the values of lpf1_sel_g in reg CTRL4_C
  * @retval        Interface status (MANDATORY: return 0 -> no Error).
  *
  */
int32_t lsm6dsr_gy_filter_lp1_get(const stmdev_ctx_t *ctx, uint8_t *val)
{
  lsm6dsr_ctrl4_c_t ctrl4_c;
  int32_t ret;

  ret = lsm6dsr_read_reg(ctx, LSM6DSR_CTRL4_C,
                         (uint8_t *)&ctrl4_c, 1);
  *val = ctrl4_c.lpf1_sel_g;

  return ret;
}

/**
  * @brief  Mask DRDY on pin (both XL & Gyro) until filter settling ends
  *         (XL and Gyro independently masked).[set]
  *
  * @param  ctx    Read / write interface definitions.(ptr)
  * @param  val    Change the values of drdy_mask in reg CTRL4_C
  * @retval        Interface status (MANDATORY: return 0 -> no Error).
  *
  */
int32_t lsm6dsr_drdy_mask_set(const stmdev_ctx_t *ctx, uint8_t val)
{
  lsm6dsr_ctrl4_c_t ctrl4_c;
  int32_t ret;

  ret = lsm6dsr_read_reg(ctx, LSM6DSR_CTRL4_C,
                         (uint8_t *)&ctrl4_c, 1);

  if (ret == 0)
  {
    ctrl4_c.drdy_mask = (uint8_t)val;
    ret = lsm6dsr_write_reg(ctx, LSM6DSR_CTRL4_C,
                            (uint8_t *)&ctrl4_c, 1);
  }

  return ret;
}

/**
  * @brief  Mask DRDY on pin (both XL & Gyro) until filter settling ends
  *         (XL and Gyro independently masked).[get]
  *
  * @param  ctx    Read / write interface definitions.(ptr)
  * @param  val    Change the values of drdy_mask in reg CTRL4_C
  * @retval        Interface status (MANDATORY: return 0 -> no Error).
  *
  */
int32_t lsm6dsr_drdy_mask_get(const stmdev_ctx_t *ctx, uint8_t *val)
{
  lsm6dsr_ctrl4_c_t ctrl4_c;
  int32_t ret;

  ret = lsm6dsr_read_reg(ctx, LSM6DSR_CTRL4_C,
                         (uint8_t *)&ctrl4_c, 1);
  *val = ctrl4_c.drdy_mask;

  return ret;
}

/**
  * @brief  Gyroscope low pass filter 1 bandwidth.[set]
  *
  * @param  ctx    Read / write interface definitions.(ptr)
  * @param  val    Change the values of ftype in reg CTRL6_C
  * @retval        Interface status (MANDATORY: return 0 -> no Error).
  *
  */
int32_t lsm6dsr_gy_lp1_bandwidth_set(const stmdev_ctx_t *ctx,
                                     lsm6dsr_ftype_t val)
{
  lsm6dsr_ctrl6_c_t ctrl6_c;
  int32_t ret;

  ret = lsm6dsr_read_reg(ctx, LSM6DSR_CTRL6_C,
                         (uint8_t *)&ctrl6_c, 1);

  if (ret == 0)
  {
    ctrl6_c.ftype = (uint8_t)val;
    ret = lsm6dsr_write_reg(ctx, LSM6DSR_CTRL6_C,
                            (uint8_t *)&ctrl6_c, 1);
  }

  return ret;
}

/**
  * @brief  Gyroscope low pass filter 1 bandwidth.[get]
  *
  * @param  ctx    Read / write interface definitions.(ptr)
  * @param  val    Get the values of ftype in reg CTRL6_C
  * @retval        Interface status (MANDATORY: return 0 -> no Error).
  *
  */
int32_t lsm6dsr_gy_lp1_bandwidth_get(const stmdev_ctx_t *ctx,
                                     lsm6dsr_ftype_t *val)
{
  lsm6dsr_ctrl6_c_t ctrl6_c;
  int32_t ret;

  ret = lsm6dsr_read_reg(ctx, LSM6DSR_CTRL6_C,
                         (uint8_t *)&ctrl6_c, 1);

  switch (ctrl6_c.ftype)
  {
    case LSM6DSR_ULTRA_LIGHT:
      *val = LSM6DSR_ULTRA_LIGHT;
      break;

    case LSM6DSR_VERY_LIGHT:
      *val = LSM6DSR_VERY_LIGHT;
      break;

    case LSM6DSR_LIGHT:
      *val = LSM6DSR_LIGHT;
      break;

    case LSM6DSR_MEDIUM:
      *val = LSM6DSR_MEDIUM;
      break;

    case LSM6DSR_STRONG:
      *val = LSM6DSR_STRONG;
      break;

    case LSM6DSR_VERY_STRONG:
      *val = LSM6DSR_VERY_STRONG;
      break;

    case LSM6DSR_AGGRESSIVE:
      *val = LSM6DSR_AGGRESSIVE;
      break;

    case LSM6DSR_XTREME:
      *val = LSM6DSR_XTREME;
      break;

    default:
      *val = LSM6DSR_ULTRA_LIGHT;
      break;
  }

  return ret;
}

/**
  * @brief  Low pass filter 2 on 6D function selection.[set]
  *
  * @param  ctx    Read / write interface definitions.(ptr)
  * @param  val    Change the values of low_pass_on_6d in reg CTRL8_XL
  * @retval        Interface status (MANDATORY: return 0 -> no Error).
  *
  */
int32_t lsm6dsr_xl_lp2_on_6d_set(const stmdev_ctx_t *ctx, uint8_t val)
{
  lsm6dsr_ctrl8_xl_t ctrl8_xl;
  int32_t ret;

  ret = lsm6dsr_read_reg(ctx, LSM6DSR_CTRL8_XL,
                         (uint8_t *)&ctrl8_xl, 1);

  if (ret == 0)
  {
    ctrl8_xl.low_pass_on_6d = (uint8_t)val;
    ret = lsm6dsr_write_reg(ctx, LSM6DSR_CTRL8_XL,
                            (uint8_t *)&ctrl8_xl, 1);
  }

  return ret;
}

/**
  * @brief  Low pass filter 2 on 6D function selection.[get]
  *
  * @param  ctx    Read / write interface definitions.(ptr)
  * @param  val    Change the values of low_pass_on_6d in reg CTRL8_XL
  * @retval        Interface status (MANDATORY: return 0 -> no Error).
  *
  */
int32_t lsm6dsr_xl_lp2_on_6d_get(const stmdev_ctx_t *ctx, uint8_t *val)
{
  lsm6dsr_ctrl8_xl_t ctrl8_xl;
  int32_t ret;

  ret = lsm6dsr_read_reg(ctx, LSM6DSR_CTRL8_XL,
                         (uint8_t *)&ctrl8_xl, 1);
  *val = ctrl8_xl.low_pass_on_6d;

  return ret;
}

/**
  * @brief  Accelerometer slope filter / high-pass filter selection
  *         on output.[set]
  *
  * @param  ctx    Read / write interface definitions.(ptr)
  * @param  val    Change the values of hp_slope_xl_en in reg CTRL8_XL
  * @retval        Interface status (MANDATORY: return 0 -> no Error).
  *
  */
int32_t lsm6dsr_xl_hp_path_on_out_set(const stmdev_ctx_t *ctx,
                                      lsm6dsr_hp_slope_xl_en_t val)
{
  lsm6dsr_ctrl8_xl_t ctrl8_xl;
  int32_t ret;

  ret = lsm6dsr_read_reg(ctx, LSM6DSR_CTRL8_XL,
                         (uint8_t *)&ctrl8_xl, 1);

  if (ret == 0)
  {
    ctrl8_xl.hp_slope_xl_en = (((uint8_t)val & 0x10U) >> 4);
    ctrl8_xl.hp_ref_mode_xl = (((uint8_t)val & 0x20U) >> 5);
    ctrl8_xl.hpcf_xl = (uint8_t)val & 0x07U;
    ret = lsm6dsr_write_reg(ctx, LSM6DSR_CTRL8_XL,
                            (uint8_t *)&ctrl8_xl, 1);
  }

  return ret;
}

/**
  * @brief  Accelerometer slope filter / high-pass filter selection on
  *         output.[get]
  *
  * @param  ctx    Read / write interface definitions.(ptr)
  * @param  val    Get the values of hp_slope_xl_en in reg CTRL8_XL
  * @retval        Interface status (MANDATORY: return 0 -> no Error).
  *
  */
int32_t lsm6dsr_xl_hp_path_on_out_get(const stmdev_ctx_t *ctx,
                                      lsm6dsr_hp_slope_xl_en_t *val)
{
  lsm6dsr_ctrl8_xl_t ctrl8_xl;
  int32_t ret;

  ret = lsm6dsr_read_reg(ctx, LSM6DSR_CTRL8_XL,
                         (uint8_t *)&ctrl8_xl, 1);

  switch (((ctrl8_xl.hp_ref_mode_xl << 5) + (ctrl8_xl.hp_slope_xl_en <<
                                             4) +
           ctrl8_xl.hpcf_xl))
  {
    case LSM6DSR_HP_PATH_DISABLE_ON_OUT:
      *val = LSM6DSR_HP_PATH_DISABLE_ON_OUT;
      break;

    case LSM6DSR_SLOPE_ODR_DIV_4:
      *val = LSM6DSR_SLOPE_ODR_DIV_4;
      break;

    case LSM6DSR_HP_ODR_DIV_10:
      *val = LSM6DSR_HP_ODR_DIV_10;
      break;

    case LSM6DSR_HP_ODR_DIV_20:
      *val = LSM6DSR_HP_ODR_DIV_20;
      break;

    case LSM6DSR_HP_ODR_DIV_45:
      *val = LSM6DSR_HP_ODR_DIV_45;
      break;

    case LSM6DSR_HP_ODR_DIV_100:
      *val = LSM6DSR_HP_ODR_DIV_100;
      break;

    case LSM6DSR_HP_ODR_DIV_200:
      *val = LSM6DSR_HP_ODR_DIV_200;
      break;

    case LSM6DSR_HP_ODR_DIV_400:
      *val = LSM6DSR_HP_ODR_DIV_400;
      break;

    case LSM6DSR_HP_ODR_DIV_800:
      *val = LSM6DSR_HP_ODR_DIV_800;
      break;

    case LSM6DSR_HP_REF_MD_ODR_DIV_10:
      *val = LSM6DSR_HP_REF_MD_ODR_DIV_10;
      break;

    case LSM6DSR_HP_REF_MD_ODR_DIV_20:
      *val = LSM6DSR_HP_REF_MD_ODR_DIV_20;
      break;

    case LSM6DSR_HP_REF_MD_ODR_DIV_45:
      *val = LSM6DSR_HP_REF_MD_ODR_DIV_45;
      break;

    case LSM6DSR_HP_REF_MD_ODR_DIV_100:
      *val = LSM6DSR_HP_REF_MD_ODR_DIV_100;
      break;

    case LSM6DSR_HP_REF_MD_ODR_DIV_200:
      *val = LSM6DSR_HP_REF_MD_ODR_DIV_200;
      break;

    case LSM6DSR_HP_REF_MD_ODR_DIV_400:
      *val = LSM6DSR_HP_REF_MD_ODR_DIV_400;
      break;

    case LSM6DSR_HP_REF_MD_ODR_DIV_800:
      *val = LSM6DSR_HP_REF_MD_ODR_DIV_800;
      break;

    case LSM6DSR_LP_ODR_DIV_10:
      *val = LSM6DSR_LP_ODR_DIV_10;
      break;

    case LSM6DSR_LP_ODR_DIV_20:
      *val = LSM6DSR_LP_ODR_DIV_20;
      break;

    case LSM6DSR_LP_ODR_DIV_45:
      *val = LSM6DSR_LP_ODR_DIV_45;
      break;

    case LSM6DSR_LP_ODR_DIV_100:
      *val = LSM6DSR_LP_ODR_DIV_100;
      break;

    case LSM6DSR_LP_ODR_DIV_200:
      *val = LSM6DSR_LP_ODR_DIV_200;
      break;

    case LSM6DSR_LP_ODR_DIV_400:
      *val = LSM6DSR_LP_ODR_DIV_400;
      break;

    case LSM6DSR_LP_ODR_DIV_800:
      *val = LSM6DSR_LP_ODR_DIV_800;
      break;

    default:
      *val = LSM6DSR_HP_PATH_DISABLE_ON_OUT;
      break;
  }

  return ret;
}

/**
  * @brief  Enables accelerometer LPF2 and HPF fast-settling mode.
  *         The filter sets the second samples after writing this bit.
  *         Active only during device exit from powerdown mode.[set]
  *
  * @param  ctx    Read / write interface definitions.(ptr)
  * @param  val    Change the values of fastsettl_mode_xl in reg CTRL8_XL
  * @retval        Interface status (MANDATORY: return 0 -> no Error).
  *
  */
int32_t lsm6dsr_xl_fast_settling_set(const stmdev_ctx_t *ctx,
                                     uint8_t val)
{
  lsm6dsr_ctrl8_xl_t ctrl8_xl;
  int32_t ret;

  ret = lsm6dsr_read_reg(ctx, LSM6DSR_CTRL8_XL,
                         (uint8_t *)&ctrl8_xl, 1);

  if (ret == 0)
  {
    ctrl8_xl.fastsettl_mode_xl = (uint8_t)val;
    ret = lsm6dsr_write_reg(ctx, LSM6DSR_CTRL8_XL,
                            (uint8_t *)&ctrl8_xl, 1);
  }

  return ret;
}

/**
  * @brief  Enables accelerometer LPF2 and HPF fast-settling mode.
  *         The filter sets the second samples after writing
  *         this bit. Active only during device exit from powerdown mode.[get]
  *
  * @param  ctx    Read / write interface definitions.(ptr)
  * @param  val    Change the values of fastsettl_mode_xl in reg CTRL8_XL
  * @retval        Interface status (MANDATORY: return 0 -> no Error).
  *
  */
int32_t lsm6dsr_xl_fast_settling_get(const stmdev_ctx_t *ctx,
                                     uint8_t *val)
{
  lsm6dsr_ctrl8_xl_t ctrl8_xl;
  int32_t ret;

  ret = lsm6dsr_read_reg(ctx, LSM6DSR_CTRL8_XL,
                         (uint8_t *)&ctrl8_xl, 1);
  *val = ctrl8_xl.fastsettl_mode_xl;

  return ret;
}

/**
  * @brief  HPF or SLOPE filter selection on wake-up and Activity/Inactivity
  *         functions.[set]
  *
  * @param  ctx    Read / write interface definitions.(ptr)
  * @param  val    Change the values of slope_fds in reg TAP_CFG0
  * @retval        Interface status (MANDATORY: return 0 -> no Error).
  *
  */
int32_t lsm6dsr_xl_hp_path_internal_set(const stmdev_ctx_t *ctx,
                                        lsm6dsr_slope_fds_t val)
{
  lsm6dsr_tap_cfg0_t tap_cfg0;
  int32_t ret;

  ret = lsm6dsr_read_reg(ctx, LSM6DSR_TAP_CFG0,
                         (uint8_t *)&tap_cfg0, 1);

  if (ret == 0)
  {
    tap_cfg0.slope_fds = (uint8_t)val;
    ret = lsm6dsr_write_reg(ctx, LSM6DSR_TAP_CFG0,
                            (uint8_t *)&tap_cfg0, 1);
  }

  return ret;
}

/**
  * @brief  HPF or SLOPE filter selection on wake-up and Activity/Inactivity
  *         functions.[get]
  *
  * @param  ctx    Read / write interface definitions.(ptr)
  * @param  val    Get the values of slope_fds in reg TAP_CFG0
  * @retval        Interface status (MANDATORY: return 0 -> no Error).
  *
  */
int32_t lsm6dsr_xl_hp_path_internal_get(const stmdev_ctx_t *ctx,
                                        lsm6dsr_slope_fds_t *val)
{
  lsm6dsr_tap_cfg0_t tap_cfg0;
  int32_t ret;

  ret = lsm6dsr_read_reg(ctx, LSM6DSR_TAP_CFG0,
                         (uint8_t *)&tap_cfg0, 1);

  switch (tap_cfg0.slope_fds)
  {
    case LSM6DSR_USE_SLOPE:
      *val = LSM6DSR_USE_SLOPE;
      break;

    case LSM6DSR_USE_HPF:
      *val = LSM6DSR_USE_HPF;
      break;

    default:
      *val = LSM6DSR_USE_SLOPE;
      break;
  }

  return ret;
}

/**
  * @brief  Enables gyroscope digital high-pass filter. The filter is enabled
  *         only if the gyro is in HP mode.[set]
  *
  * @param  ctx    Read / write interface definitions.(ptr)
  * @param  val    Get the values of hp_en_g and hp_en_g in reg CTRL7_G
  * @retval        Interface status (MANDATORY: return 0 -> no Error).
  *
  */
int32_t lsm6dsr_gy_hp_path_internal_set(const stmdev_ctx_t *ctx,
                                        lsm6dsr_hpm_g_t val)
{
  lsm6dsr_ctrl7_g_t ctrl7_g;
  int32_t ret;

  ret = lsm6dsr_read_reg(ctx, LSM6DSR_CTRL7_G,
                         (uint8_t *)&ctrl7_g, 1);

  if (ret == 0)
  {
    ctrl7_g.hp_en_g = (((uint8_t)val & 0x80U) >> 7);
    ctrl7_g.hpm_g = (uint8_t)val & 0x03U;
    ret = lsm6dsr_write_reg(ctx, LSM6DSR_CTRL7_G,
                            (uint8_t *)&ctrl7_g, 1);
  }

  return ret;
}

/**
  * @brief    Enables gyroscope digital high-pass filter. The filter is
  *           enabled only if the gyro is in HP mode.[get]
  *
  * @param  ctx    Read / write interface definitions.(ptr)
  * @param  val    Get the values of hp_en_g and hp_en_g in reg CTRL7_G
  * @retval        Interface status (MANDATORY: return 0 -> no Error).
  *
  */
int32_t lsm6dsr_gy_hp_path_internal_get(const stmdev_ctx_t *ctx,
                                        lsm6dsr_hpm_g_t *val)
{
  lsm6dsr_ctrl7_g_t ctrl7_g;
  int32_t ret;

  ret = lsm6dsr_read_reg(ctx, LSM6DSR_CTRL7_G,
                         (uint8_t *)&ctrl7_g, 1);

  switch ((ctrl7_g.hp_en_g << 7) + ctrl7_g.hpm_g)
  {
    case LSM6DSR_HP_FILTER_NONE:
      *val = LSM6DSR_HP_FILTER_NONE;
      break;

    case LSM6DSR_HP_FILTER_16mHz:
      *val = LSM6DSR_HP_FILTER_16mHz;
      break;

    case LSM6DSR_HP_FILTER_65mHz:
      *val = LSM6DSR_HP_FILTER_65mHz;
      break;

    case LSM6DSR_HP_FILTER_260mHz:
      *val = LSM6DSR_HP_FILTER_260mHz;
      break;

    case LSM6DSR_HP_FILTER_1Hz04:
      *val = LSM6DSR_HP_FILTER_1Hz04;
      break;

    default:
      *val = LSM6DSR_HP_FILTER_NONE;
      break;
  }

  return ret;
}

/**
  * @}
  *
  */

/**
  * @defgroup   LSM6DSR_ Auxiliary_interface
  * @brief      This section groups all the functions concerning
  *             auxiliary interface.
  * @{
  *
  */

/**
  * @brief  On auxiliary interface connect/disconnect SDO and OCS
  *         internal pull-up.[set]
  *
  * @param  ctx    Read / write interface definitions.(ptr)
  * @param  val    Change the values of ois_pu_dis in reg PIN_CTRL
  * @retval        Interface status (MANDATORY: return 0 -> no Error).
  *
  */
int32_t lsm6dsr_aux_sdo_ocs_mode_set(const stmdev_ctx_t *ctx,
                                     lsm6dsr_ois_pu_dis_t val)
{
  lsm6dsr_pin_ctrl_t pin_ctrl;
  int32_t ret;

  ret = lsm6dsr_read_reg(ctx, LSM6DSR_PIN_CTRL,
                         (uint8_t *)&pin_ctrl, 1);

  if (ret == 0)
  {
    pin_ctrl.ois_pu_dis = (uint8_t)val;
    ret = lsm6dsr_write_reg(ctx, LSM6DSR_PIN_CTRL,
                            (uint8_t *)&pin_ctrl, 1);
  }

  return ret;
}

/**
  * @brief  On auxiliary interface connect/disconnect SDO and OCS
  *         internal pull-up.[get]
  *
  * @param  ctx    Read / write interface definitions.(ptr)
  * @param  val    Get the values of ois_pu_dis in reg PIN_CTRL
  * @retval        Interface status (MANDATORY: return 0 -> no Error).
  *
  */
int32_t lsm6dsr_aux_sdo_ocs_mode_get(const stmdev_ctx_t *ctx,
                                     lsm6dsr_ois_pu_dis_t *val)
{
  lsm6dsr_pin_ctrl_t pin_ctrl;
  int32_t ret;

  ret = lsm6dsr_read_reg(ctx, LSM6DSR_PIN_CTRL,
                         (uint8_t *)&pin_ctrl, 1);

  switch (pin_ctrl.ois_pu_dis)
  {
    case LSM6DSR_AUX_PULL_UP_DISC:
      *val = LSM6DSR_AUX_PULL_UP_DISC;
      break;

    case LSM6DSR_AUX_PULL_UP_CONNECT:
      *val = LSM6DSR_AUX_PULL_UP_CONNECT;
      break;

    default:
      *val = LSM6DSR_AUX_PULL_UP_DISC;
      break;
  }

  return ret;
}

/**
  * @brief  OIS chain on aux interface power on mode.[set]
  *
  * @param  ctx    Read / write interface definitions.(ptr)
  * @param  val    Change the values of ois_on in reg CTRL7_G
  * @retval        Interface status (MANDATORY: return 0 -> no Error).
  *
  */
int32_t lsm6dsr_aux_pw_on_ctrl_set(const stmdev_ctx_t *ctx,
                                   lsm6dsr_ois_on_t val)
{
  lsm6dsr_ctrl7_g_t ctrl7_g;
  int32_t ret;

  ret = lsm6dsr_read_reg(ctx, LSM6DSR_CTRL7_G,
                         (uint8_t *)&ctrl7_g, 1);

  if (ret == 0)
  {
    ctrl7_g.ois_on_en = (uint8_t)val & 0x01U;
    ctrl7_g.ois_on = (uint8_t)val & 0x01U;
    ret = lsm6dsr_write_reg(ctx, LSM6DSR_CTRL7_G,
                            (uint8_t *)&ctrl7_g, 1);
  }

  return ret;
}

/**
  * @brief  OIS chain on aux interface power on mode[get]
  *
  * @param  ctx    Read / write interface definitions.(ptr)
  * @param  val    Get the values of ois_on in reg CTRL7_G
  * @retval        Interface status (MANDATORY: return 0 -> no Error).
  *
  */
int32_t lsm6dsr_aux_pw_on_ctrl_get(const stmdev_ctx_t *ctx,
                                   lsm6dsr_ois_on_t *val)
{
  lsm6dsr_ctrl7_g_t ctrl7_g;
  int32_t ret;

  ret = lsm6dsr_read_reg(ctx, LSM6DSR_CTRL7_G,
                         (uint8_t *)&ctrl7_g, 1);

  switch (ctrl7_g.ois_on)
  {
    case LSM6DSR_AUX_ON:
      *val = LSM6DSR_AUX_ON;
      break;

    case LSM6DSR_AUX_ON_BY_AUX_INTERFACE:
      *val = LSM6DSR_AUX_ON_BY_AUX_INTERFACE;
      break;

    default:
      *val = LSM6DSR_AUX_ON;
      break;
  }

  return ret;
}

/**
  * @brief  The STATUS_SPIAux register is read by the auxiliary SPI.[get]
  *
  * @param  ctx    Read / write interface definitions.(ptr)
  * @param  lsm6dsr_status_spiaux_t: registers STATUS_SPIAUX
  * @retval        Interface status (MANDATORY: return 0 -> no Error).
  *
  */
int32_t lsm6dsr_aux_status_reg_get(const stmdev_ctx_t *ctx,
                                   lsm6dsr_status_spiaux_t *val)
{
  int32_t ret;

  ret = lsm6dsr_read_reg(ctx, LSM6DSR_STATUS_SPIAUX,
                         (uint8_t *)val, 1);

  return ret;
}

/**
  * @brief  AUX accelerometer data available.[get]
  *
  * @param  ctx    Read / write interface definitions.(ptr)
  * @param  val    Change the values of xlda in reg STATUS_SPIAUX
  * @retval        Interface status (MANDATORY: return 0 -> no Error).
  *
  */
int32_t lsm6dsr_aux_xl_flag_data_ready_get(const stmdev_ctx_t *ctx,
                                           uint8_t *val)
{
  lsm6dsr_status_spiaux_t status_spiaux;
  int32_t ret;

  ret = lsm6dsr_read_reg(ctx, LSM6DSR_STATUS_SPIAUX,
                         (uint8_t *)&status_spiaux, 1);
  *val = status_spiaux.xlda;

  return ret;
}

/**
  * @brief  AUX gyroscope data available.[get]
  *
  * @param  ctx    Read / write interface definitions.(ptr)
  * @param  val    Change the values of gda in reg STATUS_SPIAUX
  * @retval        Interface status (MANDATORY: return 0 -> no Error).
  *
  */
int32_t lsm6dsr_aux_gy_flag_data_ready_get(const stmdev_ctx_t *ctx,
                                           uint8_t *val)
{
  lsm6dsr_status_spiaux_t status_spiaux;
  int32_t ret;

  ret = lsm6dsr_read_reg(ctx, LSM6DSR_STATUS_SPIAUX,
                         (uint8_t *)&status_spiaux, 1);
  *val = status_spiaux.gda;

  return ret;
}

/**
  * @brief  High when the gyroscope output is in the settling phase.[get]
  *
  * @param  ctx    Read / write interface definitions.(ptr)
  * @param  val    Change the values of gyro_settling in reg STATUS_SPIAUX
  * @retval        Interface status (MANDATORY: return 0 -> no Error).
  *
  */
int32_t lsm6dsr_aux_gy_flag_settling_get(const stmdev_ctx_t *ctx,
                                         uint8_t *val)
{
  lsm6dsr_status_spiaux_t status_spiaux;
  int32_t ret;

  ret = lsm6dsr_read_reg(ctx, LSM6DSR_STATUS_SPIAUX,
                         (uint8_t *)&status_spiaux, 1);
  *val = status_spiaux.gyro_settling;

  return ret;
}

/**
  * @brief  Selects accelerometer self-test. Effective only if XL OIS chain is
  *         enabled.[set]
  *
  * @param  ctx    Read / write interface definitions.(ptr)
  * @param  val    Change the values of st_xl_ois in reg INT_OIS
  * @retval        Interface status (MANDATORY: return 0 -> no Error).
  *
  */
int32_t lsm6dsr_aux_xl_self_test_set(const stmdev_ctx_t *ctx,
                                     lsm6dsr_st_xl_ois_t val)
{
  lsm6dsr_int_ois_t int_ois;
  int32_t ret;

  ret = lsm6dsr_read_reg(ctx, LSM6DSR_INT_OIS,
                         (uint8_t *)&int_ois, 1);

  if (ret == 0)
  {
    int_ois.st_xl_ois = (uint8_t)val;
    ret = lsm6dsr_write_reg(ctx, LSM6DSR_INT_OIS,
                            (uint8_t *)&int_ois, 1);
  }

  return ret;
}

/**
  * @brief  Selects accelerometer self-test. Effective only if XL OIS chain
  *         is enabled.[get]
  *
  * @param  ctx    Read / write interface definitions.(ptr)
  * @param  val    Get the values of st_xl_ois in reg INT_OIS
  * @retval        Interface status (MANDATORY: return 0 -> no Error).
  *
  */
int32_t lsm6dsr_aux_xl_self_test_get(const stmdev_ctx_t *ctx,
                                     lsm6dsr_st_xl_ois_t *val)
{
  lsm6dsr_int_ois_t int_ois;
  int32_t ret;

  ret = lsm6dsr_read_reg(ctx, LSM6DSR_INT_OIS,
                         (uint8_t *)&int_ois, 1);

  switch (int_ois.st_xl_ois)
  {
    case LSM6DSR_AUX_XL_DISABLE:
      *val = LSM6DSR_AUX_XL_DISABLE;
      break;

    case LSM6DSR_AUX_XL_POS:
      *val = LSM6DSR_AUX_XL_POS;
      break;

    case LSM6DSR_AUX_XL_NEG:
      *val = LSM6DSR_AUX_XL_NEG;
      break;

    default:
      *val = LSM6DSR_AUX_XL_DISABLE;
      break;
  }

  return ret;
}

/**
  * @brief  Indicates polarity of DEN signal on OIS chain.[set]
  *
  * @param  ctx    Read / write interface definitions.(ptr)
  * @param  val    Change the values of den_lh_ois in reg INT_OIS
  * @retval        Interface status (MANDATORY: return 0 -> no Error).
  *
  */
int32_t lsm6dsr_aux_den_polarity_set(const stmdev_ctx_t *ctx,
                                     lsm6dsr_den_lh_ois_t val)
{
  lsm6dsr_int_ois_t int_ois;
  int32_t ret;

  ret = lsm6dsr_read_reg(ctx, LSM6DSR_INT_OIS,
                         (uint8_t *)&int_ois, 1);

  if (ret == 0)
  {
    int_ois.den_lh_ois = (uint8_t)val;
    ret = lsm6dsr_write_reg(ctx, LSM6DSR_INT_OIS,
                            (uint8_t *)&int_ois, 1);
  }

  return ret;
}

/**
  * @brief  Indicates polarity of DEN signal on OIS chain.[get]
  *
  * @param  ctx    Read / write interface definitions.(ptr)
  * @param  val    Get the values of den_lh_ois in reg INT_OIS
  * @retval        Interface status (MANDATORY: return 0 -> no Error).
  *
  */
int32_t lsm6dsr_aux_den_polarity_get(const stmdev_ctx_t *ctx,
                                     lsm6dsr_den_lh_ois_t *val)
{
  lsm6dsr_int_ois_t int_ois;
  int32_t ret;

  ret = lsm6dsr_read_reg(ctx, LSM6DSR_INT_OIS,
                         (uint8_t *)&int_ois, 1);

  switch (int_ois.den_lh_ois)
  {
    case LSM6DSR_AUX_DEN_ACTIVE_LOW:
      *val = LSM6DSR_AUX_DEN_ACTIVE_LOW;
      break;

    case LSM6DSR_AUX_DEN_ACTIVE_HIGH:
      *val = LSM6DSR_AUX_DEN_ACTIVE_HIGH;
      break;

    default:
      *val = LSM6DSR_AUX_DEN_ACTIVE_LOW;
      break;
  }

  return ret;
}

/**
  * @brief  Configure DEN mode on the OIS chain.[set]
  *
  * @param  ctx    Read / write interface definitions.(ptr)
  * @param  val    Change the values of lvl2_ois in reg INT_OIS
  * @retval        Interface status (MANDATORY: return 0 -> no Error).
  *
  */
int32_t lsm6dsr_aux_den_mode_set(const stmdev_ctx_t *ctx,
                                 lsm6dsr_lvl2_ois_t val)
{
  lsm6dsr_int_ois_t int_ois;
  lsm6dsr_ctrl1_ois_t ctrl1_ois;
  int32_t ret;

  ret = lsm6dsr_read_reg(ctx, LSM6DSR_INT_OIS,
                         (uint8_t *)&int_ois, 1);

  if (ret == 0)
  {
    int_ois.lvl2_ois = (uint8_t)val & 0x01U;
    ret = lsm6dsr_write_reg(ctx, LSM6DSR_INT_OIS,
                            (uint8_t *)&int_ois, 1);
  }

  if (ret == 0)
  {
    ret = lsm6dsr_read_reg(ctx, LSM6DSR_CTRL1_OIS,
                           (uint8_t *)&ctrl1_ois, 1);
  }

  if (ret == 0)
  {
    ctrl1_ois.lvl1_ois = ((uint8_t)val & 0x02U) >> 1;
    ret = lsm6dsr_write_reg(ctx, LSM6DSR_CTRL1_OIS,
                            (uint8_t *)&ctrl1_ois, 1);
  }

  return ret;
}

/**
  * @brief  Configure DEN mode on the OIS chain.[get]
  *
  * @param  ctx    Read / write interface definitions.(ptr)
  * @param  val    Get the values of lvl2_ois in reg INT_OIS
  * @retval        Interface status (MANDATORY: return 0 -> no Error).
  *
  */
int32_t lsm6dsr_aux_den_mode_get(const stmdev_ctx_t *ctx,
                                 lsm6dsr_lvl2_ois_t *val)
{
  lsm6dsr_int_ois_t int_ois;
  lsm6dsr_ctrl1_ois_t ctrl1_ois;
  int32_t ret;

  ret = lsm6dsr_read_reg(ctx, LSM6DSR_INT_OIS,
                         (uint8_t *)&int_ois, 1);

  if (ret == 0)
  {
    ret = lsm6dsr_read_reg(ctx, LSM6DSR_CTRL1_OIS,
                           (uint8_t *)&ctrl1_ois, 1);
  }

  switch ((ctrl1_ois.lvl1_ois << 1) + int_ois.lvl2_ois)
  {
    case LSM6DSR_AUX_DEN_DISABLE:
      *val = LSM6DSR_AUX_DEN_DISABLE;
      break;

    case LSM6DSR_AUX_DEN_LEVEL_LATCH:
      *val = LSM6DSR_AUX_DEN_LEVEL_LATCH;
      break;

    case LSM6DSR_AUX_DEN_LEVEL_TRIG:
      *val = LSM6DSR_AUX_DEN_LEVEL_TRIG;
      break;

    default:
      *val = LSM6DSR_AUX_DEN_DISABLE;
      break;
  }

  return ret;
}

/**
  * @brief  Enables/Disable OIS chain DRDY on INT2 pin. This setting has
  *         priority over all other INT2 settings.[set]
  *
  * @param  ctx    Read / write interface definitions.(ptr)
  * @param  val    Change the values of int2_drdy_ois in reg INT_OIS
  * @retval        Interface status (MANDATORY: return 0 -> no Error).
  *
  */
int32_t lsm6dsr_aux_drdy_on_int2_set(const stmdev_ctx_t *ctx,
                                     uint8_t val)
{
  lsm6dsr_int_ois_t int_ois;
  int32_t ret;

  ret = lsm6dsr_read_reg(ctx, LSM6DSR_INT_OIS,
                         (uint8_t *)&int_ois, 1);

  if (ret == 0)
  {
    int_ois.int2_drdy_ois = (uint8_t)val;
    ret = lsm6dsr_write_reg(ctx, LSM6DSR_INT_OIS,
                            (uint8_t *)&int_ois, 1);
  }

  return ret;
}

/**
  * @brief  Enables/Disable OIS chain DRDY on INT2 pin. This setting has
  *         priority over all other INT2 settings.[get]
  *
  * @param  ctx    Read / write interface definitions.(ptr)
  * @param  val    Change the values of int2_drdy_ois in reg INT_OIS
  * @retval        Interface status (MANDATORY: return 0 -> no Error).
  *
  */
int32_t lsm6dsr_aux_drdy_on_int2_get(const stmdev_ctx_t *ctx,
                                     uint8_t *val)
{
  lsm6dsr_int_ois_t int_ois;
  int32_t ret;

  ret = lsm6dsr_read_reg(ctx, LSM6DSR_INT_OIS,
                         (uint8_t *)&int_ois, 1);
  *val = int_ois.int2_drdy_ois;

  return ret;
}

/**
  * @brief  Enables OIS chain data processing for gyro in Mode 3 and Mode 4
  *         (mode4_en = 1) and accelerometer data in and Mode 4 (mode4_en = 1).
  *         When the OIS chain is enabled, the OIS outputs are available
  *         through the SPI2 in registers OUTX_L_G (22h) through OUTZ_H_G(27h)
  *         and STATUS_REG (1Eh) / STATUS_SPIAux, and LPF1 is dedicated to
  *         this chain.[set]
  *
  * @param  ctx    Read / write interface definitions.(ptr)
  * @param  val    Change the values of ois_en_spi2 in reg CTRL1_OIS
  * @retval        Interface status (MANDATORY: return 0 -> no Error).
  *
  */
int32_t lsm6dsr_aux_mode_set(const stmdev_ctx_t *ctx,
                             lsm6dsr_ois_en_spi2_t val)
{
  lsm6dsr_ctrl1_ois_t ctrl1_ois;
  int32_t ret;

  ret = lsm6dsr_read_reg(ctx, LSM6DSR_CTRL1_OIS,
                         (uint8_t *)&ctrl1_ois, 1);

  if (ret == 0)
  {
    ctrl1_ois.ois_en_spi2 = (uint8_t)val & 0x01U;
    ctrl1_ois.mode4_en = ((uint8_t)val & 0x02U) >> 1;
    ret = lsm6dsr_write_reg(ctx, LSM6DSR_CTRL1_OIS,
                            (uint8_t *)&ctrl1_ois, 1);
  }

  return ret;
}

/**
  * @brief  Enables OIS chain data processing for gyro in Mode 3 and Mode 4
  *         (mode4_en = 1) and accelerometer data in and Mode 4 (mode4_en = 1).
  *         When the OIS chain is enabled, the OIS outputs are available
  *         through the SPI2 in registers OUTX_L_G (22h) through OUTZ_H_G(27h)
  *         and STATUS_REG (1Eh) / STATUS_SPIAux, and LPF1 is dedicated to
  *         this chain.[get]
  *
  * @param  ctx    Read / write interface definitions.(ptr)
  * @param  val    Get the values of ois_en_spi2 in
  *                                reg CTRL1_OIS
  * @retval        Interface status (MANDATORY: return 0 -> no Error).
  *
  */
int32_t lsm6dsr_aux_mode_get(const stmdev_ctx_t *ctx,
                             lsm6dsr_ois_en_spi2_t *val)
{
  lsm6dsr_ctrl1_ois_t ctrl1_ois;
  int32_t ret;

  ret = lsm6dsr_read_reg(ctx, LSM6DSR_CTRL1_OIS,
                         (uint8_t *)&ctrl1_ois, 1);

  switch (((ctrl1_ois.mode4_en << 1) + ctrl1_ois.ois_en_spi2))
  {
    case LSM6DSR_AUX_DISABLE:
      *val = LSM6DSR_AUX_DISABLE;
      break;

    case LSM6DSR_MODE_3_GY:
      *val = LSM6DSR_MODE_3_GY;
      break;

    case LSM6DSR_MODE_4_GY_XL:
      *val = LSM6DSR_MODE_4_GY_XL;
      break;

    default:
      *val = LSM6DSR_AUX_DISABLE;
      break;
  }

  return ret;
}

/**
  * @brief  Selects gyroscope OIS chain full-scale.[set]
  *
  * @param  ctx    Read / write interface definitions.(ptr)
  * @param  val    Change the values of fs_g_ois in reg CTRL1_OIS
  * @retval        Interface status (MANDATORY: return 0 -> no Error).
  *
  */
int32_t lsm6dsr_aux_gy_full_scale_set(const stmdev_ctx_t *ctx,
                                      lsm6dsr_fs_g_ois_t val)
{
  lsm6dsr_ctrl1_ois_t ctrl1_ois;
  int32_t ret;

  ret = lsm6dsr_read_reg(ctx, LSM6DSR_CTRL1_OIS,
                         (uint8_t *)&ctrl1_ois, 1);

  if (ret == 0)
  {
    ctrl1_ois.fs_g_ois = (uint8_t)val & 0x03U;
    ctrl1_ois.fs_125_ois = ((uint8_t)val & 0x04U) >> 2;
    ret = lsm6dsr_write_reg(ctx, LSM6DSR_CTRL1_OIS,
                            (uint8_t *)&ctrl1_ois, 1);
  }

  return ret;
}

/**
  * @brief  Selects gyroscope OIS chain full-scale.[get]
  *
  * @param  ctx    Read / write interface definitions.(ptr)
  * @param  val    Get the values of fs_g_ois in reg CTRL1_OIS
  * @retval        Interface status (MANDATORY: return 0 -> no Error).
  *
  */
int32_t lsm6dsr_aux_gy_full_scale_get(const stmdev_ctx_t *ctx,
                                      lsm6dsr_fs_g_ois_t *val)
{
  lsm6dsr_ctrl1_ois_t ctrl1_ois;
  int32_t ret;

  ret = lsm6dsr_read_reg(ctx, LSM6DSR_CTRL1_OIS,
                         (uint8_t *)&ctrl1_ois, 1);

  switch ((ctrl1_ois.fs_125_ois << 2) + ctrl1_ois.fs_g_ois)
  {
    case LSM6DSR_250dps_AUX:
      *val = LSM6DSR_250dps_AUX;
      break;

    case LSM6DSR_125dps_AUX:
      *val = LSM6DSR_125dps_AUX;
      break;

    case LSM6DSR_500dps_AUX:
      *val = LSM6DSR_500dps_AUX;
      break;

    case LSM6DSR_1000dps_AUX:
      *val = LSM6DSR_1000dps_AUX;
      break;

    case LSM6DSR_2000dps_AUX:
      *val = LSM6DSR_2000dps_AUX;
      break;

    default:
      *val = LSM6DSR_250dps_AUX;
      break;
  }

  return ret;
}

/**
  * @brief  SPI2 3- or 4-wire interface.[set]
  *
  * @param  ctx    Read / write interface definitions.(ptr)
  * @param  val    Change the values of sim_ois in reg CTRL1_OIS
  * @retval        Interface status (MANDATORY: return 0 -> no Error).
  *
  */
int32_t lsm6dsr_aux_spi_mode_set(const stmdev_ctx_t *ctx,
                                 lsm6dsr_sim_ois_t val)
{
  lsm6dsr_ctrl1_ois_t ctrl1_ois;
  int32_t ret;

  ret = lsm6dsr_read_reg(ctx, LSM6DSR_CTRL1_OIS,
                         (uint8_t *)&ctrl1_ois, 1);

  if (ret == 0)
  {
    ctrl1_ois.sim_ois = (uint8_t)val;
    ret = lsm6dsr_write_reg(ctx, LSM6DSR_CTRL1_OIS,
                            (uint8_t *)&ctrl1_ois, 1);
  }

  return ret;
}

/**
  * @brief  SPI2 3- or 4-wire interface.[get]
  *
  * @param  ctx    Read / write interface definitions.(ptr)
  * @param  val    Get the values of sim_ois in reg CTRL1_OIS
  * @retval        Interface status (MANDATORY: return 0 -> no Error).
  *
  */
int32_t lsm6dsr_aux_spi_mode_get(const stmdev_ctx_t *ctx,
                                 lsm6dsr_sim_ois_t *val)
{
  lsm6dsr_ctrl1_ois_t ctrl1_ois;
  int32_t ret;

  ret = lsm6dsr_read_reg(ctx, LSM6DSR_CTRL1_OIS,
                         (uint8_t *)&ctrl1_ois, 1);

  switch (ctrl1_ois.sim_ois)
  {
    case LSM6DSR_AUX_SPI_4_WIRE:
      *val = LSM6DSR_AUX_SPI_4_WIRE;
      break;

    case LSM6DSR_AUX_SPI_3_WIRE:
      *val = LSM6DSR_AUX_SPI_3_WIRE;
      break;

    default:
      *val = LSM6DSR_AUX_SPI_4_WIRE;
      break;
  }

  return ret;
}

/**
  * @brief  Selects gyroscope digital LPF1 filter bandwidth.[set]
  *
  * @param  ctx    Read / write interface definitions.(ptr)
  * @param  val    Change the values of ftype_ois in reg CTRL2_OIS
  * @retval        Interface status (MANDATORY: return 0 -> no Error).
  *
  */
int32_t lsm6dsr_aux_gy_lp1_bandwidth_set(const stmdev_ctx_t *ctx,
                                         lsm6dsr_ftype_ois_t val)
{
  lsm6dsr_ctrl2_ois_t ctrl2_ois;
  int32_t ret;

  ret = lsm6dsr_read_reg(ctx, LSM6DSR_CTRL2_OIS,
                         (uint8_t *)&ctrl2_ois, 1);

  if (ret == 0)
  {
    ctrl2_ois.ftype_ois = (uint8_t)val;
    ret = lsm6dsr_write_reg(ctx, LSM6DSR_CTRL2_OIS,
                            (uint8_t *)&ctrl2_ois, 1);
  }

  return ret;
}

/**
  * @brief  Selects gyroscope digital LPF1 filter bandwidth.[get]
  *
  * @param  ctx    Read / write interface definitions.(ptr)
  * @param  val    Get the values of ftype_ois in reg CTRL2_OIS
  * @retval        Interface status (MANDATORY: return 0 -> no Error).
  *
  */
int32_t lsm6dsr_aux_gy_lp1_bandwidth_get(const stmdev_ctx_t *ctx,
                                         lsm6dsr_ftype_ois_t *val)
{
  lsm6dsr_ctrl2_ois_t ctrl2_ois;
  int32_t ret;

  ret = lsm6dsr_read_reg(ctx, LSM6DSR_CTRL2_OIS,
                         (uint8_t *)&ctrl2_ois, 1);

  switch (ctrl2_ois.ftype_ois)
  {
    case LSM6DSR_351Hz39:
      *val = LSM6DSR_351Hz39;
      break;

    case LSM6DSR_236Hz63:
      *val = LSM6DSR_236Hz63;
      break;

    case LSM6DSR_172Hz70:
      *val = LSM6DSR_172Hz70;
      break;

    case LSM6DSR_937Hz91:
      *val = LSM6DSR_937Hz91;
      break;

    default:
      *val = LSM6DSR_351Hz39;
      break;
  }

  return ret;
}

/**
  * @brief  Selects gyroscope OIS chain digital high-pass filter cutoff.[set]
  *
  * @param  ctx    Read / write interface definitions.(ptr)
  * @param  val    Change the values of hpm_ois in reg CTRL2_OIS
  * @retval        Interface status (MANDATORY: return 0 -> no Error).
  *
  */
int32_t lsm6dsr_aux_gy_hp_bandwidth_set(const stmdev_ctx_t *ctx,
                                        lsm6dsr_hpm_ois_t val)
{
  lsm6dsr_ctrl2_ois_t ctrl2_ois;
  int32_t ret;

  ret = lsm6dsr_read_reg(ctx, LSM6DSR_CTRL2_OIS,
                         (uint8_t *)&ctrl2_ois, 1);

  if (ret == 0)
  {
    ctrl2_ois.hpm_ois = (uint8_t)val & 0x03U;
    ctrl2_ois.hp_en_ois = ((uint8_t)val & 0x10U) >> 4;
    ret = lsm6dsr_write_reg(ctx, LSM6DSR_CTRL2_OIS,
                            (uint8_t *)&ctrl2_ois, 1);
  }

  return ret;
}

/**
  * @brief  Selects gyroscope OIS chain digital high-pass filter cutoff.[get]
  *
  * @param  ctx    Read / write interface definitions.(ptr)
  * @param  val    Get the values of hpm_ois in reg CTRL2_OIS
  * @retval        Interface status (MANDATORY: return 0 -> no Error).
  *
  */
int32_t lsm6dsr_aux_gy_hp_bandwidth_get(const stmdev_ctx_t *ctx,
                                        lsm6dsr_hpm_ois_t *val)
{
  lsm6dsr_ctrl2_ois_t ctrl2_ois;
  int32_t ret;

  ret = lsm6dsr_read_reg(ctx, LSM6DSR_CTRL2_OIS,
                         (uint8_t *)&ctrl2_ois, 1);

  switch ((ctrl2_ois.hp_en_ois << 4) + ctrl2_ois.hpm_ois)
  {
    case LSM6DSR_AUX_HP_DISABLE:
      *val = LSM6DSR_AUX_HP_DISABLE;
      break;

    case LSM6DSR_AUX_HP_Hz016:
      *val = LSM6DSR_AUX_HP_Hz016;
      break;

    case LSM6DSR_AUX_HP_Hz065:
      *val = LSM6DSR_AUX_HP_Hz065;
      break;

    case LSM6DSR_AUX_HP_Hz260:
      *val = LSM6DSR_AUX_HP_Hz260;
      break;

    case LSM6DSR_AUX_HP_1Hz040:
      *val = LSM6DSR_AUX_HP_1Hz040;
      break;

    default:
      *val = LSM6DSR_AUX_HP_DISABLE;
      break;
  }

  return ret;
}

/**
  * @brief  Enable / Disables OIS chain clamp. Enable: All OIS chain
  *         outputs = 8000h during self-test; Disable: OIS chain self-test
  *         outputs dependent from the aux gyro full scale selected.[set]
  *
  * @param  ctx    Read / write interface definitions.(ptr)
  * @param  val    Change the values of st_ois_clampdis in reg CTRL3_OIS
  * @retval        Interface status (MANDATORY: return 0 -> no Error).
  *
  */
int32_t lsm6dsr_aux_gy_clamp_set(const stmdev_ctx_t *ctx,
                                 lsm6dsr_st_ois_clampdis_t val)
{
  lsm6dsr_ctrl3_ois_t ctrl3_ois;
  int32_t ret;

  ret = lsm6dsr_read_reg(ctx, LSM6DSR_CTRL3_OIS,
                         (uint8_t *)&ctrl3_ois, 1);

  if (ret == 0)
  {
    ctrl3_ois.st_ois_clampdis = (uint8_t)val;
    ret = lsm6dsr_write_reg(ctx, LSM6DSR_CTRL3_OIS,
                            (uint8_t *)&ctrl3_ois, 1);
  }

  return ret;
}

/**
  * @brief  Enable / Disables OIS chain clamp. Enable: All OIS chain
  *         outputs = 8000h during self-test; Disable: OIS chain self-test
  *         outputs dependent from the aux gyro full scale selected.[get]
  *
  * @param  ctx    Read / write interface definitions.(ptr)
  * @param  val    Get the values of st_ois_clampdis in reg CTRL3_OIS
  * @retval        Interface status (MANDATORY: return 0 -> no Error).
  *
  */
int32_t lsm6dsr_aux_gy_clamp_get(const stmdev_ctx_t *ctx,
                                 lsm6dsr_st_ois_clampdis_t *val)
{
  lsm6dsr_ctrl3_ois_t ctrl3_ois;
  int32_t ret;

  ret = lsm6dsr_read_reg(ctx, LSM6DSR_CTRL3_OIS,
                         (uint8_t *)&ctrl3_ois, 1);

  switch (ctrl3_ois.st_ois_clampdis)
  {
    case LSM6DSR_ENABLE_CLAMP:
      *val = LSM6DSR_ENABLE_CLAMP;
      break;

    case LSM6DSR_DISABLE_CLAMP:
      *val = LSM6DSR_DISABLE_CLAMP;
      break;

    default:
      *val = LSM6DSR_ENABLE_CLAMP;
      break;
  }

  return ret;
}

/**
  * @brief  Selects gyroscope OIS chain self-test.[set]
  *
  * @param  ctx    Read / write interface definitions.(ptr)
  * @param  val    Change the values of st_ois in reg CTRL3_OIS
  * @retval        Interface status (MANDATORY: return 0 -> no Error).
  *
  */
int32_t lsm6dsr_aux_gy_self_test_set(const stmdev_ctx_t *ctx,
                                     lsm6dsr_st_ois_t val)
{
  lsm6dsr_ctrl3_ois_t ctrl3_ois;
  int32_t ret;

  ret = lsm6dsr_read_reg(ctx, LSM6DSR_CTRL3_OIS,
                         (uint8_t *)&ctrl3_ois, 1);

  if (ret == 0)
  {
    ctrl3_ois.st_ois = (uint8_t)val;
    ret = lsm6dsr_write_reg(ctx, LSM6DSR_CTRL3_OIS,
                            (uint8_t *)&ctrl3_ois, 1);
  }

  return ret;
}

/**
  * @brief  Selects gyroscope OIS chain self-test.[get]
  *
  * @param  ctx    Read / write interface definitions.(ptr)
  * @param  val    Get the values of st_ois in reg CTRL3_OIS
  * @retval        Interface status (MANDATORY: return 0 -> no Error).
  *
  */
int32_t lsm6dsr_aux_gy_self_test_get(const stmdev_ctx_t *ctx,
                                     lsm6dsr_st_ois_t *val)
{
  lsm6dsr_ctrl3_ois_t ctrl3_ois;
  int32_t ret;

  ret = lsm6dsr_read_reg(ctx, LSM6DSR_CTRL3_OIS,
                         (uint8_t *)&ctrl3_ois, 1);

  switch (ctrl3_ois.st_ois)
  {
    case LSM6DSR_AUX_GY_DISABLE:
      *val = LSM6DSR_AUX_GY_DISABLE;
      break;

    case LSM6DSR_AUX_GY_POS:
      *val = LSM6DSR_AUX_GY_POS;
      break;

    case LSM6DSR_AUX_GY_NEG:
      *val = LSM6DSR_AUX_GY_NEG;
      break;

    default:
      *val = LSM6DSR_AUX_GY_DISABLE;
      break;
  }

  return ret;
}

/**
  * @brief  Selects accelerometer OIS channel bandwidth.[set]
  *
  * @param  ctx    Read / write interface definitions.(ptr)
  * @param  val    Change the values of filter_xl_conf_ois in reg CTRL3_OIS
  * @retval        Interface status (MANDATORY: return 0 -> no Error).
  *
  */
int32_t lsm6dsr_aux_xl_bandwidth_set(const stmdev_ctx_t *ctx,
                                     lsm6dsr_filter_xl_conf_ois_t val)
{
  lsm6dsr_ctrl3_ois_t ctrl3_ois;
  int32_t ret;

  ret = lsm6dsr_read_reg(ctx, LSM6DSR_CTRL3_OIS,
                         (uint8_t *)&ctrl3_ois, 1);

  if (ret == 0)
  {
    ctrl3_ois.filter_xl_conf_ois = (uint8_t)val;
    ret = lsm6dsr_write_reg(ctx, LSM6DSR_CTRL3_OIS,
                            (uint8_t *)&ctrl3_ois, 1);
  }

  return ret;
}

/**
  * @brief  Selects accelerometer OIS channel bandwidth.[get]
  *
  * @param  ctx    Read / write interface definitions.(ptr)
  * @param  val    Get the values of filter_xl_conf_ois in reg CTRL3_OIS
  * @retval        Interface status (MANDATORY: return 0 -> no Error).
  *
  */
int32_t lsm6dsr_aux_xl_bandwidth_get(const stmdev_ctx_t *ctx,
                                     lsm6dsr_filter_xl_conf_ois_t *val)
{
  lsm6dsr_ctrl3_ois_t ctrl3_ois;
  int32_t ret;

  ret = lsm6dsr_read_reg(ctx, LSM6DSR_CTRL3_OIS,
                         (uint8_t *)&ctrl3_ois, 1);

  switch (ctrl3_ois.filter_xl_conf_ois)
  {
    case LSM6DSR_631Hz:
      *val = LSM6DSR_631Hz;
      break;

    case LSM6DSR_295Hz:
      *val = LSM6DSR_295Hz;
      break;

    case LSM6DSR_140Hz:
      *val = LSM6DSR_140Hz;
      break;

    case LSM6DSR_68Hz2:
      *val = LSM6DSR_68Hz2;
      break;

    case LSM6DSR_33Hz6:
      *val = LSM6DSR_33Hz6;
      break;

    case LSM6DSR_16Hz7:
      *val = LSM6DSR_16Hz7;
      break;

    case LSM6DSR_8Hz3:
      *val = LSM6DSR_8Hz3;
      break;

    case LSM6DSR_4Hz11:
      *val = LSM6DSR_4Hz11;
      break;

    default:
      *val = LSM6DSR_631Hz;
      break;
  }

  return ret;
}

/**
  * @brief  Selects accelerometer OIS channel full-scale.[set]
  *
  * @param  ctx    Read / write interface definitions.(ptr)
  * @param  val    Change the values of fs_xl_ois in reg CTRL3_OIS
  * @retval        Interface status (MANDATORY: return 0 -> no Error).
  *
  */
int32_t lsm6dsr_aux_xl_full_scale_set(const stmdev_ctx_t *ctx,
                                      lsm6dsr_fs_xl_ois_t val)
{
  lsm6dsr_ctrl3_ois_t ctrl3_ois;
  int32_t ret;

  ret = lsm6dsr_read_reg(ctx, LSM6DSR_CTRL3_OIS,
                         (uint8_t *)&ctrl3_ois, 1);

  if (ret == 0)
  {
    ctrl3_ois.fs_xl_ois = (uint8_t)val;
    ret = lsm6dsr_write_reg(ctx, LSM6DSR_CTRL3_OIS,
                            (uint8_t *)&ctrl3_ois, 1);
  }

  return ret;
}

/**
  * @brief  Selects accelerometer OIS channel full-scale.[get]
  *
  * @param  ctx    Read / write interface definitions.(ptr)
  * @param  val    Get the values of fs_xl_ois in reg CTRL3_OIS
  * @retval        Interface status (MANDATORY: return 0 -> no Error).
  *
  */
int32_t lsm6dsr_aux_xl_full_scale_get(const stmdev_ctx_t *ctx,
                                      lsm6dsr_fs_xl_ois_t *val)
{
  lsm6dsr_ctrl3_ois_t ctrl3_ois;
  int32_t ret;

  ret = lsm6dsr_read_reg(ctx, LSM6DSR_CTRL3_OIS,
                         (uint8_t *)&ctrl3_ois, 1);

  switch (ctrl3_ois.fs_xl_ois)
  {
    case LSM6DSR_AUX_2g:
      *val = LSM6DSR_AUX_2g;
      break;

    case LSM6DSR_AUX_16g:
      *val = LSM6DSR_AUX_16g;
      break;

    case LSM6DSR_AUX_4g:
      *val = LSM6DSR_AUX_4g;
      break;

    case LSM6DSR_AUX_8g:
      *val = LSM6DSR_AUX_8g;
      break;

    default:
      *val = LSM6DSR_AUX_2g;
      break;
  }

  return ret;
}

/**
  * @}
  *
  */

/**
  * @defgroup   LSM6DSR_ main_serial_interface
  * @brief      This section groups all the functions concerning main
  *             serial interface management (not auxiliary)
  * @{
  *
  */

/**
  * @brief  Connect/Disconnect SDO/SA0 internal pull-up.[set]
  *
  * @param  ctx    Read / write interface definitions.(ptr)
  * @param  val    Change the values of sdo_pu_en in reg PIN_CTRL
  * @retval        Interface status (MANDATORY: return 0 -> no Error).
  *
  */
int32_t lsm6dsr_sdo_sa0_mode_set(const stmdev_ctx_t *ctx,
                                 lsm6dsr_sdo_pu_en_t val)
{
  lsm6dsr_pin_ctrl_t pin_ctrl;
  int32_t ret;

  ret = lsm6dsr_read_reg(ctx, LSM6DSR_PIN_CTRL,
                         (uint8_t *)&pin_ctrl, 1);

  if (ret == 0)
  {
    pin_ctrl.sdo_pu_en = (uint8_t)val;
    ret = lsm6dsr_write_reg(ctx, LSM6DSR_PIN_CTRL,
                            (uint8_t *)&pin_ctrl, 1);
  }

  return ret;
}

/**
  * @brief  Connect/Disconnect SDO/SA0 internal pull-up.[get]
  *
  * @param  ctx    Read / write interface definitions.(ptr)
  * @param  val    Get the values of sdo_pu_en in reg PIN_CTRL
  * @retval        Interface status (MANDATORY: return 0 -> no Error).
  *
  */
int32_t lsm6dsr_sdo_sa0_mode_get(const stmdev_ctx_t *ctx,
                                 lsm6dsr_sdo_pu_en_t *val)
{
  lsm6dsr_pin_ctrl_t pin_ctrl;
  int32_t ret;

  ret = lsm6dsr_read_reg(ctx, LSM6DSR_PIN_CTRL,
                         (uint8_t *)&pin_ctrl, 1);

  switch (pin_ctrl.sdo_pu_en)
  {
    case LSM6DSR_PULL_UP_DISC:
      *val = LSM6DSR_PULL_UP_DISC;
      break;

    case LSM6DSR_PULL_UP_CONNECT:
      *val = LSM6DSR_PULL_UP_CONNECT;
      break;

    default:
      *val = LSM6DSR_PULL_UP_DISC;
      break;
  }

  return ret;
}

/**
  * @brief  Connect/Disconnect INT1 pull-down.[set]
  *
  * @param  ctx    Read / write interface definitions.(ptr)
  * @param  val    Change the values of pd_dis_int1 in reg I3C_BUS_AVB
  * @retval        Interface status (MANDATORY: return 0 -> no Error).
  *
  */
int32_t lsm6dsr_int1_mode_set(const stmdev_ctx_t *ctx,
                              lsm6dsr_pd_dis_int1_t val)
{
  lsm6dsr_i3c_bus_avb_t i3c_bus_avb;
  int32_t ret;

  ret = lsm6dsr_read_reg(ctx, LSM6DSR_I3C_BUS_AVB,
                         (uint8_t *)&i3c_bus_avb, 1);

  if (ret == 0)
  {
    i3c_bus_avb.pd_dis_int1 = (uint8_t)val;
    ret = lsm6dsr_write_reg(ctx, LSM6DSR_I3C_BUS_AVB,
                            (uint8_t *)&i3c_bus_avb, 1);
  }

  return ret;
}

/**
  * @brief  Connect/Disconnect INT1 pull-down.[get]
  *
  * @param  ctx    Read / write interface definitions.(ptr)
  * @param  val    Get the values of pd_dis_int1 in reg I3C_BUS_AVB
  * @retval        Interface status (MANDATORY: return 0 -> no Error).
  *
  */
int32_t lsm6dsr_int1_mode_get(const stmdev_ctx_t *ctx,
                              lsm6dsr_pd_dis_int1_t *val)
{
  lsm6dsr_i3c_bus_avb_t i3c_bus_avb;
  int32_t ret;

  ret = lsm6dsr_read_reg(ctx, LSM6DSR_I3C_BUS_AVB,
                         (uint8_t *)&i3c_bus_avb, 1);

  switch (i3c_bus_avb.pd_dis_int1)
  {
    case LSM6DSR_PULL_DOWN_CONNECT:
      *val = LSM6DSR_PULL_DOWN_CONNECT;
      break;

    case LSM6DSR_PULL_DOWN_DISC:
      *val = LSM6DSR_PULL_DOWN_DISC;
      break;

    default:
      *val = LSM6DSR_PULL_DOWN_CONNECT;
      break;
  }

  return ret;
}

/**
  * @brief  SPI Serial Interface Mode selection.[set]
  *
  * @param  ctx    Read / write interface definitions.(ptr)
  * @param  val    Change the values of sim in reg CTRL3_C
  * @retval        Interface status (MANDATORY: return 0 -> no Error).
  *
  */
int32_t lsm6dsr_spi_mode_set(const stmdev_ctx_t *ctx,
                             lsm6dsr_sim_t val)
{
  lsm6dsr_ctrl3_c_t ctrl3_c;
  int32_t ret;

  ret = lsm6dsr_read_reg(ctx, LSM6DSR_CTRL3_C,
                         (uint8_t *)&ctrl3_c, 1);

  if (ret == 0)
  {
    ctrl3_c.sim = (uint8_t)val;
    ret = lsm6dsr_write_reg(ctx, LSM6DSR_CTRL3_C,
                            (uint8_t *)&ctrl3_c, 1);
  }

  return ret;
}

/**
  * @brief  SPI Serial Interface Mode selection.[get]
  *
  * @param  ctx    Read / write interface definitions.(ptr)
  * @param  val    Get the values of sim in reg CTRL3_C
  * @retval        Interface status (MANDATORY: return 0 -> no Error).
  *
  */
int32_t lsm6dsr_spi_mode_get(const stmdev_ctx_t *ctx,
                             lsm6dsr_sim_t *val)
{
  lsm6dsr_ctrl3_c_t ctrl3_c;
  int32_t ret;

  ret = lsm6dsr_read_reg(ctx, LSM6DSR_CTRL3_C,
                         (uint8_t *)&ctrl3_c, 1);

  switch (ctrl3_c.sim)
  {
    case LSM6DSR_SPI_4_WIRE:
      *val = LSM6DSR_SPI_4_WIRE;
      break;

    case LSM6DSR_SPI_3_WIRE:
      *val = LSM6DSR_SPI_3_WIRE;
      break;

    default:
      *val = LSM6DSR_SPI_4_WIRE;
      break;
  }

  return ret;
}

/**
  * @brief  Disable / Enable I2C interface.[set]
  *
  * @param  ctx    Read / write interface definitions.(ptr)
  * @param  val    Change the values of i2c_disable in reg CTRL4_C
  * @retval        Interface status (MANDATORY: return 0 -> no Error).
  *
  */
int32_t lsm6dsr_i2c_interface_set(const stmdev_ctx_t *ctx,
                                  lsm6dsr_i2c_disable_t val)
{
  lsm6dsr_ctrl4_c_t ctrl4_c;
  int32_t ret;

  ret = lsm6dsr_read_reg(ctx, LSM6DSR_CTRL4_C,
                         (uint8_t *)&ctrl4_c, 1);

  if (ret == 0)
  {
    ctrl4_c.i2c_disable = (uint8_t)val;
    ret = lsm6dsr_write_reg(ctx, LSM6DSR_CTRL4_C,
                            (uint8_t *)&ctrl4_c, 1);
  }

  return ret;
}

/**
  * @brief  Disable / Enable I2C interface.[get]
  *
  * @param  ctx    Read / write interface definitions.(ptr)
  * @param  val    Get the values of i2c reg CTRL4_C
  * @retval        Interface status (MANDATORY: return 0 -> no Error).
  *
  */
int32_t lsm6dsr_i2c_interface_get(const stmdev_ctx_t *ctx,
                                  lsm6dsr_i2c_disable_t *val)
{
  lsm6dsr_ctrl4_c_t ctrl4_c;
  int32_t ret;

  ret = lsm6dsr_read_reg(ctx, LSM6DSR_CTRL4_C,
                         (uint8_t *)&ctrl4_c, 1);

  switch (ctrl4_c.i2c_disable)
  {
    case LSM6DSR_I2C_ENABLE:
      *val = LSM6DSR_I2C_ENABLE;
      break;

    case LSM6DSR_I2C_DISABLE:
      *val = LSM6DSR_I2C_DISABLE;
      break;

    default:
      *val = LSM6DSR_I2C_ENABLE;
      break;
  }

  return ret;
}

/**
  * @brief  I3C Enable/Disable communication protocol.[set]
  *
  * @param  ctx    Read / write interface definitions.(ptr)
  * @param  val    Change the values of i3c_disable in reg CTRL9_XL
  * @retval        Interface status (MANDATORY: return 0 -> no Error).
  *
  */
int32_t lsm6dsr_i3c_disable_set(const stmdev_ctx_t *ctx,
                                lsm6dsr_i3c_disable_t val)
{
  lsm6dsr_ctrl9_xl_t ctrl9_xl;
  lsm6dsr_i3c_bus_avb_t i3c_bus_avb;
  int32_t ret;

  ret = lsm6dsr_read_reg(ctx, LSM6DSR_CTRL9_XL, (uint8_t *)&ctrl9_xl, 1);

  if (ret == 0)
  {
    ctrl9_xl.i3c_disable = ((uint8_t)val & 0x80U) >> 7;
    ret = lsm6dsr_write_reg(ctx, LSM6DSR_CTRL9_XL,
                            (uint8_t *)&ctrl9_xl, 1);
  }

  if (ret == 0)
  {
    ret = lsm6dsr_read_reg(ctx, LSM6DSR_I3C_BUS_AVB,
                           (uint8_t *)&i3c_bus_avb, 1);
  }

  if (ret == 0)
  {
    i3c_bus_avb.i3c_bus_avb_sel = (uint8_t)val & 0x03U;
    ret = lsm6dsr_write_reg(ctx, LSM6DSR_I3C_BUS_AVB,
                            (uint8_t *)&i3c_bus_avb, 1);
  }

  return ret;
}

/**
  * @brief  I3C Enable/Disable communication protocol.[get]
  *
  * @param  ctx    Read / write interface definitions.(ptr)
  * @param  val    Change the values of i3c_disable in reg CTRL9_XL
  * @retval        Interface status (MANDATORY: return 0 -> no Error).
  *
  */
int32_t lsm6dsr_i3c_disable_get(const stmdev_ctx_t *ctx,
                                lsm6dsr_i3c_disable_t *val)
{
  lsm6dsr_ctrl9_xl_t ctrl9_xl;
  lsm6dsr_i3c_bus_avb_t i3c_bus_avb;
  int32_t ret;

  ret = lsm6dsr_read_reg(ctx, LSM6DSR_CTRL9_XL, (uint8_t *)&ctrl9_xl, 1);

  if (ret == 0)
  {
    ret = lsm6dsr_read_reg(ctx, LSM6DSR_I3C_BUS_AVB,
                           (uint8_t *)&i3c_bus_avb, 1);
  }

  switch ((ctrl9_xl.i3c_disable << 7) + i3c_bus_avb.i3c_bus_avb_sel)
  {
    case LSM6DSR_I3C_DISABLE:
      *val = LSM6DSR_I3C_DISABLE;
      break;

    case LSM6DSR_I3C_ENABLE_T_50us:
      *val = LSM6DSR_I3C_ENABLE_T_50us;
      break;

    case LSM6DSR_I3C_ENABLE_T_2us:
      *val = LSM6DSR_I3C_ENABLE_T_2us;
      break;

    case LSM6DSR_I3C_ENABLE_T_1ms:
      *val = LSM6DSR_I3C_ENABLE_T_1ms;
      break;

    case LSM6DSR_I3C_ENABLE_T_25ms:
      *val = LSM6DSR_I3C_ENABLE_T_25ms;
      break;

    default:
      *val = LSM6DSR_I3C_DISABLE;
      break;
  }

  return ret;
}

/**
  * @}
  *
  */

/**
  * @defgroup   LSM6DSR_interrupt_pins
  * @brief      This section groups all the functions that manage
  *             interrupt pins
  * @{
  *
  */

/**
  * @brief   Select the signal that need to route on int1 pad[set]
  *
  * @param  ctx    Read / write interface definitions.(ptr)
  * @param  val    Structure of registers: INT1_CTRL,MD1_CFG,
  *                EMB_FUNC_INT1, FSM_INT1_A, FSM_INT1_B
  * @retval        Interface status (MANDATORY: return 0 -> no Error).
  *
  */
int32_t lsm6dsr_pin_int1_route_set(const stmdev_ctx_t *ctx,
                                   lsm6dsr_pin_int1_route_t *val)
{
  lsm6dsr_tap_cfg2_t tap_cfg2;
  int32_t ret;

  ret = lsm6dsr_mem_bank_set(ctx, LSM6DSR_EMBEDDED_FUNC_BANK);

  if (ret == 0)
  {
    ret = lsm6dsr_write_reg(ctx, LSM6DSR_EMB_FUNC_INT1,
                            (uint8_t *)&val->emb_func_int1, 1);
  }

  if (ret == 0)
  {
    ret = lsm6dsr_write_reg(ctx, LSM6DSR_FSM_INT1_A,
                            (uint8_t *)&val->fsm_int1_a, 1);
  }

  if (ret == 0)
  {
    ret = lsm6dsr_write_reg(ctx, LSM6DSR_FSM_INT1_B,
                            (uint8_t *)&val->fsm_int1_b, 1);
  }

  if (ret == 0)
  {
    ret = lsm6dsr_mem_bank_set(ctx, LSM6DSR_USER_BANK);
  }

  if (ret == 0)
  {
    if ((val->emb_func_int1.int1_fsm_lc |
         val->emb_func_int1.int1_sig_mot |
         val->emb_func_int1.int1_step_detector |
         val->emb_func_int1.int1_tilt |
         val->fsm_int1_a.int1_fsm1 |
         val->fsm_int1_a.int1_fsm2 |
         val->fsm_int1_a.int1_fsm3 |
         val->fsm_int1_a.int1_fsm4 |
         val->fsm_int1_a.int1_fsm5 |
         val->fsm_int1_a.int1_fsm6 |
         val->fsm_int1_a.int1_fsm7 |
         val->fsm_int1_a.int1_fsm8 |
         val->fsm_int1_b.int1_fsm9 |
         val->fsm_int1_b.int1_fsm10 |
         val->fsm_int1_b.int1_fsm11 |
         val->fsm_int1_b.int1_fsm12 |
         val->fsm_int1_b.int1_fsm13 |
         val->fsm_int1_b.int1_fsm14 |
         val->fsm_int1_b.int1_fsm15 |
         val->fsm_int1_b.int1_fsm16) != PROPERTY_DISABLE)
    {
      val->md1_cfg.int1_emb_func = PROPERTY_ENABLE;
    }
    else
    {
      val->md1_cfg.int1_emb_func = PROPERTY_DISABLE;
    }

    ret = lsm6dsr_write_reg(ctx, LSM6DSR_INT1_CTRL,
                            (uint8_t *)&val->int1_ctrl, 1);
  }

  if (ret == 0)
  {
    ret = lsm6dsr_write_reg(ctx, LSM6DSR_MD1_CFG,
                            (uint8_t *)&val->md1_cfg, 1);
  }

  if (ret == 0)
  {
    ret = lsm6dsr_read_reg(ctx, LSM6DSR_TAP_CFG2,
                           (uint8_t *)&tap_cfg2, 1);

    if ((val->int1_ctrl.den_drdy_flag |
         val->int1_ctrl.int1_boot |
         val->int1_ctrl.int1_cnt_bdr |
         val->int1_ctrl.int1_drdy_g |
         val->int1_ctrl.int1_drdy_xl |
         val->int1_ctrl.int1_fifo_full |
         val->int1_ctrl.int1_fifo_ovr |
         val->int1_ctrl.int1_fifo_th |
         val->md1_cfg.int1_shub |
         val->md1_cfg.int1_6d |
         val->md1_cfg.int1_double_tap |
         val->md1_cfg.int1_ff |
         val->md1_cfg.int1_wu |
         val->md1_cfg.int1_single_tap |
         val->md1_cfg.int1_sleep_change) != PROPERTY_DISABLE)
    {
      tap_cfg2.interrupts_enable = PROPERTY_ENABLE;
    }

    else
    {
      tap_cfg2.interrupts_enable = PROPERTY_DISABLE;
    }
  }

  if (ret == 0)
  {
    ret = lsm6dsr_write_reg(ctx, LSM6DSR_TAP_CFG2,
                            (uint8_t *)&tap_cfg2, 1);
  }

  return ret;
}

/**
  * @brief  Select the signal that need to route on int1 pad.[get]
  *
  * @param  ctx    Read / write interface definitions.(ptr)
  * @param  val    Structure of registers: INT1_CTRL, MD1_CFG,
  *                EMB_FUNC_INT1, FSM_INT1_A, FSM_INT1_B.(ptr)
  * @retval        Interface status (MANDATORY: return 0 -> no Error).
  *
  */
int32_t lsm6dsr_pin_int1_route_get(const stmdev_ctx_t *ctx,
                                   lsm6dsr_pin_int1_route_t *val)
{
  int32_t ret;

  ret = lsm6dsr_mem_bank_set(ctx, LSM6DSR_EMBEDDED_FUNC_BANK);

  if (ret == 0)
  {
    ret = lsm6dsr_read_reg(ctx, LSM6DSR_EMB_FUNC_INT1,
                           (uint8_t *)&val->emb_func_int1, 1);
  }

  if (ret == 0)
  {
    ret = lsm6dsr_read_reg(ctx, LSM6DSR_FSM_INT1_A,
                           (uint8_t *)&val->fsm_int1_a, 1);
  }

  if (ret == 0)
  {
    ret = lsm6dsr_read_reg(ctx, LSM6DSR_FSM_INT1_B,
                           (uint8_t *)&val->fsm_int1_b, 1);
  }

  if (ret == 0)
  {
    ret = lsm6dsr_mem_bank_set(ctx, LSM6DSR_USER_BANK);
  }

  if (ret == 0)
  {
    ret = lsm6dsr_read_reg(ctx, LSM6DSR_INT1_CTRL,
                           (uint8_t *)&val->int1_ctrl, 1);
  }

  if (ret == 0)
  {
    ret = lsm6dsr_read_reg(ctx, LSM6DSR_MD1_CFG,
                           (uint8_t *)&val->md1_cfg, 1);
  }

  return ret;
}
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
